levi2234/ChimeraMultiFX/.isolated-review-2026-08-19/board-top.png

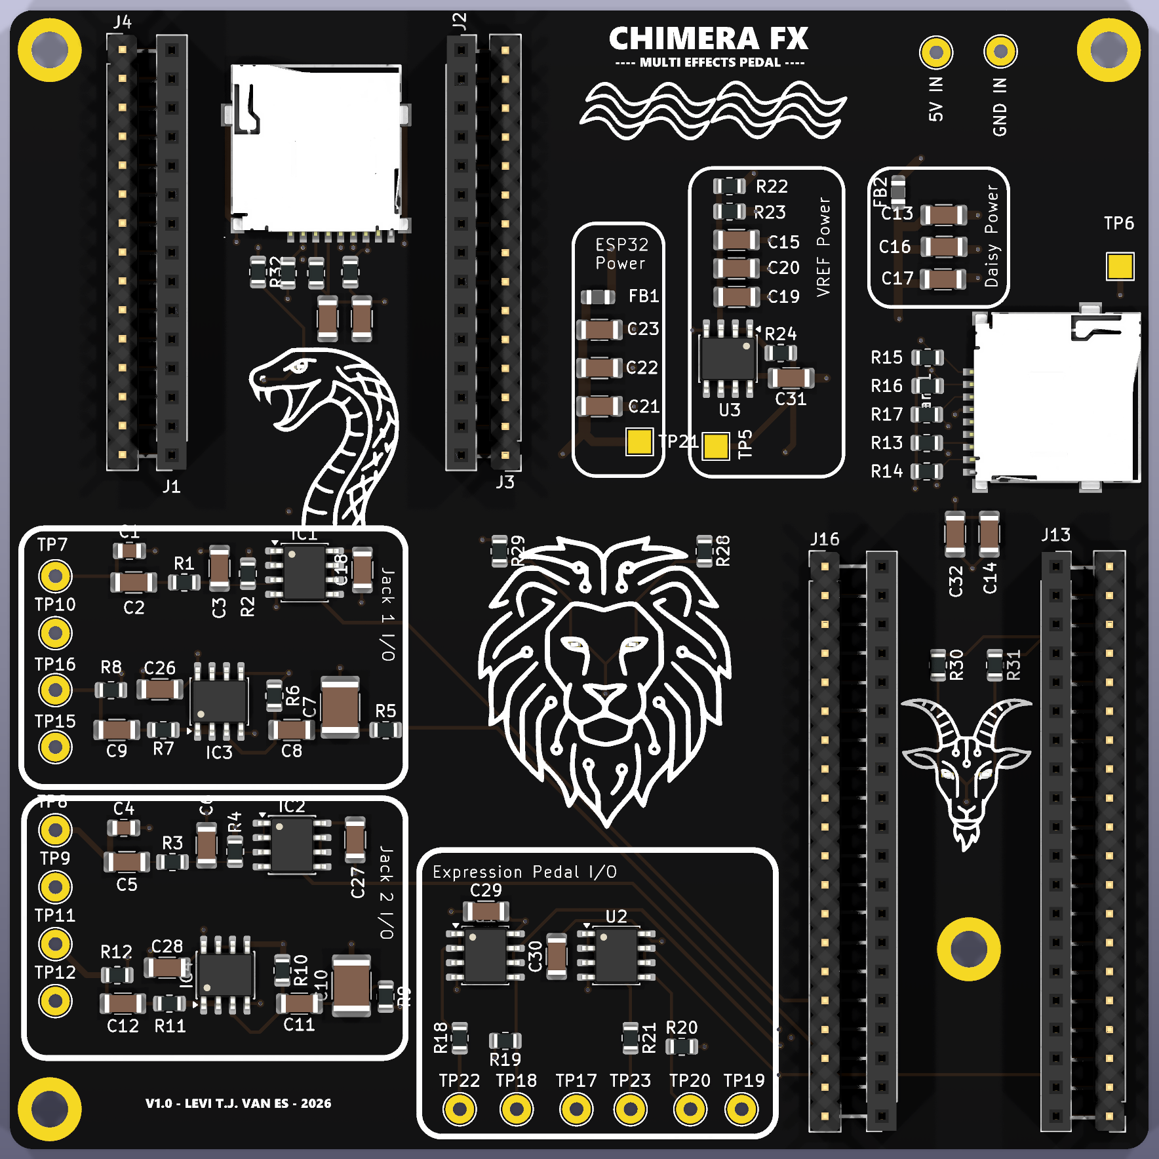
.isolated-review-2026-08-19/board-top.png
