levi2234/ChimeraMultiFX/firmware/daisy/include/effects/time/Delay.h

#pragma once
#include "daisy_seed.h"
#include "Effect.h"
#include <cstdint>
#include <cstring>

// Simple delay line with feedback.
class Delay : public Effect {
public:
    static constexpr uint32_t MAX_DELAY_SAMPLES = 96000 * 2; // 2s @ 96kHz

    void Init(float sample_rate) override {
        sample_rate_   = sample_rate;
        delay_time_    = 0.5f;
        feedback_      = 0.6f;
        mix_           = 0.4f;
        write_ptr_     = 0;
        delay_samples_ = (uint32_t)(delay_time_ * sample_rate_);
        if (delay_samples_ >= MAX_DELAY_SAMPLES)
            delay_samples_ = MAX_DELAY_SAMPLES - 1;

        for (uint32_t i = 0; i < MAX_DELAY_SAMPLES; i++)
            buffer_[i] = 0.0f;
    }

    float Process(float in) override {
        uint32_t read_ptr = (write_ptr_ - delay_samples_ + MAX_DELAY_SAMPLES) % MAX_DELAY_SAMPLES;
        float wet = buffer_[read_ptr];
        buffer_[write_ptr_] = in + (wet * feedback_);
        write_ptr_ = (write_ptr_ + 1) % MAX_DELAY_SAMPLES;
        return (in * (1.0f - mix_)) + (wet * mix_);
    }    const char* GetName() const override { return "delay"; }
    EffectCategory GetCategory() const override { return EffectCategory::Time; }

    void SetParam(const char* name, float value) override {
        if      (strcmp(name, "time") == 0)     SetDelayTime(value);
        else if (strcmp(name, "feedback") == 0) SetFeedback(value);
        else if (strcmp(name, "mix") == 0)      SetMix(value);
    }    float GetParam(const char* name) override {
        if      (strcmp(name, "time") == 0)     return delay_time_;
        else if (strcmp(name, "feedback") == 0) return feedback_;
        else if (strcmp(name, "mix") == 0)      return mix_;
        return 0.f;
    }

    const char* GetParamList() const override { return "time,feedback,mix"; }

    int GetParamCount() const override { return 3; }
    bool GetParamInfo(int index, EffectParamInfo& info) const override {
        switch (index) {
            case 0: info = {"time", "Time", "s", "float", "linear", 0.001f, (MAX_DELAY_SAMPLES - 1) / sample_rate_, 0.5f, 0.001f}; return true;
            case 1: info = {"feedback", "Feedback", "", "float", "linear", 0.0f, 0.95f, 0.6f, 0.01f}; return true;
            case 2: info = {"mix", "Mix", "", "float", "linear", 0.0f, 1.0f, 0.4f, 0.01f}; return true;
            default: return false;
        }
    }

    void SetDelayTime(float sec) {
        delay_time_ = Clamp(sec, 0.001f, (MAX_DELAY_SAMPLES - 1) / sample_rate_);
        delay_samples_ = (uint32_t)(delay_time_ * sample_rate_);
        if (delay_samples_ >= MAX_DELAY_SAMPLES)
            delay_samples_ = MAX_DELAY_SAMPLES - 1;
    }
    void SetFeedback(float fb) { feedback_ = Clamp(fb, 0.0f, 0.95f); }
    void SetMix(float m)       { mix_ = Clamp(m, 0.0f, 1.0f); }

private:
    float    sample_rate_   = 96000.f;
    float    delay_time_    = 0.5f;
    float    feedback_      = 0.6f;
    float    mix_           = 0.4f;
    uint32_t write_ptr_     = 0;
    uint32_t delay_samples_ = 0;

    static inline float DSY_SDRAM_BSS buffer_[MAX_DELAY_SAMPLES];
};
