levi2234/ChimeraMultiFX/firmware/daisy/Effect.h

#pragma once
#include <cstddef>
#include <cstring>

// Effect category tags — used for grouping and UI.
enum class EffectCategory {
    Distortion,
    Modulation,
    Time,
    Dynamics,
    Filter,
};

struct EffectParamInfo {
    const char* name;
    const char* label;
    const char* unit;
    const char* kind;
    const char* scale;
    float min;
    float max;
    float default_value;
    float step;
    const char* options;
};

// Base class for all ChimeraMultiFX effects.
// Each effect implements Init() and Process() and can be hot-swapped at runtime.
class Effect {
public:
    virtual ~Effect() {}

    // Called once when the effect is activated. sample_rate is in Hz.
    virtual void Init(float sample_rate) = 0;

    // Process a single mono sample and return the output.
    virtual float Process(float in) = 0;

    // Friendly name for display/debug purposes.
    virtual const char* GetName() const = 0;

    // Which family this effect belongs to.
    virtual EffectCategory GetCategory() const = 0;    // Parameter access by name — override in each effect for serial control
    virtual void  SetParam(const char* name, float value) { (void)name; (void)value; }
    virtual float GetParam(const char* name) { (void)name; return 0.f; }

    // Boolean parameter access — override for toggle-style params (e.g. "enabled")
    virtual void SetBoolParam(const char* name, bool value) { (void)name; (void)value; }
    virtual bool GetBoolParam(const char* name) { (void)name; return false; }

    // Returns a comma-separated list of parameter names (e.g. "drive,mix,level")
    virtual const char* GetParamList() const { return ""; }

    virtual int GetParamCount() const { return 0; }
    virtual bool GetParamInfo(int index, EffectParamInfo& info) const { (void)index; (void)info; return false; }

    // Per-effect bypass
    bool IsEnabled() const     { return enabled_; }
    void SetEnabled(bool e)    { enabled_ = e; }

    // Convenience: wraps Process() with bypass check
    float Tick(float in) {
        return enabled_ ? Process(in) : in;
    }

protected:
    static float Clamp(float value, float min, float max) {
        if (value < min) return min;
        if (value > max) return max;
        return value;
    }

    static int ClampInt(int value, int min, int max) {
        if (value < min) return min;
        if (value > max) return max;
        return value;
    }

    bool enabled_ = true;
};
