levi2234/ChimeraMultiFX/.agents/skills/kicad/scripts/analyze_pcb.py

#!/usr/bin/env python3
"""
KiCad PCB Layout Analyzer — comprehensive single-pass extraction.

Parses a .kicad_pcb file and outputs structured JSON with:
- Board dimensions and layer stack
- Footprint inventory (components, positions, pads, nets)
- Routing analysis (tracks, vias, zones)
- Net connectivity and unrouted nets
- Design rule summary
- Statistics

Usage:
    python analyze_pcb.py <file.kicad_pcb|file.kicad_pro|dir/> [--output file.json]
"""

import heapq
import json
import math
import os
import sys
from pathlib import Path

sys.path.insert(0, str(Path(__file__).parent))
import re

from sexp_parser import (
    find_all,
    find_first,
    get_at,
    get_property,
    get_value,
    parse_file,
)
from kicad_utils import (is_ground_name, is_power_net_name,
                         load_kicad_pro, extract_pro_net_classes,
                         extract_pro_design_rules, extract_pro_text_variables,
                         load_kicad_dru, load_lib_tables)
from pcb_connectivity import build_connectivity_graph
from finding_schema import compute_trust_summary, sort_findings, assign_finding_ids
from envelopes.pcb import PCBEnvelope
from schema_codec import emit_schema
from inputs_builder import build_inputs, build_compat
from capability_mode import get_capability_mode_ref

ANALYZER_SOURCE = "pcb"

# ---------------------------------------------------------------------------
# Geometry helpers
# ---------------------------------------------------------------------------

def _extract_polygon_coords(pts_node: list) -> list[tuple[float, float]]:
    """Extract (x, y) coordinate tuples from a (pts (xy x y) ...) node."""
    return [(float(xy[1]), float(xy[2])) for xy in find_all(pts_node, "xy")]


def _shoelace_area_from_coords(coords: list[tuple[float, float]]) -> float:
    """Compute polygon area from coordinate list using shoelace formula."""
    n = len(coords)
    if n < 3:
        return 0.0
    area = 0.0
    for i in range(n):
        j = (i + 1) % n
        area += coords[i][0] * coords[j][1] - coords[j][0] * coords[i][1]
    return abs(area) / 2.0


def _shoelace_area(pts_node: list) -> float:
    """Compute polygon area from a (pts (xy x y) ...) S-expression node.

    Returns positive area in mm².
    """
    return _shoelace_area_from_coords(_extract_polygon_coords(pts_node))


def _point_in_polygon(px: float, py: float,
                      polygon: list[tuple[float, float]]) -> bool:
    """Ray-casting point-in-polygon test.

    Returns True if point (px, py) is inside the polygon defined by
    a list of (x, y) vertices.
    """
    n = len(polygon)
    if n < 3:
        return False
    inside = False
    j = n - 1
    for i in range(n):
        xi, yi = polygon[i]
        xj, yj = polygon[j]
        if ((yi > py) != (yj > py)) and \
                (px < (xj - xi) * (py - yi) / (yj - yi) + xi):
            inside = not inside
        j = i
    return inside


def _polygon_bbox(
    coords: list[tuple[float, float]],
) -> tuple[float, float, float, float]:
    """Compute bounding box of a polygon.

    Returns (min_x, min_y, max_x, max_y).
    """
    xs = [p[0] for p in coords]
    ys = [p[1] for p in coords]
    return (min(xs), min(ys), max(xs), max(ys))


class ZoneFills:
    """Spatial index for zone filled polygon data.

    Stores filled polygon coordinates extracted during zone parsing.
    Used for point-in-polygon queries to determine actual copper presence
    at specific locations. Not included in JSON output (coordinates are
    too large — often thousands of vertices per fill region).

    Requires that zones have been filled in KiCad (Edit → Fill All Zones)
    before the PCB file was saved. Stale fills will produce incorrect results.
    """

    def __init__(self) -> None:
        self._fills: list[
            tuple[int, int, str, list[tuple[float, float]],
                  tuple[float, float, float, float]]
        ] = []
        self._next_fill_id = 0

    def add(self, zone_idx: int, layer: str,
            coords: list[tuple[float, float]]) -> None:
        """Register a filled polygon region for spatial queries."""
        bbox = _polygon_bbox(coords)
        fill_id = self._next_fill_id
        self._next_fill_id += 1
        self._fills.append((fill_id, zone_idx, layer, coords, bbox))

    @property
    def has_data(self) -> bool:
        """True if any filled polygon data was loaded."""
        return len(self._fills) > 0

    def zones_at_point(self, x: float, y: float, layer: str,
                       zones: list[dict]) -> list[dict]:
        """Return zone dicts that have filled copper at (x, y) on layer."""
        results = []
        seen: set[int] = set()
        for _fill_id, zone_idx, fill_layer, coords, bbox in self._fills:
            if fill_layer != layer or zone_idx in seen:
                continue
            # Fast bounding box rejection
            if x < bbox[0] or x > bbox[2] or y < bbox[1] or y > bbox[3]:
                continue
            if _point_in_polygon(x, y, coords):
                results.append(zones[zone_idx])
                seen.add(zone_idx)
        return results

    def fill_regions_at_point(self, x: float, y: float, layer: str,
                              zones: list[dict],
                              *,
                              net_name: str | None = None) -> list[tuple[int, int]]:
        """Return ``(fill_id, zone_idx)`` regions containing the point."""
        results: list[tuple[int, int]] = []
        for fill_id, zone_idx, fill_layer, coords, bbox in self._fills:
            if fill_layer != layer:
                continue
            if x < bbox[0] or x > bbox[2] or y < bbox[1] or y > bbox[3]:
                continue
            if not _point_in_polygon(x, y, coords):
                continue
            if net_name is not None and zones[zone_idx].get("net_name", "") != net_name:
                continue
            results.append((fill_id, zone_idx))
        return results

    def has_copper_at(self, x: float, y: float, layer: str) -> bool:
        """Check if any zone has filled copper at (x, y) on layer."""
        for _fill_id, _zone_idx, fill_layer, coords, bbox in self._fills:
            if fill_layer != layer:
                continue
            if x < bbox[0] or x > bbox[2] or y < bbox[1] or y > bbox[3]:
                continue
            if _point_in_polygon(x, y, coords):
                return True
        return False

    def zone_nets_at_point(self, x: float, y: float, layer: str,
                           zones: list[dict]) -> list[str]:
        """Return net names of zones with filled copper at (x, y) on layer."""
        return [z["net_name"] for z in self.zones_at_point(x, y, layer, zones)
                if z.get("net_name")]


def _dist_point_to_segment(px, py, x1, y1, x2, y2):
    """Distance from point (px, py) to line segment (x1,y1)-(x2,y2)."""
    # EQ-098: d = min(||P - (A + t(B-A))||) with t clamped to [0,1]
    # Source: Self-evident — 2D point-to-segment distance (project, clamp, Euclidean).
    dx, dy = x2 - x1, y2 - y1
    if dx == 0 and dy == 0:
        return math.sqrt((px - x1) ** 2 + (py - y1) ** 2)
    t = max(0.0, min(1.0, ((px - x1) * dx + (py - y1) * dy) / (dx * dx + dy * dy)))
    proj_x, proj_y = x1 + t * dx, y1 + t * dy
    return math.sqrt((px - proj_x) ** 2 + (py - proj_y) ** 2)


class CopperPresence:
    """Unified copper presence check across zones, tracks, and pads.

    Given a point (x, y) on a given layer, returns True if any copper
    object is within radius_mm.  Credits zone fills, track segments, and
    pads equally -- all provide valid return-current paths.

    Replaces bare ``ZoneFills.has_copper_at`` point-in-polygon checks
    that hit false negatives in KiCad zone fills (clearance channels
    carved around every track/pad make the filled polygon "swiss cheese";
    a sample point landing inside a clearance channel reports "no copper"
    even when GND fill is < 1 mm away).
    """

    def __init__(self, zone_fills, tracks_segments, footprints):
        self.zone_fills = zone_fills

        # Index track segments by layer for fast lookup
        self._tracks_by_layer = {}
        for seg in tracks_segments or []:
            layer = seg.get('layer')
            if layer:
                self._tracks_by_layer.setdefault(layer, []).append(seg)

        # Index pads by layer -- use absolute position (abs_x, abs_y)
        # and size (width, height) from extract_footprints() output
        self._pads_by_layer = {}
        for fp in footprints or []:
            for pad in fp.get('pads') or []:
                layers = pad.get('layers') or []
                px = pad.get('abs_x')
                py_val = pad.get('abs_y')
                if px is None or py_val is None:
                    continue
                pw = pad.get('width', 0)
                ph = pad.get('height', 0)
                for lyr in layers:
                    self._pads_by_layer.setdefault(lyr, []).append(
                        (px, py_val, pw, ph))

    # EQ-099: Perimeter sample at (x + r·cos(iπ/4), y + r·sin(iπ/4)) for i=0..7
    # Source: Self-evident — 8-point circle sampling at 45° intervals.
    def has_coverage_near(self, x, y, layer, *, radius_mm=0.5):
        """True if any copper on *layer* is within *radius_mm* of (x, y).

        Checks zone fills (center + 8-point perimeter), tracks, and pads.
        """
        zf = self.zone_fills
        if zf is not None and zf.has_data:
            # Center point -- fast path
            if zf.has_copper_at(x, y, layer):
                return True
            # 8-point perimeter at radius_mm
            for i in range(8):
                ang = i * math.pi / 4.0
                px = x + radius_mm * math.cos(ang)
                py = y + radius_mm * math.sin(ang)
                if zf.has_copper_at(px, py, layer):
                    return True

        # Track segments on this layer within radius
        for seg in self._tracks_by_layer.get(layer, []):
            half_w = seg.get('width', 0) / 2.0
            d = _dist_point_to_segment(
                x, y,
                seg.get('x1', 0), seg.get('y1', 0),
                seg.get('x2', 0), seg.get('y2', 0),
            )
            if d <= radius_mm + half_w:
                return True

        # Pads on this layer within radius
        for (pad_x, pad_y, pw, ph) in self._pads_by_layer.get(layer, []):
            half_diag = math.sqrt((pw / 2) ** 2 + (ph / 2) ** 2) if pw and ph else 0
            d = math.sqrt((x - pad_x) ** 2 + (y - pad_y) ** 2)
            if d <= radius_mm + half_diag:
                return True

        return False


def copper_connected(p1: tuple[float, float],
                     p2: tuple[float, float],
                     net: str,
                     layer: str,
                     zone_fills: "ZoneFills",
                     zones: list[dict],
                     *,
                     samples: int = 20) -> bool | None:
    """Check whether two points are joined by continuous same-net copper.

    Uses line-segment sampling through the ``ZoneFills`` spatial index to
    determine if a path between ``p1`` and ``p2`` stays entirely within a
    filled zone on ``net`` and ``layer``. This is a cheap approximation
    of a full copper connectivity graph — sufficient for verifying that
    a via near a thermal pad is actually copper-connected (fillet, flood,
    or cluster pattern) rather than sitting across a clearance slot.

    Args:
        p1: (x, y) of the first point in board coordinates (mm).
        p2: (x, y) of the second point in board coordinates (mm).
        net: Net name both points must share (e.g., "GND", "+3V3").
        layer: Copper layer name (e.g., "F.Cu", "B.Cu", "In1.Cu").
        zone_fills: ZoneFills spatial index from the PCB parser.
        zones: The full zone list the ZoneFills index was built from
            (needed for looking up net names attached to filled regions).
            Must be the same list returned alongside the ZoneFills
            instance during PCB parsing — mismatched pairs produce an
            IndexError deep inside ZoneFills.zones_at_point.
        samples: Number of sample points to test along the line segment,
            including both endpoints. Default 20 gives ~0.26 mm spacing
            on a 5 mm path (5 mm / 19 gaps). Increase for longer paths
            or tighter geometry; decrease for very short distances to
            save work.

    Returns:
        ``True`` if every sampled point along the segment lies in a filled
            zone whose net name matches ``net`` on ``layer``.
        ``False`` if any sample point is outside a same-net filled zone on
            ``layer`` (i.e., verified disconnected at least at that sample).
        ``None`` if the zone fill data is not available — the caller
            cannot distinguish connected from disconnected and should
            fall back to a proximity heuristic or skip the check.

    Limitations (document for consumers):
        - **Thermal relief clearances** can cause false negatives: a
          sample point might land inside the cross-shaped cutout of a
          thermal relief pattern rather than in the surrounding flood,
          even though the pad is electrically connected via the four
          spokes. Consumers that care about thermal-relief patterns
          should use more samples and/or accept a majority-pass rule
          rather than strict all-pass.
        - **Single-layer only.** Does not traverse vias to check
          cross-layer continuity. A pad connected to an inner plane
          through a via will look disconnected from a point on the
          outer layer even if the electrical path is valid. For
          cross-layer continuity verification, use this helper in
          combination with via-layer traversal logic.
        - **Linear sampling.** The function samples along a straight
          line between ``p1`` and ``p2``. Paths that curve around
          obstacles (e.g., a trace that routes around a keep-out) will
          be reported disconnected even though the copper is continuous
          along the routed path. For proximity-style checks (within a
          few mm), linear sampling is appropriate; for long-distance
          connectivity, use a different algorithm.
    """
    if not zone_fills.has_data:
        return None

    if samples < 2:
        samples = 2

    x1, y1 = p1
    x2, y2 = p2
    dx = x2 - x1
    dy = y2 - y1

    for i in range(samples):
        t = i / (samples - 1)
        sx = x1 + t * dx
        sy = y1 + t * dy
        nets_at_point = zone_fills.zone_nets_at_point(sx, sy, layer, zones)
        if net not in nets_at_point:
            return False

    return True


def _arc_length_3pt(sx: float, sy: float, mx: float, my: float,
                    ex: float, ey: float) -> float:
    """Compute arc length from three points (start, mid, end) on a circle."""
    # EQ-044: arc = R × θ from circumcircle (3-point arc length)
    D = 2.0 * (sx * (my - ey) + mx * (ey - sy) + ex * (sy - my))
    if abs(D) < 1e-10:
        # Collinear — treat as straight line
        return math.sqrt((ex - sx) ** 2 + (ey - sy) ** 2)

    ss = sx * sx + sy * sy
    ms = mx * mx + my * my
    es = ex * ex + ey * ey
    ux = (ss * (my - ey) + ms * (ey - sy) + es * (sy - my)) / D
    uy = (ss * (ex - mx) + ms * (sx - ex) + es * (mx - sx)) / D
    R = math.sqrt((sx - ux) ** 2 + (sy - uy) ** 2)

    a_s = math.atan2(sy - uy, sx - ux)
    a_m = math.atan2(my - uy, mx - ux)
    a_e = math.atan2(ey - uy, ex - ux)

    # Normalize angles relative to start
    def _norm(a: float) -> float:
        # EQ-047: Angle normalization to [0, 2π)
        a = (a - a_s) % (2.0 * math.pi)
        return a

    nm = _norm(a_m)
    ne = _norm(a_e)

    # Arc from start to end: two possible arcs (CCW ne, or CW 2π-ne).
    # Choose the one containing mid.
    if ne > 0 and 0 < nm < ne:
        arc_angle = ne
    elif ne > 0:
        arc_angle = 2.0 * math.pi - ne
    else:
        arc_angle = 2.0 * math.pi  # full circle edge case
    return R * arc_angle


def extract_layers(root: list) -> list[dict]:
    """Extract layer definitions."""
    layers_node = find_first(root, "layers")
    if not layers_node:
        return []

    layers = []
    for item in layers_node[1:]:
        if isinstance(item, list) and len(item) >= 3:
            layers.append({
                "number": int(item[0]) if str(item[0]).isdigit() else item[0],
                "name": item[1],
                "type": item[2],
                "alias": item[3] if len(item) > 3 and isinstance(item[3], str) else None,
            })
    return layers


def extract_setup(root: list) -> dict:
    """Extract board setup, stackup, and design rules."""
    setup_node = find_first(root, "setup")
    if not setup_node:
        return {}

    result = {}

    # Board thickness
    general = find_first(root, "general")
    if general:
        thickness = get_value(general, "thickness")
        if thickness:
            result["board_thickness_mm"] = float(thickness)

    # Stackup
    stackup = find_first(setup_node, "stackup")
    if stackup:
        stack_layers = []
        _NUMERIC_STACKUP_KEYS = {"thickness", "epsilon_r", "loss_tangent"}
        for layer in find_all(stackup, "layer"):
            layer_info = {"name": layer[1] if len(layer) > 1 else ""}
            for item in layer[2:]:
                if isinstance(item, list) and len(item) >= 2:
                    key, val = item[0], item[1]
                    if key in _NUMERIC_STACKUP_KEYS:
                        try:
                            val = float(val)
                        except (ValueError, TypeError):
                            pass
                    layer_info[key] = val
            stack_layers.append(layer_info)
        result["stackup"] = stack_layers

    # Design rules from setup
    _float_keys = [
        "pad_to_mask_clearance", "solder_mask_min_width",
        "pad_to_paste_clearance",
    ]
    for key in _float_keys:
        val = get_value(setup_node, key)
        if val:
            result[key] = float(val)

    # Paste clearance ratio
    pcr = get_value(setup_node, "pad_to_paste_clearance_ratio")
    if pcr:
        result["pad_to_paste_clearance_ratio"] = float(pcr)

    # Copper finish from stackup
    if stackup:
        cf = get_value(stackup, "copper_finish")
        if cf:
            result["copper_finish"] = cf
        dc = get_value(stackup, "dielectric_constraints")
        if dc:
            result["dielectric_constraints"] = dc

    # Legacy teardrops flag
    if general:
        lt = get_value(general, "legacy_teardrops")
        if lt:
            result["legacy_teardrops"] = lt

    # Soldermask bridges
    smb = get_value(setup_node, "allow_soldermask_bridges_in_footprints")
    if smb:
        result["allow_soldermask_bridges"] = smb

    # Design rules from pcbplotparams or design_settings (varies by version)
    # KiCad 9 stores rules in the .kicad_pro file, but some appear in the PCB
    # under (setup (design_settings ...)) or directly
    ds = find_first(setup_node, "design_settings") or setup_node
    for key in ["min_clearance", "min_track_width", "min_via_diameter",
                "min_via_drill", "min_uvia_diameter", "min_uvia_drill",
                "min_through_hole_pad", "min_hole_clearance"]:
        val = get_value(ds, key)
        if val:
            result.setdefault("design_rules", {})[key] = float(val)

    return result


def extract_nets(root: list) -> dict[int, str]:
    """Extract net declarations.

    KiCad ≤9: top-level (net number "name") declarations.
    KiCad 10: no declarations — call _build_net_mapping() after extraction.
    """
    nets = {}
    for item in root:
        if isinstance(item, list) and len(item) >= 3 and item[0] == "net":
            try:
                net_num = int(item[1])
            except (ValueError, TypeError):
                continue  # KiCad 10 has no numeric net declarations
            net_name = item[2]
            nets[net_num] = net_name
    return nets


# KiCad 10 net format helpers — nets are identified by name, not number.
_net_name_to_id: dict[str, int] = {}


def _net_id(val: str | None) -> int:
    """Convert a net value to an integer ID.

    KiCad ≤9: val is a numeric string like "3" → returns 3.
    KiCad 10: val is a net name like "+3.3V" → looks up synthetic ID.
    """
    if not val:
        return 0
    try:
        return int(val)
    except (ValueError, TypeError):
        return _net_name_to_id.get(val, 0)


def _build_net_mapping(footprints: list[dict], tracks: dict, vias: dict,
                       zones: list[dict]) -> dict[int, str]:
    """Build synthetic net ID mapping for KiCad 10 (no net declarations).

    Scans all pads, tracks, vias, and zones for unique net names and assigns
    sequential integer IDs. Returns the same dict[int, str] format as
    extract_nets() for backward compatibility.
    """
    global _net_name_to_id
    names: set[str] = set()
    for fp in footprints:
        for pad in fp.get("pads", []):
            n = pad.get("net_name", "")
            if n:
                names.add(n)
    for seg in tracks.get("segments", []):
        n = seg.get("_net_name", "")
        if n:
            names.add(n)
    for arc in tracks.get("arcs", []):
        n = arc.get("_net_name", "")
        if n:
            names.add(n)
    for v in vias.get("vias", []):
        n = v.get("_net_name", "")
        if n:
            names.add(n)
    for z in zones:
        n = z.get("net_name", "")
        if n:
            names.add(n)
    # Assign sequential IDs (0 = unconnected, 1+ = real nets)
    net_names: dict[int, str] = {0: ""}
    _net_name_to_id = {"": 0}
    for i, name in enumerate(sorted(names), start=1):
        net_names[i] = name
        _net_name_to_id[name] = i
    return net_names


def extract_footprints(root: list) -> list[dict]:
    """Extract all placed footprints with pad details.

    Handles both KiCad 6+ (footprint ...) and KiCad 5 (module ...) formats.
    """
    # EQ-060: x'=x·cosθ-y·sinθ, y'=x·sinθ+y·cosθ (2D rotation)
    footprints = []

    # KiCad 6+: (footprint ...), KiCad 5: (module ...)
    fp_nodes = find_all(root, "footprint") or find_all(root, "module")

    for fp in fp_nodes:
        fp_lib = fp[1] if len(fp) > 1 else ""
        at = get_at(fp)
        x, y, angle = at if at else (0, 0, 0)

        layer = get_value(fp, "layer") or "F.Cu"

        # KiCad 6+: (property "Reference" "R1"), KiCad 5: (fp_text reference "R1")
        ref = get_property(fp, "Reference") or ""
        value = get_property(fp, "Value") or ""
        if not ref:
            for ft in find_all(fp, "fp_text"):
                if len(ft) >= 3:
                    if ft[1] == "reference":
                        # Some footprints have no text after the field name —
                        # ft[2] is then an attribute s-expression, not a string.
                        # Coerce to empty string in that case (KH-326).
                        ref = ft[2] if isinstance(ft[2], str) else ""
                    elif ft[1] == "value":
                        value = ft[2] if isinstance(ft[2], str) else ""

        mpn = get_property(fp, "MPN") or get_property(fp, "Mfg Part") or ""

        # Determine SMD vs through-hole + extended attributes
        attr_node = find_first(fp, "attr")
        attr_flags: list[str] = []
        if attr_node and len(attr_node) > 1:
            attr_flags = [a for a in attr_node[1:] if isinstance(a, str)]
            attr = attr_flags[0] if attr_flags else "smd"
        else:
            # Infer from pad types if attr not present (KiCad 5)
            has_tht = any(p[2] == "thru_hole" for p in find_all(fp, "pad") if len(p) > 2)
            attr = "through_hole" if has_tht else "smd"
            # KiCad 5 uses "virtual" for board-only items
            if attr_node and len(attr_node) > 1 and attr_node[1] == "virtual":
                attr = "smd"
                attr_flags = ["virtual"]

        is_dnp = "dnp" in attr_flags
        is_board_only = "board_only" in attr_flags or "virtual" in attr_flags
        exclude_from_bom = "exclude_from_bom" in attr_flags or is_board_only
        exclude_from_pos = "exclude_from_pos_files" in attr_flags or is_board_only

        # Schematic cross-reference (KiCad 6+)
        sch_path = get_value(fp, "path") or ""
        sch_sheetname = get_value(fp, "sheetname") or ""
        sch_sheetfile = get_value(fp, "sheetfile") or ""

        # Net tie pad groups
        net_tie_node = find_first(fp, "net_tie_pad_groups")
        net_tie_groups = None
        if net_tie_node and len(net_tie_node) > 1:
            net_tie_groups = net_tie_node[1]

        # Extended properties (MPN, manufacturer, etc.)
        manufacturer = get_property(fp, "Manufacturer") or ""
        digikey_pn = get_property(fp, "DigiKey Part") or ""
        description = get_property(fp, "Description") or ""

        # 3D model references
        models = []
        for model in find_all(fp, "model"):
            if len(model) > 1:
                models.append(model[1])

        # Extract pads
        pads = []
        for pad in find_all(fp, "pad"):
            if len(pad) < 4:
                continue
            pad_num = pad[1]
            pad_type = pad[2]  # smd, thru_hole, np_thru_hole
            pad_shape = pad[3]  # circle, rect, oval, roundrect, custom

            pad_at = get_at(pad)
            pad_size = find_first(pad, "size")
            pad_drill = find_first(pad, "drill")
            pad_net = find_first(pad, "net")
            pad_layers = find_first(pad, "layers")

            pad_info = {
                "number": pad_num,
                "type": pad_type,
                "shape": pad_shape,
            }

            if pad_at:
                # Pad position is relative to footprint; compute absolute
                px, py = pad_at[0], pad_at[1]
                pad_angle = pad_at[2]
                # KiCad PCB footprint rotations are clockwise in board coords.
                # Use the negative angle to map local pad offsets into absolute
                # board space; using +angle mirrors rotated footprints.
                if angle != 0:
                    rad = math.radians(-angle)
                    rpx = px * math.cos(rad) - py * math.sin(rad)
                    rpy = px * math.sin(rad) + py * math.cos(rad)
                    px, py = rpx, rpy
                pad_info["abs_x"] = round(x + px, 4)
                pad_info["abs_y"] = round(y + py, 4)
                if pad_angle != 0:
                    pad_info["angle"] = pad_angle

            if pad_size and len(pad_size) >= 3:
                pad_info["width"] = float(pad_size[1])
                pad_info["height"] = float(pad_size[2])

            if pad_drill and len(pad_drill) >= 2:
                # Drill can be (drill D) or (drill oval W H) or (drill D (offset X Y))
                drill_val = pad_drill[1]
                if drill_val == "oval" and len(pad_drill) >= 3:
                    pad_info["drill_shape"] = "oval"
                    pad_info["drill"] = float(pad_drill[2])
                    if len(pad_drill) >= 4 and isinstance(pad_drill[3], str):
                        pad_info["drill_h"] = float(pad_drill[3])
                else:
                    try:
                        pad_info["drill"] = float(drill_val)
                    except (ValueError, TypeError):
                        pass  # skip malformed drill entries

            if pad_net and len(pad_net) >= 3:
                # KiCad ≤9: (net number "name")
                pad_info["net_number"] = _net_id(pad_net[1])
                pad_info["net_name"] = pad_net[2]
            elif pad_net and len(pad_net) == 2:
                # KiCad 10: (net "name") — no numeric ID
                pad_info["net_name"] = pad_net[1]
                pad_info["net_number"] = _net_id(pad_net[1])

            if pad_layers and len(pad_layers) > 1:
                pad_info["layers"] = [l for l in pad_layers[1:] if isinstance(l, str)]

            # Pin function and type (from schematic, carried into PCB)
            pinfunc = get_value(pad, "pinfunction")
            pintype = get_value(pad, "pintype")
            if pinfunc:
                pad_info["pinfunction"] = pinfunc
            if pintype:
                pad_info["pintype"] = pintype

            # Per-pad zone connection override
            zc = get_value(pad, "zone_connect")
            if zc is not None:
                pad_info["zone_connect"] = int(zc)

            # Custom pad shape — flag it and estimate copper area from primitives
            if pad_shape == "custom":
                pad_info["is_custom"] = True
                primitives = find_first(pad, "primitives")
                if primitives:
                    custom_area = 0.0
                    for prim in find_all(primitives, "gr_poly"):
                        pts = find_first(prim, "pts")
                        if pts:
                            custom_area += _shoelace_area(pts)
                    if custom_area > 0:
                        pad_info["custom_copper_area_mm2"] = round(custom_area, 3)

            # Pad-level solder mask/paste overrides
            sm_margin = get_value(pad, "solder_mask_margin")
            sp_margin = get_value(pad, "solder_paste_margin")
            sp_ratio = get_value(pad, "solder_paste_margin_ratio")
            if sm_margin:
                pad_info["solder_mask_margin"] = float(sm_margin)
            if sp_margin:
                pad_info["solder_paste_margin"] = float(sp_margin)
            if sp_ratio:
                pad_info["solder_paste_ratio"] = float(sp_ratio)

            pads.append(pad_info)

        # Extract courtyard geometry: bounding box + chained outline polygons
        crtyd_pts: list[tuple[float, float]] = []
        crtyd_segs: list[tuple[tuple[float, float], tuple[float, float]]] = []
        crtyd_polys: list[list[tuple[float, float]]] = []
        crtyd_unchainable = False  # arcs/circles → polygon set would be incomplete

        def _fp_to_abs(lx: float, ly: float) -> tuple[float, float]:
            if angle != 0:
                rad = math.radians(-angle)
                rx = lx * math.cos(rad) - ly * math.sin(rad)
                ry = lx * math.sin(rad) + ly * math.cos(rad)
                lx, ly = rx, ry
            return (x + lx, y + ly)

        for gtype in ("fp_line", "fp_rect", "fp_circle", "fp_poly", "fp_arc"):
            for item in find_all(fp, gtype):
                item_layer = get_value(item, "layer")
                if not item_layer or "CrtYd" not in item_layer:
                    continue
                # fp_poly: extract all vertex coordinates
                if gtype == "fp_poly":
                    pts = find_first(item, "pts")
                    if pts:
                        poly = []
                        for xy in find_all(pts, "xy"):
                            if len(xy) >= 3:
                                poly.append(_fp_to_abs(float(xy[1]), float(xy[2])))
                        if len(poly) >= 3:
                            crtyd_polys.append(poly)
                        crtyd_pts.extend(poly)
                    continue
                if gtype == "fp_line":
                    p1 = find_first(item, "start")
                    p2 = find_first(item, "end")
                    if p1 and p2 and len(p1) >= 3 and len(p2) >= 3:
                        seg_a = _fp_to_abs(float(p1[1]), float(p1[2]))
                        seg_b = _fp_to_abs(float(p2[1]), float(p2[2]))
                        crtyd_segs.append((seg_a, seg_b))
                        crtyd_pts.extend((seg_a, seg_b))
                    continue
                if gtype == "fp_rect":
                    p1 = find_first(item, "start")
                    p2 = find_first(item, "end")
                    if p1 and p2 and len(p1) >= 3 and len(p2) >= 3:
                        sx, sy = float(p1[1]), float(p1[2])
                        ex, ey = float(p2[1]), float(p2[2])
                        corners = [_fp_to_abs(cx_, cy_) for cx_, cy_ in
                                   ((sx, sy), (ex, sy), (ex, ey), (sx, ey))]
                        crtyd_polys.append(corners)
                        crtyd_pts.extend(corners)
                    continue
                # fp_circle / fp_arc: bbox contribution only — polygon set
                # stays disabled so overlap falls back to the AABB (KH-350)
                crtyd_unchainable = True
                for key in ("start", "end", "center", "mid"):
                    node = find_first(item, key)
                    if node and len(node) >= 3:
                        crtyd_pts.append(_fp_to_abs(float(node[1]), float(node[2])))

        if crtyd_segs and not crtyd_unchainable:
            _chained = _chain_segments(crtyd_segs)
            if _chained:
                crtyd_polys.extend(_chained)
            else:
                crtyd_unchainable = True

        fp_entry: dict = {
            "library": fp_lib,
            "reference": ref,
            "value": value,
            "mpn": mpn,
            "x": x,
            "y": y,
            "angle": angle,
            "layer": layer,
            "type": attr,
            "pad_count": len(pads),
            "pads": pads,
        }

        # Extended attributes
        if is_dnp:
            fp_entry["dnp"] = True
        if is_board_only:
            fp_entry["board_only"] = True
        if exclude_from_bom:
            fp_entry["exclude_from_bom"] = True
        if exclude_from_pos:
            fp_entry["exclude_from_pos"] = True

        # Schematic cross-reference
        if sch_path:
            fp_entry["sch_path"] = sch_path
        if sch_sheetname:
            fp_entry["sheetname"] = sch_sheetname
        if sch_sheetfile:
            fp_entry["sheetfile"] = sch_sheetfile

        # Net tie
        if net_tie_groups:
            fp_entry["net_tie_pad_groups"] = net_tie_groups

        # Extended properties
        if manufacturer:
            fp_entry["manufacturer"] = manufacturer
        if digikey_pn:
            fp_entry["digikey_pn"] = digikey_pn
        if description:
            fp_entry["description"] = description

        # 3D models
        if models:
            fp_entry["models_3d"] = models

        if crtyd_pts:
            cxs = [p[0] for p in crtyd_pts]
            cys = [p[1] for p in crtyd_pts]
            fp_entry["courtyard"] = {
                "min_x": round(min(cxs), 3), "min_y": round(min(cys), 3),
                "max_x": round(max(cxs), 3), "max_y": round(max(cys), 3),
            }
            if crtyd_polys and not crtyd_unchainable:
                fp_entry["courtyard_poly"] = [
                    [[round(vx_, 3), round(vy_, 3)] for vx_, vy_ in poly]
                    for poly in crtyd_polys
                ]

        footprints.append(fp_entry)

    return footprints


def _chain_segments(segs: list, tol: float = 0.01) -> list | None:
    """Chain undirected 2D segments into closed loops (KH-350).

    Returns a list of polygons (each a list of (x, y) vertices, implicit
    closure) or None when any chain fails to close within tolerance —
    callers then keep the AABB-only behavior.
    """
    def _close(p, q):
        return abs(p[0] - q[0]) <= tol and abs(p[1] - q[1]) <= tol

    remaining = [s for s in segs if not _close(s[0], s[1])]
    polys = []
    while remaining:
        a, b = remaining.pop()
        path = [a, b]
        while not _close(path[0], path[-1]):
            tail = path[-1]
            for i, (p, q) in enumerate(remaining):
                if _close(p, tail):
                    path.append(q)
                    break
                if _close(q, tail):
                    path.append(p)
                    break
            else:
                return None  # open chain
            remaining.pop(i)
        poly = path[:-1]
        if len(poly) < 3:
            return None
        polys.append(poly)
    return polys


def _point_in_polys(px: float, py: float, polys: list) -> bool:
    """Even-odd ray-casting membership over a list of polygons."""
    inside = False
    for poly in polys:
        n = len(poly)
        j = n - 1
        for i in range(n):
            xi, yi = poly[i][0], poly[i][1]
            xj, yj = poly[j][0], poly[j][1]
            if (yi > py) != (yj > py):
                if px < (xj - xi) * (py - yi) / (yj - yi) + xi:
                    inside = not inside
            j = i
    return inside


def _refined_overlap_mm2(polys_a: list, polys_b: list,
                         ix1: float, iy1: float, ix2: float, iy2: float,
                         samples: int = 24) -> float:
    """True courtyard overlap area inside the AABB-intersection box,
    estimated by grid-sampling membership in both polygon sets (KH-350)."""
    w = ix2 - ix1
    h = iy2 - iy1
    if w <= 0 or h <= 0:
        return 0.0
    hits = 0
    for i in range(samples):
        px = ix1 + (i + 0.5) * w / samples
        for j in range(samples):
            py = iy1 + (j + 0.5) * h / samples
            if (_point_in_polys(px, py, polys_a)
                    and _point_in_polys(px, py, polys_b)):
                hits += 1
    return w * h * hits / (samples * samples)


def extract_tracks(root: list) -> dict:
    """Extract track segments with statistics."""
    segments = []
    for seg in find_all(root, "segment"):
        start = find_first(seg, "start")
        end = find_first(seg, "end")
        width = get_value(seg, "width")
        layer = get_value(seg, "layer")
        net = get_value(seg, "net")

        if start and end:
            seg_info = {
                "x1": float(start[1]), "y1": float(start[2]),
                "x2": float(end[1]), "y2": float(end[2]),
                "width": float(width) if width else 0,
                "layer": layer or "",
                "net": _net_id(net),
            }
            if net and not net.lstrip("-").isdigit():
                seg_info["_net_name"] = net  # KiCad 10: stash for mapping build
            segments.append(seg_info)

    # Also extract arcs
    arcs = []
    for arc in find_all(root, "arc"):
        start = find_first(arc, "start")
        mid = find_first(arc, "mid")
        end = find_first(arc, "end")
        width = get_value(arc, "width")
        layer = get_value(arc, "layer")
        net = get_value(arc, "net")

        if start and end:
            arc_info = {
                "start": [float(start[1]), float(start[2])],
                "mid": [float(mid[1]), float(mid[2])] if mid else None,
                "end": [float(end[1]), float(end[2])],
                "width": float(width) if width else 0,
                "layer": layer or "",
                "net": _net_id(net),
            }
            if net and not net.lstrip("-").isdigit():
                arc_info["_net_name"] = net
            arcs.append(arc_info)

    # Width statistics
    widths = {}
    for seg in segments:
        w = seg["width"]
        widths[w] = widths.get(w, 0) + 1
    for arc in arcs:
        w = arc["width"]
        widths[w] = widths.get(w, 0) + 1

    # Layer distribution
    layer_dist = {}
    for seg in segments:
        l = seg["layer"]
        layer_dist[l] = layer_dist.get(l, 0) + 1
    for arc in arcs:
        l = arc["layer"]
        layer_dist[l] = layer_dist.get(l, 0) + 1

    return {
        "segment_count": len(segments),
        "arc_count": len(arcs),
        "total_count": len(segments) + len(arcs),
        "width_distribution": widths,
        "layer_distribution": layer_dist,
        "segments": segments,
        "arcs": arcs,
    }


def extract_vias(root: list) -> dict:
    """Extract vias with statistics."""
    vias = []
    for via in find_all(root, "via"):
        at = get_at(via)
        size = get_value(via, "size")
        drill = get_value(via, "drill")
        net = get_value(via, "net")
        layers_node = find_first(via, "layers")

        # Via type is a bare token between 'via' and the first sub-list,
        # not a (type X) sublist. KiCad writers emit:
        #   Through: (via (at ...) ...)                — no token
        #   Blind:   (via blind (at ...) ...)
        #   Buried:  (via buried (at ...) ...)         — new in 10.0
        #   Micro:   (via micro (at ...) ...)
        via_type = "through"
        for child in via[1:]:
            if isinstance(child, str) and child in ("blind", "buried", "micro"):
                via_type = child
                break
            if isinstance(child, list):
                # First sub-list ends the bare-token region
                break

        via_info = {
            "x": at[0] if at else 0,
            "y": at[1] if at else 0,
            "size": float(size) if size else 0,
            "drill": float(drill) if drill else 0,
            "net": _net_id(net),
            "type": via_type,  # always emit; downstream defaults no longer needed
        }
        if net and not net.lstrip("-").isdigit():
            via_info["_net_name"] = net
        if layers_node and len(layers_node) > 1:
            via_info["layers"] = [l for l in layers_node[1:] if isinstance(l, str)]
        # Free (unanchored) vias — typically stitching or thermal
        if get_value(via, "free") == "yes":
            via_info["free"] = True
        # Via tenting
        tenting = find_first(via, "tenting")
        if tenting and len(tenting) > 1:
            via_info["tenting"] = [t for t in tenting[1:] if isinstance(t, str)]

        vias.append(via_info)

    # Size distribution
    sizes = {}
    for v in vias:
        key = f"{v['size']}/{v['drill']}"
        sizes[key] = sizes.get(key, 0) + 1

    return {
        "count": len(vias),
        "size_distribution": sizes,
        "vias": vias,
    }


def extract_zones(root: list) -> tuple[list[dict], ZoneFills]:
    """Extract copper zones with outline and filled polygon area/spatial data.

    Computes:
    - outline_area_mm2: area of the user-drawn zone boundary
    - outline_bbox: bounding box of the zone outline [min_x, min_y, max_x, max_y]
    - filled_area_mm2: total copper fill area (sum of all filled_polygon regions)
    - filled_bbox: bounding box of all filled polygons combined
    - fill_ratio: filled_area / outline_area (1.0 = fully filled, <1.0 = has gaps)
    - filled_layers: per-layer filled area breakdown
    - is_filled: whether the zone has been filled (has filled_polygon data)

    Returns:
        (zones, zone_fills) — zone_fills is a spatial index for point-in-polygon
        queries against the filled copper. The filled polygon coordinates are
        kept in memory (not in the JSON output) because they can be very large.
        Zone fills reflect the last time Fill All Zones was run in KiCad.
    """
    zones = []
    zone_fills = ZoneFills()
    for zone_idx, zone in enumerate(find_all(root, "zone")):
        net = get_value(zone, "net")
        net_name = get_value(zone, "net_name")
        layer = get_value(zone, "layer")
        layers_node = find_first(zone, "layers")

        # Zone properties
        connect_pads = find_first(zone, "connect_pads")
        clearance = None
        pad_connection = None
        if connect_pads:
            cl = get_value(connect_pads, "clearance")
            clearance = float(cl) if cl else None
            # Connection type: first bare string after "connect_pads" keyword
            for cp_item in connect_pads[1:]:
                if isinstance(cp_item, str) and cp_item in (
                        "yes", "no", "thru_hole_only", "full", "thermal_reliefs"):
                    pad_connection = cp_item
                    break

        # Keepout zone detection
        keepout = find_first(zone, "keepout")
        keepout_restrictions = None
        if keepout:
            keepout_restrictions = {}
            for restriction in ("tracks", "vias", "pads", "copperpour", "footprints"):
                val = get_value(keepout, restriction)
                if val:
                    keepout_restrictions[restriction] = val

        # Zone priority
        priority = get_value(zone, "priority")

        # Zone name (user-assigned)
        zone_name = get_value(zone, "name")

        min_thickness = get_value(zone, "min_thickness")
        fill = find_first(zone, "fill")
        thermal_gap = None
        thermal_bridge = None
        is_filled = False
        if fill:
            tg = get_value(fill, "thermal_gap")
            tb = get_value(fill, "thermal_bridge_width")
            thermal_gap = float(tg) if tg else None
            thermal_bridge = float(tb) if tb else None
            # "yes" in fill node means the zone has been filled
            is_filled = "yes" in fill
            if not is_filled:
                fill_mode = get_value(fill, "mode")
                if fill_mode in ("solid", "hatch"):
                    is_filled = True

        # Zone outline area and bounding box
        outline_area = 0.0
        outline_point_count = 0
        outline_bbox = None
        polygon = find_first(zone, "polygon")
        if polygon:
            pts = find_first(polygon, "pts")
            if pts:
                outline_coords = _extract_polygon_coords(pts)
                outline_point_count = len(outline_coords)
                outline_area = _shoelace_area_from_coords(outline_coords)
                if outline_coords:
                    outline_bbox = _polygon_bbox(outline_coords)

        # Filled polygon areas + spatial data for point-in-polygon queries
        filled_layers: dict[str, float] = {}
        total_filled_area = 0.0
        fill_count = 0
        filled_min_x = float('inf')
        filled_min_y = float('inf')
        filled_max_x = float('-inf')
        filled_max_y = float('-inf')
        for fp_node in find_all(zone, "filled_polygon"):
            fp_layer = get_value(fp_node, "layer") or layer or ""
            fp_pts = find_first(fp_node, "pts")
            if fp_pts:
                coords = _extract_polygon_coords(fp_pts)
                area = _shoelace_area_from_coords(coords)
                filled_layers[fp_layer] = filled_layers.get(fp_layer, 0.0) + area
                total_filled_area += area
                fill_count += 1
                # Store coordinates for spatial queries
                zone_fills.add(zone_idx, fp_layer, coords)
                # Track overall filled bounding box
                for cx, cy in coords:
                    if cx < filled_min_x:
                        filled_min_x = cx
                    if cy < filled_min_y:
                        filled_min_y = cy
                    if cx > filled_max_x:
                        filled_max_x = cx
                    if cy > filled_max_y:
                        filled_max_y = cy

        zone_layers = []
        if layers_node and len(layers_node) > 1:
            zone_layers = [l for l in layers_node[1:] if isinstance(l, str)]
        elif layer:
            zone_layers = [layer]

        # Compute filled bounding box (None if no fill data)
        filled_bbox = None
        if fill_count > 0 and filled_min_x != float('inf'):
            filled_bbox = (
                round(filled_min_x, 3), round(filled_min_y, 3),
                round(filled_max_x, 3), round(filled_max_y, 3),
            )

        # KiCad ≤9: (net number) + (net_name "name")
        # KiCad 10: (net "name"), no net_name node
        if net and not net.lstrip("-").isdigit():
            # KiCad 10: net value is the name itself
            net_name = net
        zone_info: dict = {
            "net": _net_id(net),
            "net_name": net_name or "",
            "layers": zone_layers,
            "clearance": clearance,
            "min_thickness": float(min_thickness) if min_thickness else None,
            "thermal_gap": thermal_gap,
            "thermal_bridge_width": thermal_bridge,
            "outline_points": outline_point_count,
            "outline_area_mm2": round(outline_area, 2),
            "is_filled": is_filled or fill_count > 0,
        }

        if outline_bbox:
            zone_info["outline_bbox"] = [round(v, 3) for v in outline_bbox]

        if keepout_restrictions:
            zone_info["is_keepout"] = True
            zone_info["keepout"] = keepout_restrictions
        if priority is not None:
            zone_info["priority"] = int(priority)
        if zone_name:
            zone_info["name"] = zone_name
        if pad_connection:
            zone_info["pad_connection"] = pad_connection

        if fill_count > 0:
            zone_info["filled_area_mm2"] = round(total_filled_area, 2)
            zone_info["fill_region_count"] = fill_count
            if filled_bbox:
                zone_info["filled_bbox"] = list(filled_bbox)
            if outline_area > 0:
                zone_info["fill_ratio"] = round(
                    total_filled_area / outline_area, 3)
            if len(filled_layers) > 1:
                zone_info["filled_layers"] = {
                    k: round(v, 2) for k, v in sorted(filled_layers.items())
                }

        zones.append(zone_info)

    return zones, zone_fills


def _extract_keepout_zones(zones: list[dict],
                           footprints: list[dict]) -> list[dict]:
    """Surface keepout/rule areas as a dedicated section.

    Filters keepout zones from the main zones array and enriches each
    with nearby component references (footprints within 5mm of the zone
    bounding box).
    """
    keepouts = []
    for z in zones:
        if not z.get('is_keepout'):
            continue
        bbox = z.get('outline_bbox')
        entry = {
            'name': z.get('name', ''),
            'layers': z.get('layers', []),
            'restrictions': z.get('keepout', {}),
            'bounding_box': bbox,
            'area_mm2': z.get('outline_area_mm2', 0),
            # Net the keepout is associated with — items on this net are
            # ALLOWED inside the keepout (KiCad rule-area semantic). 0 / ""
            # means "no specific net" → keepout applies to all items.
            'net': z.get('net', 0),
            'net_name': z.get('net_name', ''),
        }
        # Find footprints near this keepout zone
        if bbox and len(bbox) == 4:
            margin = 5.0  # mm
            bx_min, by_min, bx_max, by_max = bbox
            nearby = []
            for fp in footprints:
                fx = fp.get('x', 0)
                fy = fp.get('y', 0)
                if (bx_min - margin <= fx <= bx_max + margin
                        and by_min - margin <= fy <= by_max + margin):
                    nearby.append(fp.get('reference', ''))
            entry['nearby_components'] = sorted(
                r for r in nearby if r)
        keepouts.append(entry)
    return keepouts


def extract_board_outline(root: list) -> dict:
    """Extract board outline from Edge.Cuts layer."""
    edges = []

    for item_type in ["gr_line", "gr_arc", "gr_circle", "gr_rect", "gr_poly", "gr_curve"]:
        for item in find_all(root, item_type):
            layer = get_value(item, "layer")
            if layer != "Edge.Cuts":
                continue

            if item_type == "gr_line":
                start = find_first(item, "start")
                end = find_first(item, "end")
                if start and end:
                    edges.append({
                        "type": "line",
                        "start": [float(start[1]), float(start[2])],
                        "end": [float(end[1]), float(end[2])],
                    })
            elif item_type == "gr_arc":
                start = find_first(item, "start")
                mid = find_first(item, "mid")
                end = find_first(item, "end")
                if start and end:
                    edges.append({
                        "type": "arc",
                        "start": [float(start[1]), float(start[2])],
                        "mid": [float(mid[1]), float(mid[2])] if mid else None,
                        "end": [float(end[1]), float(end[2])],
                    })
            elif item_type == "gr_rect":
                start = find_first(item, "start")
                end = find_first(item, "end")
                if start and end:
                    edges.append({
                        "type": "rect",
                        "start": [float(start[1]), float(start[2])],
                        "end": [float(end[1]), float(end[2])],
                    })
            elif item_type == "gr_circle":
                center = find_first(item, "center")
                end = find_first(item, "end")
                if center and end:
                    edges.append({
                        "type": "circle",
                        "center": [float(center[1]), float(center[2])],
                        "end": [float(end[1]), float(end[2])],
                    })
            elif item_type == "gr_poly":
                pts = find_first(item, "pts")
                if pts:
                    points = []
                    for xy in pts:
                        if isinstance(xy, list) and len(xy) >= 3 and xy[0] == "xy":
                            points.append([float(xy[1]), float(xy[2])])
                    if points:
                        edges.append({"type": "polygon", "points": points})
            elif item_type == "gr_curve":
                pts = find_first(item, "pts")
                if pts:
                    points = []
                    for xy in pts:
                        if isinstance(xy, list) and len(xy) >= 3 and xy[0] == "xy":
                            points.append([float(xy[1]), float(xy[2])])
                    if points:
                        edges.append({"type": "curve", "points": points})

    # Compute bounding box from all edge points
    all_x = []
    all_y = []
    for e in edges:
        if e["type"] == "circle":
            # Circle: bounding box is center ± radius
            cx, cy = e["center"]
            ex, ey = e["end"]
            r = math.sqrt((ex - cx) ** 2 + (ey - cy) ** 2)
            all_x.extend([cx - r, cx + r])
            all_y.extend([cy - r, cy + r])
            continue
        if e["type"] == "arc" and e.get("mid"):
            # EQ-100: Arc bounding box — 3-point circumscribed circle via
            #   determinant, then check whether arc sweep (via atan2 of
            #   endpoints + midpoint) crosses any cardinal axis at 0, π/2, π,
            #   3π/2. Crossings extend the bbox to ±r.
            # Source: Standard computational geometry. Circumscribed circle
            #   from 3 points:
            #   https://en.wikipedia.org/wiki/Circumscribed_circle#Circumscribed_circles_of_triangles
            #   Arc bbox via cardinal-crossing test is a well-known CAD/CAM
            #   technique.
            # Arc: include start/end plus any cardinal extrema the arc passes through
            sx, sy = e["start"]
            mx, my = e["mid"]
            ex, ey = e["end"]
            all_x.extend([sx, ex])
            all_y.extend([sy, ey])
            # Compute center and radius from 3 points
            D = 2.0 * (sx * (my - ey) + mx * (ey - sy) + ex * (sy - my))
            if abs(D) > 1e-10:
                ss = sx * sx + sy * sy
                ms = mx * mx + my * my
                es = ex * ex + ey * ey
                ucx = (ss * (my - ey) + ms * (ey - sy) + es * (sy - my)) / D
                ucy = (ss * (ex - mx) + ms * (sx - ex) + es * (mx - sx)) / D
                r = math.sqrt((sx - ucx) ** 2 + (sy - ucy) ** 2)
                # Find which cardinal angles the arc sweeps through
                a_s = math.atan2(sy - ucy, sx - ucx)
                a_m = math.atan2(my - ucy, mx - ucx)
                a_e = math.atan2(ey - ucy, ex - ucx)
                # Determine sweep direction (CW or CCW) using mid-point
                nm = (a_m - a_s) % (2.0 * math.pi)
                ne = (a_e - a_s) % (2.0 * math.pi)
                if nm > ne:
                    # Arc goes CW (negative sweep) — swap direction
                    sweep = -((2.0 * math.pi) - ne)
                else:
                    sweep = ne
                # Check each cardinal angle (0, π/2, π, 3π/2)
                for cardinal, dx, dy in [(0, 1, 0), (math.pi / 2, 0, 1),
                                         (math.pi, -1, 0), (3 * math.pi / 2, 0, -1)]:
                    offset = (cardinal - a_s) % (2.0 * math.pi)
                    if sweep > 0 and offset <= sweep:
                        all_x.append(ucx + r * dx)
                        all_y.append(ucy + r * dy)
                    elif sweep < 0 and offset >= (2.0 * math.pi + sweep):
                        all_x.append(ucx + r * dx)
                        all_y.append(ucy + r * dy)
            continue
        # Polygons and curves: use all points
        if e["type"] in ("polygon", "curve") and "points" in e:
            for pt in e["points"]:
                all_x.append(pt[0])
                all_y.append(pt[1])
            continue
        # Lines, rects, arcs without mid: use raw endpoint coordinates
        for key in ["start", "end", "center", "mid"]:
            if key in e and e[key] is not None:
                all_x.append(e[key][0])
                all_y.append(e[key][1])

    bbox = None
    if all_x and all_y:
        bbox = {
            "min_x": min(all_x),
            "min_y": min(all_y),
            "max_x": max(all_x),
            "max_y": max(all_y),
            "width": round(max(all_x) - min(all_x), 3),
            "height": round(max(all_y) - min(all_y), 3),
        }

    return {
        "edge_count": len(edges),
        "edges": edges,
        "bounding_box": bbox,
        # Convenience aliases so consumers don't have to reach into bounding_box.
        # bbox already accounts for arc extrema (see EQ-100 above), so these are
        # correct on arc-edge outlines too; None only when no Edge.Cuts geometry.
        "width_mm": bbox["width"] if bbox else None,
        "height_mm": bbox["height"] if bbox else None,
    }


def analyze_connectivity(footprints: list[dict], tracks: dict, vias: dict,
                         net_names: dict[int, str],
                         zones: list[dict] | None = None) -> dict:
    """Analyze routing completeness — find unrouted nets.

    A net is considered routed if it has tracks, vias, or a copper zone
    covering it. Nets with only a single pad are skipped.
    """
    # Build set of nets that have pads
    pad_nets: dict[int, list[str]] = {}  # net_number -> list of "REF.pad"
    for fp in footprints:
        for pad in fp["pads"]:
            net_num = pad.get("net_number", 0)
            if net_num > 0:
                pad_nets.setdefault(net_num, []).append(f"{fp['reference']}.{pad['number']}")

    # Build set of nets that have routing (tracks, vias, or zones)
    routed_nets = set()
    for seg in tracks.get("segments", []):
        if seg["net"] > 0:
            routed_nets.add(seg["net"])
    for arc in tracks.get("arcs", []):
        if arc["net"] > 0:
            routed_nets.add(arc["net"])
    for via in vias.get("vias", []):
        if via["net"] > 0:
            routed_nets.add(via["net"])
    # Zones also route nets — a GND zone connects all GND pads
    if zones:
        for z in zones:
            zn = z.get("net", 0)
            if zn > 0:
                routed_nets.add(zn)

    # Find unrouted nets (have pads but no tracks/zones)
    unrouted = []
    for net_num, pads in pad_nets.items():
        if len(pads) >= 2 and net_num not in routed_nets:
            net_name = net_names.get(net_num, f"net_{net_num}")
            # Extract component refs from pad strings ("REF.pad" -> "REF")
            comp_refs = sorted(set(p.split(".")[0] for p in pads if "." in p))
            unrouted.append({
                "net_number": net_num,
                "net_name": net_name,
                "pad_count": len(pads),
                "pads": pads,
                "detector": "analyze_connectivity",
                "rule_id": "RT-001",
                "category": "connectivity",
                "severity": "error",
                "confidence": "deterministic",
                "evidence_source": "topology",
                "summary": f"Unrouted net {net_name} ({len(pads)} pads)",
                "description": f"Net {net_name} has {len(pads)} pads but no routing (tracks, vias, or zones).",
                "components": comp_refs,
                "nets": [net_name],
                "pins": [],
                "recommendation": f"Route net {net_name} to connect {len(pads)} pads",
                "report_context": {"section": "Connectivity", "impact": "functionality", "standard_ref": ""},
            })

    return {
        "total_nets_with_pads": len(pad_nets),
        "routed_nets": len(routed_nets & set(pad_nets.keys())),
        "unrouted_count": len(unrouted),
        "routing_complete": len(unrouted) == 0,
        "unrouted": sorted(unrouted, key=lambda u: u["net_name"]),
    }


def group_components(footprints: list[dict]) -> dict:
    """Group components by reference prefix for cross-referencing with schematic."""
    groups: dict[str, list[str]] = {}
    for fp in footprints:
        ref = fp.get("reference", "")
        if not ref:
            continue
        m = re.match(r'^([A-Za-z]+)', ref)
        prefix = m.group(1) if m else ref
        groups.setdefault(prefix, []).append(ref)

    return {prefix: {"count": len(refs), "references": sorted(refs)}
            for prefix, refs in sorted(groups.items())}


def analyze_power_nets(footprints: list[dict], tracks: dict,
                       net_names: dict[int, str]) -> list[dict]:
    """Analyze routing of power/ground nets — track widths, via counts."""
    # EQ-052: d = √(Δx²+Δy²) (Euclidean distance)
    # Identify power/ground nets
    power_nets = {}
    for net_num, name in net_names.items():
        if is_power_net_name(name) or is_ground_name(name):
            power_nets[net_num] = {"name": name, "widths": set(), "track_count": 0,
                                   "total_length_mm": 0.0}

    if not power_nets:
        return []

    for seg in tracks.get("segments", []):
        net = seg["net"]
        if net in power_nets:
            power_nets[net]["widths"].add(seg["width"])
            power_nets[net]["track_count"] += 1
            dx = seg["x2"] - seg["x1"]
            dy = seg["y2"] - seg["y1"]
            power_nets[net]["total_length_mm"] += math.sqrt(dx * dx + dy * dy)

    result = []
    for net_num, info in sorted(power_nets.items(), key=lambda x: x[1]["name"]):
        if info["track_count"] == 0:
            continue  # Only zone-routed or single-pad
        widths = sorted(info["widths"])
        result.append({
            "net": info["name"],
            "track_count": info["track_count"],
            "total_length_mm": round(info["total_length_mm"], 2),
            "min_width_mm": widths[0] if widths else None,
            "max_width_mm": widths[-1] if widths else None,
            "widths_used": widths,
        })
    return result


_ESD_TVS_PREFIXES = ("esd", "prtr", "usblc", "tpd", "pesd", "sp05",
                     "rclamp", "nup", "lesd", "ip4", "dt104")


def _build_routing_graph(segments, arcs, vias_list):
    """Build a per-net adjacency graph from trace segments and vias.

    Nodes are coordinate tuples (x, y) rounded to 0.001mm.
    Edges are trace segments with length and width.

    Returns:
        Dict mapping net_id → {nodes: set, edges: dict[node → [(neighbor, length_mm, width_mm)]]}
    """
    # EQ-045: d = √(Δx²+Δy²) (routing graph edge weight)
    SNAP = 0.001  # Coordinate snapping precision (mm)

    def _snap(x, y):
        return (round(x / SNAP) * SNAP, round(y / SNAP) * SNAP)

    graphs = {}  # net_id → {"edges": defaultdict(list)}

    for seg in segments:
        net = seg.get("net", 0)
        if net <= 0:
            continue
        p1 = _snap(seg["x1"], seg["y1"])
        p2 = _snap(seg["x2"], seg["y2"])
        dx = seg["x2"] - seg["x1"]
        dy = seg["y2"] - seg["y1"]
        length = math.sqrt(dx * dx + dy * dy)
        width = seg.get("width", 0)

        g = graphs.setdefault(net, {})
        edges = g.setdefault("edges", {})
        edges.setdefault(p1, []).append((p2, length, width))
        edges.setdefault(p2, []).append((p1, length, width))

    for arc in arcs:
        net = arc.get("net", 0)
        if net <= 0:
            continue
        s, e = arc["start"], arc["end"]
        p1 = _snap(s[0], s[1])
        p2 = _snap(e[0], e[1])
        m = arc.get("mid")
        if m:
            length = _arc_length_3pt(s[0], s[1], m[0], m[1], e[0], e[1])
        else:
            dx, dy = e[0] - s[0], e[1] - s[1]
            length = math.sqrt(dx * dx + dy * dy)
        width = arc.get("width", 0)

        g = graphs.setdefault(net, {})
        edges = g.setdefault("edges", {})
        edges.setdefault(p1, []).append((p2, length, width))
        edges.setdefault(p2, []).append((p1, length, width))

    # Add vias as zero-length edges connecting the same point across layers
    for via in vias_list:
        net = via.get("net", 0)
        if net <= 0:
            continue
        vp = _snap(via["x"], via["y"])
        g = graphs.setdefault(net, {})
        edges = g.setdefault("edges", {})
        edges.setdefault(vp, [])  # Ensure via point exists as a node

    return graphs


def _route_distance(graph, start_xy, end_xy, snap=0.001):
    """Find the shortest routed distance between two points in a net graph.

    Uses Dijkstra's algorithm on the routing graph.

    Args:
        graph: {"edges": {node → [(neighbor, length, width)]}}
        start_xy: (x, y) tuple of start pad position
        end_xy: (x, y) tuple of end pad position
        snap: Coordinate snapping precision

    Returns:
        (total_length_mm, path_widths) or (None, None) if no path exists
    """
    def _snap(x, y):
        return (round(x / snap) * snap, round(y / snap) * snap)

    start = _snap(*start_xy)
    end = _snap(*end_xy)
    edges = graph.get("edges", {})

    if start not in edges or end not in edges:
        return None, None
    if start == end:
        return 0.0, []

    # Dijkstra
    dist = {start: 0.0}
    prev = {}
    widths = {}
    heap = [(0.0, start)]
    visited = set()

    while heap:
        d, node = heapq.heappop(heap)
        if node in visited:
            continue
        visited.add(node)
        if node == end:
            # Reconstruct path widths
            path_widths = []
            n = end
            while n in prev:
                path_widths.append(widths[n])
                n = prev[n]
            return round(d, 3), list(reversed(path_widths))
        for neighbor, length, width in edges.get(node, []):
            if neighbor in visited:
                continue
            new_dist = d + length
            if neighbor not in dist or new_dist < dist[neighbor]:
                dist[neighbor] = new_dist
                prev[neighbor] = node
                widths[neighbor] = width
                heapq.heappush(heap, (new_dist, neighbor))

    return None, None  # No path found


def analyze_pad_to_pad_distances(footprints, tracks, vias, net_names):
    """Compute actual routed trace distances between component pads on shared nets.

    Builds a routing graph per net and uses Dijkstra to find the shortest
    routed path between each pair of pads. Much more accurate than Euclidean
    distance for decoupling placement and parasitic extraction.

    Returns:
        Dict mapping "REF1.pad-REF2.pad" → {
            "net": net_name,
            "routed_distance_mm": float,
            "euclidean_distance_mm": float,
            "ratio": float (routed/euclidean — 1.0 = direct, >1.5 = detour),
            "min_width_mm": float
        }
    """
    # EQ-051: d = √(Δx²+Δy²) (pad-to-pad distance)
    # Build routing graphs
    graphs = _build_routing_graph(
        tracks.get("segments", []),
        tracks.get("arcs", []),
        vias.get("vias", [])
    )

    # Collect pad positions per net
    pad_positions = {}  # net_id → [(ref, pad_num, x, y)]
    for fp in footprints:
        ref = fp.get("reference", "")
        for pad in fp.get("pads", []):
            net = pad.get("net_number", 0)
            if net <= 0:
                continue
            x = pad.get("abs_x", fp.get("x", 0))
            y = pad.get("abs_y", fp.get("y", 0))
            pad_positions.setdefault(net, []).append((ref, pad["number"], x, y))

    results = {}
    for net_id, pads in pad_positions.items():
        if len(pads) < 2:
            continue
        graph = graphs.get(net_id)
        if not graph:
            continue
        net_name = net_names.get(net_id, f"net_{net_id}")

        # Compute distances between all pairs (limited to 20 pads per net
        # to avoid combinatorial explosion on power nets)
        if len(pads) > 20:
            continue  # Skip high-fanout nets

        for i in range(len(pads)):
            for j in range(i + 1, len(pads)):
                ref_a, pad_a, xa, ya = pads[i]
                ref_b, pad_b, xb, yb = pads[j]

                # Euclidean distance
                euclid = math.sqrt((xb - xa) ** 2 + (yb - ya) ** 2)
                if euclid < 0.1:
                    continue  # Same pad or overlapping

                # Routed distance
                routed, widths = _route_distance(graph, (xa, ya), (xb, yb))
                if routed is None:
                    continue

                key = f"{ref_a}.{pad_a}-{ref_b}.{pad_b}"
                entry = {
                    "net": net_name,
                    "routed_distance_mm": routed,
                    "euclidean_distance_mm": round(euclid, 3),
                    "ratio": round(routed / euclid, 2) if euclid > 0 else 0,
                }
                if widths:
                    entry["min_width_mm"] = min(widths)
                results[key] = entry

    return results


def analyze_return_path_continuity(tracks, net_names, zones, zone_fills,
                                    signal_nets=None, ref_layer_map=None,
                                    footprints=None, radius_mm=0.5,
                                    debug_samples=None):
    """Check ground/power plane continuity under signal traces.

    For each signal net's trace segments, samples points along the trace
    and checks if the opposite layer has a ground or power zone fill.
    Flags gaps in the reference plane that could cause return path
    discontinuities and EMI issues.

    Uses :class:`CopperPresence` for radius-based copper detection that
    credits zone fills, tracks, and pads — avoids false negatives from
    KiCad zone-fill clearance channels ("swiss cheese" polygons).

    Args:
        tracks: Track data dict with segments
        net_names: Net number → name mapping
        zones: Zone list (for zone metadata)
        zone_fills: ZoneFills spatial index
        signal_nets: Optional set of net names to check (default: all non-power)
        ref_layer_map: Layer → opposite reference layer mapping
        footprints: Footprint list (for pad copper credit)
        radius_mm: Radius (mm) for copper-presence search (default 0.5)
        debug_samples: If a list is passed, per-sample dicts are appended
            with keys {net, x, y, layer, hit} for GP-001 diagnostics.

    Returns:
        List of gap findings: [{net, layer, gap_start_mm, gap_length_mm, ...}]
    """
    # EQ-053: d = √(Δx²+Δy²) (trace-to-plane gap detection)
    if not zone_fills.has_data:
        return []

    cp = CopperPresence(zone_fills, tracks.get('segments', []), footprints)

    from kicad_utils import is_power_net_name, is_ground_name

    findings = []
    # Only check signal nets (not power/ground — they ARE the reference)
    segments = tracks.get("segments", [])

    # Group segments by net
    net_segments: dict[int, list] = {}
    for seg in segments:
        net = seg.get("net", 0)
        if net <= 0:
            continue
        net_name = net_names.get(net, "")
        if is_power_net_name(net_name) or is_ground_name(net_name):
            continue
        if signal_nets and net_name not in signal_nets:
            continue
        net_segments.setdefault(net, []).append(seg)

    SAMPLE_INTERVAL = 2.0  # mm between sample points

    for net_id, segs in net_segments.items():
        net_name = net_names.get(net_id, f"net_{net_id}")
        total_samples = 0
        gap_samples = 0

        for seg in segs:
            layer = seg.get("layer", "F.Cu")
            if ref_layer_map:
                opp_layer = ref_layer_map.get(layer, "B.Cu" if layer == "F.Cu" else "F.Cu")
            else:
                opp_layer = "B.Cu" if layer == "F.Cu" else "F.Cu"

            x1, y1 = seg["x1"], seg["y1"]
            x2, y2 = seg["x2"], seg["y2"]
            dx, dy = x2 - x1, y2 - y1
            length = math.sqrt(dx * dx + dy * dy)
            if length < 0.1:
                continue

            # Sample along the trace
            n_samples = max(2, int(length / SAMPLE_INTERVAL) + 1)
            for k in range(n_samples):
                t = k / max(n_samples - 1, 1)
                px = x1 + t * dx
                py = y1 + t * dy
                total_samples += 1

                # Check for ANY copper (zone, track, pad) on opposite layer
                hit = cp.has_coverage_near(px, py, opp_layer,
                                           radius_mm=radius_mm)
                if not hit:
                    gap_samples += 1
                if debug_samples is not None:
                    debug_samples.append({
                        'net': net_name, 'x': round(px, 2),
                        'y': round(py, 2), 'layer': opp_layer,
                        'hit': hit,
                    })

        if total_samples > 0 and gap_samples > 0:
            coverage_pct = round((1 - gap_samples / total_samples) * 100, 1)
            if coverage_pct < 95:  # Only report if significant gap
                total_length = sum(
                    math.sqrt((s["x2"]-s["x1"])**2 + (s["y2"]-s["y1"])**2)
                    for s in segs)
                findings.append({
                    "net": net_name,
                    "total_trace_mm": round(total_length, 1),
                    "samples_checked": total_samples,
                    "samples_with_reference_plane": total_samples - gap_samples,
                    "reference_plane_coverage_pct": coverage_pct,
                    "gap_note": f"{gap_samples} of {total_samples} sample points lack reference plane on opposite layer",
                })

    # Sort by coverage (worst first)
    findings.sort(key=lambda f: f["reference_plane_coverage_pct"])
    return findings


def _min_power_pad_distance(ic_fp: dict, cap_fp: dict) -> float:
    """Minimum distance between IC power/ground pads and capacitor pads.

    Uses absolute pad coordinates for accurate distance on large packages
    where footprint center can be 3+ mm from the actual power pin.
    Falls back to footprint center distance if pad data is missing.
    """
    # EQ-101: d = √((x1-x2)² + (y1-y2)²) over all pad pairs; return minimum.
    # Source: Self-evident — 2D Euclidean distance.
    ic_pads = ic_fp.get("pads", [])
    cap_pads = cap_fp.get("pads", [])

    # Find IC pads on power or ground nets
    power_pads = []
    for pad in ic_pads:
        net = pad.get("net_name", "")
        if not net:
            continue
        nu = net.upper()
        is_pwr_gnd = (
            nu in ("GND", "VSS", "AGND", "DGND", "PGND", "VCC", "VDD",
                   "AVCC", "AVDD", "DVCC", "DVDD") or
            nu.startswith(("GND", "VSS", "VCC", "VDD", "+")) or
            nu.endswith(("GND", "VSS")) or
            "V" in nu and any(c.isdigit() for c in nu)
        )
        if is_pwr_gnd:
            power_pads.append(pad)

    if not power_pads or not cap_pads:
        # Fallback: footprint center distance
        dx = ic_fp["x"] - cap_fp["x"]
        dy = ic_fp["y"] - cap_fp["y"]
        return math.sqrt(dx * dx + dy * dy)

    # Minimum distance between any IC power pad and any cap pad
    min_dist = float("inf")
    for ip in power_pads:
        ix, iy = ip.get("abs_x"), ip.get("abs_y")
        if ix is None or iy is None:
            continue
        for cp in cap_pads:
            cx, cy = cp.get("abs_x"), cp.get("abs_y")
            if cx is None or cy is None:
                continue
            d = math.sqrt((ix - cx) ** 2 + (iy - cy) ** 2)
            if d < min_dist:
                min_dist = d
    return min_dist


def analyze_decoupling_placement(footprints: list[dict]) -> list[dict]:
    """For each IC, find nearby capacitors and report distances.

    Helps verify decoupling caps are placed close to IC power pins.
    """
    # EQ-048: d = √(Δx²+Δy²) (cap-to-IC distance)
    ics = [fp for fp in footprints
           if re.match(r'^(U|IC)\d', fp.get("reference", ""))
           and not any(fp.get("value", "").lower().startswith(p)
                       for p in _ESD_TVS_PREFIXES)]
    caps = [fp for fp in footprints if re.match(r'^C\d', fp.get("reference", ""))]

    if not ics or not caps:
        return []

    results = []
    for ic in ics:
        nearby = []
        for cap in caps:
            dist = _min_power_pad_distance(ic, cap)
            if dist <= 10.0:  # Within 10mm
                # Check if cap shares a net with IC (likely decoupling)
                ic_nets = {p.get("net_name") for p in ic.get("pads", []) if p.get("net_name")}
                cap_nets = {p.get("net_name") for p in cap.get("pads", []) if p.get("net_name")}
                shared = (ic_nets & cap_nets) - {""}
                nearby.append({
                    "cap": cap["reference"],
                    "value": cap.get("value", ""),
                    "distance_mm": round(dist, 2),
                    "shared_nets": sorted(shared) if shared else [],
                    "same_side": cap["layer"] == ic["layer"],
                })
        if nearby:
            nearby.sort(key=lambda n: n["distance_mm"])
            results.append({
                "ic": ic["reference"],
                "value": ic.get("value", ""),
                "layer": ic["layer"],
                "nearby_caps": nearby,
                "closest_cap_mm": nearby[0]["distance_mm"],
            })

    # ESD protection ICs need bypass caps within 3mm for clamping
    esd_ics = [fp for fp in footprints
               if re.match(r'^(U|IC)\d', fp.get("reference", ""))
               and any(fp.get("value", "").lower().startswith(p)
                       for p in _ESD_TVS_PREFIXES)]
    for ic in esd_ics:
        nearby = []
        for cap in caps:
            dist = _min_power_pad_distance(ic, cap)
            if dist <= 10.0:
                ic_nets = {p.get("net_name") for p in ic.get("pads", [])
                           if p.get("net_name")}
                cap_nets = {p.get("net_name") for p in cap.get("pads", [])
                            if p.get("net_name")}
                shared = (ic_nets & cap_nets) - {""}
                nearby.append({
                    "cap": cap["reference"],
                    "value": cap.get("value", ""),
                    "distance_mm": round(dist, 2),
                    "shared_nets": sorted(shared) if shared else [],
                    "same_side": cap["layer"] == ic["layer"],
                })
        if nearby:
            nearby.sort(key=lambda n: n["distance_mm"])
            results.append({
                "ic": ic["reference"],
                "value": ic.get("value", ""),
                "layer": ic["layer"],
                "category": "esd_bypass",
                "nearby_caps": nearby,
                "closest_cap_mm": nearby[0]["distance_mm"],
            })

    return results


def _safe_num(val, default=0):
    """Safely convert a value to float (handles None, str, etc.)."""
    if val is None:
        return default
    try:
        return float(val)
    except (ValueError, TypeError):
        return default


def _build_reference_layer_map(stackup: list[dict]) -> dict[str, str]:
    """Map each copper layer to its adjacent reference plane copper layer.

    Walks the stackup in order and for each copper layer, finds the nearest
    other copper layer (above or below, preferring the one separated by
    thinner dielectric). Returns a mapping like {"F.Cu": "In1.Cu", "In1.Cu": "F.Cu", ...}.

    Falls back to simple F.Cu<->B.Cu when no stackup is available.
    """
    if not stackup:
        return {"F.Cu": "B.Cu", "B.Cu": "F.Cu"}

    # Extract ordered copper layer names and their stackup indices
    copper_layers: list[tuple[int, str]] = []
    for i, layer in enumerate(stackup):
        if layer.get("type") == "copper":
            copper_layers.append((i, layer.get("name", "")))

    if len(copper_layers) < 2:
        return {"F.Cu": "B.Cu", "B.Cu": "F.Cu"}

    ref_map: dict[str, str] = {}
    for ci, (idx, name) in enumerate(copper_layers):
        # Find dielectric thickness to adjacent copper layers above and below
        best_neighbor = None
        best_thickness = float("inf")

        for direction, neighbor_ci in [(-1, ci - 1), (1, ci + 1)]:
            if neighbor_ci < 0 or neighbor_ci >= len(copper_layers):
                continue
            n_idx, n_name = copper_layers[neighbor_ci]
            # Sum dielectric thickness between this layer and the neighbor
            lo = min(idx, n_idx)
            hi = max(idx, n_idx)
            thickness = 0.0
            for k in range(lo + 1, hi):
                if stackup[k].get("type") in ("core", "prepreg"):
                    t = stackup[k].get("thickness")
                    if t is not None:
                        try:
                            thickness += float(t)
                        except (ValueError, TypeError):
                            thickness += 0.2
            if thickness < best_thickness:
                best_thickness = thickness
                best_neighbor = n_name

        if best_neighbor:
            ref_map[name] = best_neighbor

    return ref_map


def _microstrip_impedance(width_mm, height_mm, thickness_mm, epsilon_r):
    """Calculate single-ended microstrip characteristic impedance.

    Uses Wheeler's equations (IPC-2141) with effective width correction
    for finite copper thickness.

    Args:
        width_mm: Trace width in mm
        height_mm: Dielectric height to reference plane in mm
        thickness_mm: Copper thickness in mm
        epsilon_r: Relative permittivity of dielectric

    Returns:
        Characteristic impedance in ohms, or None if inputs invalid
    """
    width_mm = _safe_num(width_mm)
    height_mm = _safe_num(height_mm)
    thickness_mm = _safe_num(thickness_mm)
    epsilon_r = _safe_num(epsilon_r)
    if width_mm <= 0 or height_mm <= 0 or thickness_mm <= 0 or epsilon_r <= 0:
        return None
    w = width_mm
    h = height_mm
    t = thickness_mm
    er = epsilon_r
    # Effective width accounting for copper thickness (IPC-2141)
    if w > 2 * math.pi * t:
        w_eff = w + (t / math.pi) * (1 + math.log(2 * h / t))
    else:
        w_eff = w + (t / math.pi) * (1 + math.log(4 * math.pi * w / t))
    # Wheeler's equations
    # Source: IPC-2141 Design Guide
    # Verified: https://f4inx.github.io/posts/microstrip-formulas-comparison.html
    if w_eff / h < 1:
        # EQ-023: Z₀ = (60/√εr)ln(8h/w+w/4h) (Wheeler narrow microstrip)
        z0 = (60 / math.sqrt(er)) * math.log(8 * h / w_eff + w_eff / (4 * h))
    else:
        # EQ-024: Z₀ = 120π/(√εr(w/h+1.393+0.667ln(w/h+1.444))) (Wheeler wide)
        z0 = (120 * math.pi) / (math.sqrt(er) * (w_eff / h + 1.393 + 0.667 * math.log(w_eff / h + 1.444)))
    return z0


def _build_layer_heights(stackup):
    """Map copper layer names to their dielectric height above the nearest reference plane.

    Walks the stackup from top to bottom. Each copper layer's height is the
    thickness of the adjacent dielectric layer below it (for top layers) or
    above it (for bottom layers).

    Returns:
        Dict mapping layer name → (dielectric_height_mm, epsilon_r, copper_thickness_mm)
    """
    if not stackup:
        return {}

    heights = {}
    layers = list(stackup)

    for i, layer in enumerate(layers):
        if layer.get("type") != "copper":
            continue
        name = layer.get("name", "")
        cu_t = layer.get("thickness", 0.035)

        # Look for the nearest dielectric layer (below for top copper, above for bottom)
        # Try below first
        for j in range(i + 1, len(layers)):
            if layers[j].get("type") in ("core", "prepreg"):
                h = layers[j].get("thickness", 0.2)
                er = layers[j].get("epsilon_r", 4.5)
                heights[name] = (h, er, cu_t)
                break
        else:
            # No dielectric below — try above
            for j in range(i - 1, -1, -1):
                if layers[j].get("type") in ("core", "prepreg"):
                    h = layers[j].get("thickness", 0.2)
                    er = layers[j].get("epsilon_r", 4.5)
                    heights[name] = (h, er, cu_t)
                    break

    return heights


def analyze_net_lengths(tracks: dict, vias: dict,
                        net_names: dict[int, str],
                        include_segments: bool = False,
                        stackup: list = None) -> list[dict]:
    """Per-net trace length measurement for matched-length and routing analysis.

    Provides total length, per-layer breakdown, segment count, and via count
    for each routed net. Enables differential pair matching, bus length matching,
    and routing completeness assessment by higher-level logic.

    When include_segments=True, also emits per-segment width+length detail and
    per-via drill size, for parasitic extraction by the SPICE simulation skill.

    When stackup is provided, each trace segment also gets a characteristic
    impedance estimate (microstrip formula from IPC-2141).
    """
    # EQ-050: L = √(Δx²+Δy²) (track segment length)
    # Pre-compute layer-to-dielectric-height mapping for impedance calculation
    layer_heights = _build_layer_heights(stackup) if stackup else {}

    net_data: dict[int, dict] = {}

    for seg in tracks.get("segments", []):
        net = seg["net"]
        if net <= 0:
            continue
        dx = seg["x2"] - seg["x1"]
        dy = seg["y2"] - seg["y1"]
        length = math.sqrt(dx * dx + dy * dy)

        d = net_data.setdefault(net, {"layers": {}, "total_length": 0.0,
                                      "segment_count": 0, "via_count": 0})
        d["total_length"] += length
        d["segment_count"] += 1
        layer = seg["layer"]
        ld = d["layers"].setdefault(layer, {"length": 0.0, "segments": 0})
        ld["length"] += length
        ld["segments"] += 1

        if include_segments:
            seg_entry = {
                "layer": layer,
                "length_mm": round(length, 3),
                "width_mm": seg.get("width", 0),
            }
            # Add impedance if stackup is available
            if stackup and layer_heights and layer in layer_heights:
                h, er, cu_t = layer_heights[layer]
                z0 = _microstrip_impedance(seg.get("width", 0), h, cu_t, er)
                if z0:
                    seg_entry["impedance_ohm"] = round(z0, 1)
            d.setdefault("trace_segments", []).append(seg_entry)

    for arc in tracks.get("arcs", []):
        net = arc["net"]
        if net <= 0:
            continue
        s, e = arc["start"], arc["end"]
        m = arc.get("mid")
        if m:
            length = _arc_length_3pt(s[0], s[1], m[0], m[1], e[0], e[1])
        else:
            dx, dy = e[0] - s[0], e[1] - s[1]
            length = math.sqrt(dx * dx + dy * dy)

        d = net_data.setdefault(net, {"layers": {}, "total_length": 0.0,
                                      "segment_count": 0, "via_count": 0})
        d["total_length"] += length
        d["segment_count"] += 1
        layer = arc["layer"]
        ld = d["layers"].setdefault(layer, {"length": 0.0, "segments": 0})
        ld["length"] += length
        ld["segments"] += 1

        if include_segments:
            seg_entry = {
                "layer": layer,
                "length_mm": round(length, 3),
                "width_mm": arc.get("width", 0),
            }
            if stackup and layer_heights and layer in layer_heights:
                h, er, cu_t = layer_heights[layer]
                z0 = _microstrip_impedance(arc.get("width", 0), h, cu_t, er)
                if z0:
                    seg_entry["impedance_ohm"] = round(z0, 1)
            d.setdefault("trace_segments", []).append(seg_entry)

    for via in vias.get("vias", []):
        net = via["net"]
        if net <= 0:
            continue
        d = net_data.setdefault(net, {"layers": {}, "total_length": 0.0,
                                      "segment_count": 0, "via_count": 0})
        d["via_count"] += 1

        if include_segments:
            via_entry = {
                "drill_mm": via.get("drill", 0),
                "layers": via.get("layers", []),
            }
            # Compute stub length for through-hole vias on boards with >2 layers
            if stackup and layer_heights:
                via_layers = via.get("layers", [])
                if len(via_layers) >= 2 and len(layer_heights) > 2:
                    # Via connects between first and last of its layers;
                    # stub = total board thickness - span between connected layers
                    all_cu = [l["name"] for l in stackup if l.get("type") == "copper"]
                    if len(all_cu) > 2:
                        try:
                            top_idx = all_cu.index(via_layers[0])
                            bot_idx = all_cu.index(via_layers[-1])
                            # Stub = layers below the bottom connected layer
                            stub_layers = all_cu[bot_idx + 1:]
                            if stub_layers:
                                stub_mm = sum(layer_heights.get(l, (0.2, 4.5, 0.035))[0]
                                              for l in stub_layers)
                                via_entry["stub_length_mm"] = round(stub_mm, 3)
                        except ValueError:
                            pass
            d.setdefault("via_details", []).append(via_entry)

    result = []
    for net_num, data in sorted(net_data.items(),
                                key=lambda x: x[1]["total_length"], reverse=True):
        entry = {
            "net": net_names.get(net_num, f"net_{net_num}"),
            "net_number": net_num,
            "total_length_mm": round(data["total_length"], 3),
            "segment_count": data["segment_count"],
            "via_count": data["via_count"],
            "layers": {
                layer: {"length_mm": round(info["length"], 3),
                        "segments": info["segments"]}
                for layer, info in sorted(data["layers"].items())
            },
        }
        if include_segments:
            if "trace_segments" in data:
                entry["trace_segments"] = data["trace_segments"]
            if "via_details" in data:
                entry["via_details"] = data["via_details"]
        result.append(entry)
    return result


def analyze_ground_domains(footprints: list[dict], net_names: dict[int, str],
                           zones: list[dict]) -> dict:
    """Identify ground domain splits and component membership.

    Detects separate ground nets (GND, AGND, DGND, PGND, etc.) and reports
    which components connect to each. Components on multiple ground domains
    are flagged — these may be intentional (star ground) or errors.
    """
    ground_nets: dict[int, str] = {}
    for net_num, name in net_names.items():
        nu = name.upper()
        if any(g in nu for g in ("GND", "VSS", "GROUND")):
            ground_nets[net_num] = name

    if not ground_nets:
        return {"domain_count": 0, "domains": [], "multi_domain_components": []}

    domain_components: dict[int, set[str]] = {n: set() for n in ground_nets}
    component_domains: dict[str, set[int]] = {}

    for fp in footprints:
        ref = fp.get("reference", "")
        for pad in fp.get("pads", []):
            net_num = pad.get("net_number", 0)
            if net_num in ground_nets:
                domain_components[net_num].add(ref)
                component_domains.setdefault(ref, set()).add(net_num)

    ground_zones: dict[int, list[str]] = {}
    for z in zones:
        zn = z.get("net", 0)
        if zn in ground_nets:
            ground_zones.setdefault(zn, []).extend(z.get("layers", []))

    domains = []
    for net_num, name in sorted(ground_nets.items(), key=lambda x: x[1]):
        comps = sorted(domain_components.get(net_num, set()))
        domains.append({
            "net": name,
            "net_number": net_num,
            "component_count": len(comps),
            "components": comps,
            "has_zone": net_num in ground_zones,
            "zone_layers": sorted(set(ground_zones.get(net_num, []))),
        })

    multi = []
    for ref, nets in sorted(component_domains.items()):
        if len(nets) > 1:
            multi.append({
                "component": ref,
                "ground_nets": sorted(ground_nets[n] for n in nets),
            })

    return {
        "domain_count": len(domains),
        "domains": domains,
        "multi_domain_components": multi,
    }


def analyze_trace_proximity(tracks: dict, net_names: dict[int, str],
                            grid_size: float = 0.5) -> dict:
    """Identify signal nets with traces running close together on the same layer.

    Uses a spatial grid to find net pairs sharing grid cells, indicating
    physical proximity on the PCB. Power/ground nets are excluded since
    they are expected to be everywhere. Only pairs with significant coupling
    (≥2 shared cells) are reported.

    Returns proximity pairs sorted by approximate coupling length, plus the
    grid resolution used. Higher-level logic can use this to assess crosstalk
    risk, guard trace needs, or impedance concerns.
    """
    # EQ-057: d = √(Δx²+Δy²) (grid-based proximity scan)
    grid: dict[tuple[str, int, int], set[int]] = {}

    def _mark(x1: float, y1: float, x2: float, y2: float,
              layer: str, net: int) -> None:
        # EQ-046: d = √(Δx²+Δy²) (grid cell marking)
        if net <= 0:
            return
        dx, dy = x2 - x1, y2 - y1
        length = math.sqrt(dx * dx + dy * dy)
        if length < 0.001:
            return
        steps = max(1, int(length / (grid_size * 0.5)))
        inv = 1.0 / steps
        for i in range(steps + 1):
            t = i * inv
            gx = int((x1 + t * dx) / grid_size)
            gy = int((y1 + t * dy) / grid_size)
            grid.setdefault((layer, gx, gy), set()).add(net)

    for seg in tracks.get("segments", []):
        _mark(seg["x1"], seg["y1"], seg["x2"], seg["y2"],
              seg["layer"], seg["net"])
    for arc in tracks.get("arcs", []):
        s, e = arc["start"], arc["end"]
        _mark(s[0], s[1], e[0], e[1], arc["layer"], arc["net"])

    # Count shared cells per net pair (signal nets only)
    pair_counts: dict[tuple[str, int, int], int] = {}
    for (_layer, _gx, _gy), nets in grid.items():
        signal = sorted(n for n in nets
                        if not (is_power_net_name(net_names.get(n, "")) or is_ground_name(net_names.get(n, ""))))
        if len(signal) < 2:
            continue
        for i in range(len(signal)):
            for j in range(i + 1, len(signal)):
                pk = (_layer, signal[i], signal[j])
                pair_counts[pk] = pair_counts.get(pk, 0) + 1

    pairs = []
    for (layer, na, nb), count in pair_counts.items():
        if count < 2:
            continue
        pairs.append({
            "net_a": net_names.get(na, f"net_{na}"),
            "net_b": net_names.get(nb, f"net_{nb}"),
            "layer": layer,
            "shared_cells": count,
            "approx_coupling_mm": round(count * grid_size, 1),
        })

    pairs.sort(key=lambda p: p["approx_coupling_mm"], reverse=True)

    return {
        "grid_size_mm": grid_size,
        "proximity_pairs": pairs[:100],
        "total_pairs_found": len(pairs),
    }


def analyze_current_capacity(tracks: dict, vias: dict, zones: list[dict],
                             net_names: dict[int, str],
                             setup: dict) -> dict:
    """Provide facts for current capacity assessment (IPC-2221).

    For each net, reports the minimum track width and total copper cross-section
    data that higher-level logic needs to calculate current capacity using
    IPC-2221 formulas. Also reports via drill sizes per net (vias have lower
    current capacity than tracks of the same width).

    Focuses on power/ground nets where current capacity matters most, but
    also flags any signal net with unusually thin traces for its track count
    (potential bottleneck).
    """
    # Per-net track width data
    net_widths: dict[int, dict] = {}

    for seg in tracks.get("segments", []):
        net = seg["net"]
        if net <= 0:
            continue
        w = seg["width"]
        layer = seg["layer"]
        d = net_widths.setdefault(net, {
            "min_width": float("inf"), "max_width": 0.0,
            "widths": set(), "layers": set(), "segment_count": 0,
            "via_count": 0, "via_drills": set(),
        })
        d["min_width"] = min(d["min_width"], w)
        d["max_width"] = max(d["max_width"], w)
        d["widths"].add(w)
        d["layers"].add(layer)
        d["segment_count"] += 1

    for arc in tracks.get("arcs", []):
        net = arc["net"]
        if net <= 0:
            continue
        w = arc["width"]
        d = net_widths.setdefault(net, {
            "min_width": float("inf"), "max_width": 0.0,
            "widths": set(), "layers": set(), "segment_count": 0,
            "via_count": 0, "via_drills": set(),
        })
        d["min_width"] = min(d["min_width"], w)
        d["max_width"] = max(d["max_width"], w)
        d["widths"].add(w)
        d["layers"].add(arc["layer"])
        d["segment_count"] += 1

    for via in vias.get("vias", []):
        net = via["net"]
        if net <= 0:
            continue
        d = net_widths.setdefault(net, {
            "min_width": float("inf"), "max_width": 0.0,
            "widths": set(), "layers": set(), "segment_count": 0,
            "via_count": 0, "via_drills": set(),
        })
        d["via_count"] += 1
        if via.get("drill"):
            d["via_drills"].add(via["drill"])

    # Zone coverage per net
    net_zones: dict[int, list[dict]] = {}
    for z in zones:
        zn = z.get("net", 0)
        if zn > 0:
            net_zones.setdefault(zn, []).append({
                "layers": z.get("layers", []),
                "filled_area_mm2": z.get("filled_area_mm2"),
                "min_thickness": z.get("min_thickness"),
            })

    # Board thickness for internal layer calculation
    board_thickness = setup.get("board_thickness_mm", 1.6)

    # Build output — power/ground nets first, then any signal nets with
    # narrow traces (potential current bottlenecks)
    power_entries = []
    signal_narrow = []

    for net_num, data in net_widths.items():
        if data["min_width"] == float("inf"):
            continue
        name = net_names.get(net_num, f"net_{net_num}")
        is_power = is_power_net_name(name) or is_ground_name(name)

        entry = {
            "net": name,
            "net_number": net_num,
            "min_track_width_mm": data["min_width"],
            "max_track_width_mm": data["max_width"],
            "track_widths_used": sorted(data["widths"]),
            "copper_layers": sorted(data["layers"]),
            "segment_count": data["segment_count"],
            "via_count": data["via_count"],
        }
        if data["via_drills"]:
            entry["via_drill_sizes_mm"] = sorted(data["via_drills"])

        if net_num in net_zones:
            entry["zones"] = net_zones[net_num]

        if is_power:
            entry["detector"] = "analyze_current_capacity"
            entry["rule_id"] = "CC-DET"
            entry["category"] = "current_capacity"
            entry["severity"] = "info"
            entry["confidence"] = "deterministic"
            entry["evidence_source"] = "topology"
            entry["summary"] = f"Power net {name}: {data['min_width']}mm min trace"
            entry["description"] = (
                f"Power/ground net {name}: min trace {data['min_width']}mm, "
                f"max {data['max_width']}mm, {data['segment_count']} segments."
            )
            entry["components"] = []
            entry["nets"] = [name]
            entry["pins"] = []
            entry["recommendation"] = ""
            entry["report_context"] = {
                "section": "Current Capacity",
                "impact": "Power delivery",
                "standard_ref": "IPC-2221",
            }
            power_entries.append(entry)
        elif data["min_width"] <= 0.15 and data["segment_count"] >= 5:
            # Signal nets with ≤0.15mm traces and significant routing
            entry["detector"] = "analyze_current_capacity"
            entry["rule_id"] = "CC-002"
            entry["category"] = "current_capacity"
            entry["severity"] = "warning"
            entry["confidence"] = "deterministic"
            entry["evidence_source"] = "topology"
            entry["summary"] = f"Narrow signal: {name} min {data['min_width']}mm"
            entry["description"] = (
                f"Signal net {name} has narrow traces: min {data['min_width']}mm "
                f"across {data['segment_count']} segments."
            )
            entry["components"] = []
            entry["nets"] = [name]
            entry["pins"] = []
            entry["recommendation"] = "Widen trace or verify signal integrity requirements."
            entry["report_context"] = {
                "section": "Current Capacity",
                "impact": "Signal integrity",
                "standard_ref": "",
            }
            signal_narrow.append(entry)

    power_entries.sort(key=lambda e: e["net"])
    signal_narrow.sort(key=lambda e: e["min_track_width_mm"])

    return {
        "board_thickness_mm": board_thickness,
        "power_ground_nets": power_entries,
        "narrow_signal_nets": signal_narrow[:20],
    }


def _find_thermal_pads(fp: dict) -> list[dict]:
    """Identify thermal/exposed pads on a footprint.

    Returns list of pad dicts that are likely thermal pads —
    large center pads on power/ground nets, typical of QFN/BGA packages.
    """
    pads = fp.get("pads", [])
    if len(pads) < 3:
        return []

    # Calculate SMD pad area statistics (skip paste-only pads)
    pad_areas: list[tuple[dict, float]] = []
    for p in pads:
        if p.get("type") != "smd":
            continue
        pad_layers = p.get("layers", [])
        if not any(l.endswith(".Cu") or l == "*.Cu" for l in pad_layers):
            continue
        w = p.get("width", p.get("size_x", 0))
        h = p.get("height", p.get("size_y", 0))
        area = w * h
        if area > 0:
            pad_areas.append((p, area))

    if not pad_areas:
        return []

    avg_area = sum(a for _, a in pad_areas) / len(pad_areas)
    all_areas_sorted = sorted(a for _, a in pad_areas)
    median_area = all_areas_sorted[len(all_areas_sorted) // 2]

    thermal = []
    for p, area in pad_areas:
        pad_num = str(p.get("number", ""))
        is_ep = pad_num in ("0", "EP", "")

        # DFN/QFN variants use highest-numbered pad as EP — detect by
        # area ratio (pad >= 3x the median signal pad area)
        if not is_ep and median_area > 0:
            other_areas = sorted(a for pad, a in pad_areas
                                 if str(pad.get("number", "")) != pad_num)
            if other_areas:
                median_signal = other_areas[len(other_areas) // 2]
                if median_signal > 0 and area >= median_signal * 3.0:
                    is_ep = True

        # Thermal pad: explicitly named EP/0 with area >= 2mm²,
        # or any pad with area > 6mm² (large enough to need thermal vias)
        if not ((is_ep and area >= 2.0) or area > 6.0):
            continue

        # Must be at least 2x the average pad area
        if avg_area > 0 and area < avg_area * 2.0:
            continue

        # Must have a net — structural/shield pads with no net are not thermal
        net_name = p.get("net_name", "")
        pad_net_num = p.get("net_number", -1)
        if not net_name or pad_net_num <= 0:
            continue

        # Must be on a ground or power net (thermal pads dissipate heat)
        net_upper = net_name.upper()
        is_power_or_gnd = (
            net_upper in ("GND", "VSS", "AGND", "DGND", "PGND", "VCC", "VDD",
                          "AVCC", "AVDD", "DVCC", "DVDD", "VBUS")
            or net_upper.startswith("+")
            or net_upper.startswith("V+")
            or "GND" in net_upper
            or "VCC" in net_upper
            or "VDD" in net_upper
        )
        if not is_power_or_gnd and not is_ep:
            continue

        thermal.append(p)

    return thermal


def analyze_thermal_vias(footprints: list[dict], vias: dict,
                         zones: list[dict]) -> dict:
    """Provide facts for thermal analysis — via stitching, thermal pads, via-in-pad.

    Reports:
    - Via density per zone (stitching vias for thermal/ground plane connectivity)
    - Exposed/thermal pad detection on QFN/BGA packages (pad connected to ground)
    - Via clusters near thermal pads (thermal via arrays)
    - Overall via distribution across layers
    """
    # EQ-055: density = count / area_cm² (thermal via density)
    zone_vias: dict[int, dict] = {}  # net_num -> via stats within zone
    # For each zone, count vias on the same net within the zone outline
    # (approximate: use bounding box of zone outline)
    zone_bounds: list[dict] = []
    for z in zones:
        zn = z.get("net", 0)
        if zn <= 0:
            continue
        # Use the outline_area as a proxy — if we had the actual outline
        # points we could do point-in-polygon, but for a first pass,
        # just count all vias on the same net
        zone_bounds.append({
            "net": zn,
            "net_name": z.get("net_name", ""),
            "layers": z.get("layers", []),
            "area_mm2": z.get("outline_area_mm2", 0),
            "filled_area_mm2": z.get("filled_area_mm2"),
        })

    # Count vias per net
    via_by_net: dict[int, list[dict]] = {}
    for via in vias.get("vias", []):
        net = via.get("net", 0)
        if net > 0:
            via_by_net.setdefault(net, []).append(via)

    # Aggregate zone polygons by net before computing stitching density
    net_zones: dict[int, dict] = {}
    for zb in zone_bounds:
        net = zb["net"]
        if net not in net_zones:
            net_zones[net] = {
                "net_name": zb["net_name"],
                "layers": set(),
                "total_area_mm2": 0,
            }
        net_zones[net]["layers"].update(zb["layers"])
        net_zones[net]["total_area_mm2"] += zb.get("area_mm2", 0)

    # Zone stitching analysis — one entry per net
    stitching = []
    for net, info in net_zones.items():
        net_vias = via_by_net.get(net, [])
        if not net_vias:
            continue
        area = info["total_area_mm2"]

        entry = {
            "net": info["net_name"],
            "zone_layers": sorted(info["layers"]),
            "zone_area_mm2": round(area, 1) if area else None,
            "via_count": len(net_vias),
        }
        if area > 0:
            entry["via_density_per_cm2"] = round(len(net_vias) / (area / 100.0), 1)

        # Check drill sizes
        drills = set()
        for v in net_vias:
            if v.get("drill"):
                drills.add(v["drill"])
        if drills:
            entry["drill_sizes_mm"] = sorted(drills)

        entry["detector"] = "analyze_thermal_vias"
        entry["rule_id"] = "TS-DET"
        entry["category"] = "thermal"
        entry["severity"] = "info"
        entry["confidence"] = "deterministic"
        entry["evidence_source"] = "topology"
        entry["summary"] = f"Zone stitching: {info['net_name']} {len(net_vias)} vias"
        entry["description"] = (
            f"Zone stitching on net {info['net_name']}: {len(net_vias)} vias "
            f"across layers {sorted(info['layers'])}."
        )
        entry["components"] = []
        entry["nets"] = [info["net_name"]]
        entry["pins"] = []
        entry["recommendation"] = ""
        entry["report_context"] = {
            "section": "Thermal",
            "impact": "Thermal/ground plane connectivity",
            "standard_ref": "",
        }
        stitching.append(entry)

    # Thermal pad detection — use shared helper for QFN/BGA/DFN packages
    thermal_pads = []
    for fp in footprints:
        ref = fp.get("reference", "")

        # Skip component types that don't have thermal pads
        ref_prefix = ""
        for c in ref:
            if c.isalpha():
                ref_prefix += c
            else:
                break
        if ref_prefix in ("BT", "TP", "J"):
            continue

        for pad in _find_thermal_pads(fp):
            pad_num = str(pad.get("number", ""))
            w = pad.get("width", 0)
            h = pad.get("height", 0)
            pad_area = w * h
            net_name = pad.get("net_name", "")

            ax = pad.get("abs_x", fp["x"])
            ay = pad.get("abs_y", fp["y"])

            # Count standalone vias near this thermal pad
            standalone_vias = 0
            for via in vias.get("vias", []):
                if via.get("net") == pad.get("net_number", -1):
                    dx = via["x"] - ax
                    dy = via["y"] - ay
                    if math.sqrt(dx * dx + dy * dy) < max(w, h) * 1.5:
                        standalone_vias += 1

            # Count thru_hole pads in the same footprint on the same
            # net — these are footprint-embedded thermal vias
            footprint_via_pads = 0
            pad_net = pad.get("net_number", -1)
            for other_pad in fp.get("pads", []):
                if other_pad is pad:
                    continue
                if (other_pad.get("type") == "thru_hole" and
                        other_pad.get("net_number", -2) == pad_net and
                        pad_net >= 0):
                    footprint_via_pads += 1

            nearby_vias = standalone_vias + footprint_via_pads
            thermal_pads.append({
                "component": ref,
                "pad": pad_num,
                "pad_size_mm": [round(w, 2), round(h, 2)],
                "pad_area_mm2": round(pad_area, 2),
                "net": net_name,
                "nearby_thermal_vias": nearby_vias,
                "standalone_vias": standalone_vias,
                "footprint_via_pads": footprint_via_pads,
                "layer": fp.get("layer", "F.Cu"),
                "detector": "analyze_thermal_vias",
                "rule_id": "TP-DET",
                "category": "thermal",
                "severity": "info",
                "confidence": "deterministic",
                "evidence_source": "topology",
                "summary": f"Thermal pad: {ref} pad {pad_num} {nearby_vias} nearby vias",
                "description": (
                    f"Thermal pad on {ref} pad {pad_num}: "
                    f"{nearby_vias} nearby vias ({standalone_vias} standalone, "
                    f"{footprint_via_pads} footprint)."
                ),
                "components": [ref],
                "nets": [net_name],
                "pins": [pad_num],
                "recommendation": "",
                "report_context": {
                    "section": "Thermal",
                    "impact": "Thermal dissipation",
                    "standard_ref": "",
                },
            })

    return {
        "zone_stitching": stitching,
        "thermal_pads": thermal_pads,
    }
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
