levi2234/ChimeraMultiFX/.agents/skills/kicad/scripts/analyze_schematic.py

#!/usr/bin/env python3
"""
KiCad Schematic Analyzer — comprehensive single-pass extraction.

Parses a .kicad_sch file and outputs structured JSON with:
- Component inventory (BOM data, properties, positions)
- Net connectivity (wires, labels, junctions, no-connects, power symbols)
- Pin-level connectivity map (which pin connects to which net)
- Subcircuit identification hints
- Design statistics

Usage:
    python analyze_schematic.py <file.kicad_sch|file.kicad_pro|dir/> [--output file.json]

Output is JSON to stdout (or file if --output specified).
"""

import json
import math
import os
import re
import sys
from pathlib import Path

# Add scripts dir to path for sexp_parser and kicad_utils
sys.path.insert(0, str(Path(__file__).parent))
from sexp_parser import (
    find_all,
    find_deep,
    find_first,
    get_at,
    get_properties,
    get_property,
    get_value,
    has_flag,
    parse_file,
)
from kicad_utils import (
    COORD_EPSILON,
    _MIL_MM,
    _OUTPUT_DRIVE_KEYWORDS,
    classify_component,
    classify_connector,
    classify_ic_function,
    extract_pro_text_variables,
    format_frequency as _format_frequency,
    load_lib_tables,
    is_ground_name as _is_ground_name,
    is_usb_data_net_name,
    is_power_net_name as _is_power_net_name,
    load_kicad_pro,
    parse_value,
    parse_voltage_from_net_name as _parse_voltage_from_net_name,
    snap_to_mil_grid as _snap_mil,
)
from kicad_types import AnalysisContext
from signal_detectors import (
    audit_power_pin_dc_paths,
    audit_rail_sources,
    detect_bridge_circuits,
    detect_crystal_circuits,
    detect_current_sense,
    detect_decoupling,
    detect_design_observations,
    detect_integrated_ldos,
    detect_label_aliases,
    detect_lc_filters,
    detect_led_drivers,
    detect_opamp_circuits,
    detect_power_regulators,
    detect_protection_devices,
    detect_rc_filters,
    detect_solder_jumpers,
    detect_transistor_circuits,
    detect_voltage_dividers,
    postfilter_vd_and_dedup,
    _merge_series_dividers,
)
from domain_detectors import (
    audit_connector_ground_distribution,
    audit_esd_protection,
    audit_led_circuits,
    detect_adc_circuits,
    detect_addressable_leds,
    detect_audio_circuits,
    detect_battery_chargers,
    detect_bms_systems,
    detect_buzzer_speakers,
    detect_clock_distribution,
    detect_debug_interfaces,
    detect_display_interfaces,
    detect_ethernet_interfaces,
    detect_hdmi_dvi_interfaces,
    detect_isolation_barriers,
    detect_key_matrices,
    detect_lvds_interfaces,
    detect_led_driver_ics,
    detect_level_shifters,
    detect_memory_interfaces,
    detect_motor_drivers,
    detect_power_path,
    detect_reset_supervisors,
    detect_rf_chains,
    detect_rf_matching,
    detect_rtc_circuits,
    detect_sensor_interfaces,
    detect_thermocouple_rtd,
    suggest_certifications,
    validate_power_sequencing,
    detect_wireless_modules,
    detect_transformer_feedback,
    detect_i2c_address_conflicts,
    detect_energy_harvesting,
    detect_pwm_led_dimming,
    detect_headphone_jack,
)
from validation_detectors import (
    validate_pullups,
    validate_voltage_levels,
    validate_i2c_bus,
    validate_spi_bus,
    validate_can_bus,
    validate_usb_bus,
    validate_power_sequencing as validate_power_seq_deps,
    validate_led_resistors,
    validate_feedback_stability,
    validate_crystal_load_caps,
)
from lookup_detectors import (
    detect_absolute_max_violations,
    detect_vcc_outside_recommended,
    detect_5v_on_non_tolerant_pin,
    detect_wrong_signal_type,
    detect_missing_required_components,
)
from finding_schema import compute_trust_summary, sort_findings, make_finding, assign_finding_ids
from envelopes.schematic import SchematicEnvelope
from schema_codec import emit_schema
from inputs_builder import build_inputs, build_compat
from capability_mode import get_capability_mode_ref
from lookup_helpers import read_design_context


def _resolve_lookup_paths(sch_path: str | Path,
                           analysis_dir: str | Path | None) -> tuple[Path | None, dict | None]:
    """Resolve (cache_dir, design_context) for AnalysisContext (Phase 4d-active).

    cache_dir is the datasheets/extracted/ directory adjacent to the schematic
    (matching the existing convention used by analyze_thermal.py and the
    audit_datasheet_coverage check). Returns None when the directory doesn't
    exist — `lookup()` already handles None gracefully.

    design_context is the parsed design_context.json from the analysis dir,
    or None when absent or analysis_dir is None.
    """
    sch_dir = Path(sch_path).resolve().parent
    candidates = [
        sch_dir / "datasheets" / "extracted",
        sch_dir.parent / "datasheets" / "extracted",
    ]
    cache_dir = next((c for c in candidates if c.is_dir()), None)
    dc = read_design_context(analysis_dir) if analysis_dir else None
    return cache_dir, dc

ANALYZER_SOURCE = "sch"

# ---------------------------------------------------------------------------
# Case-insensitive distributor / MPN property helpers
# ---------------------------------------------------------------------------
_UUID_RE = re.compile(
    r'[0-9a-f]{8}-[0-9a-f]{4}-[0-9a-f]{4}-[0-9a-f]{4}-[0-9a-f]{12}',
    re.IGNORECASE,
)


def _clean_hierarchical_name(name: str) -> str:
    """Strip UUID path prefixes from hierarchical net/rail names.

    ``/201ab4ae-...-c6b37cf9a2b1/VIN`` → ``VIN``
    """
    if '/' in name and _UUID_RE.search(name):
        return name.rsplit('/', 1)[-1]
    return name


# KiCad lets users name fields however they like — "Digikey", "DigiKey",
# "DIGIKEY", "Digi-Key Part Number" are all common.  Rather than maintaining
# an ever-growing list of explicit variants, build a lowercase property dict
# once and match against normalised known aliases.

_MPN_KEYS = frozenset({
    "mpn", "mfg part", "partnumber", "part number", "part#",
    "manufacturer_part_number", "mfr no.", "mfr_no",
    "manufacturerpartnumber", "partno", "partno.", "mfr_part_number",
})
_MANUFACTURER_KEYS = frozenset({
    "manufacturer", "mfr", "mfg",
})
_DIGIKEY_KEYS = frozenset({
    "digikey", "digi-key", "digi-key part number", "digi-key_pn",
    "digikey part", "digikey part number", "digikey_part_number",
    "digi-key pn", "digikey part number", "dk",
})
_MOUSER_KEYS = frozenset({
    "mouser", "mouser part number", "mouser part", "mouser_pn", "mouser pn",
})
_LCSC_KEYS = frozenset({
    "lcsc", "lcsc part #", "lcsc part number", "lcsc part",
    "lcscstockcode", "jlcpcb", "jlcpcb part", "jlc",
})
_ELEMENT14_KEYS = frozenset({
    "newark", "newark part number", "newark_pn", "newark pn",
    "farnell", "farnell part number", "farnell_pn", "farnell pn",
    "element14", "element14 part number", "element14_pn",
})


def _pick(props: dict, keys: frozenset) -> str:
    """Return the first non-empty value whose lowercased key is in *keys*."""
    for k in keys:
        v = props.get(k)
        if v:
            return v
    return ""




def extract_lib_symbols(root: list) -> dict:
    """Extract library symbol definitions (pin positions, types).

    For multi-unit symbols (e.g., STM32 with separate GPIO and power units),
    pins are stored per unit so compute_pin_positions can use the correct
    offsets for each placed unit instance.
    """
    lib_symbols_node = find_first(root, "lib_symbols")
    if not lib_symbols_node:
        return {}

    def _parse_single_pin(pin):
        """Parse a single pin S-expression node into a dict."""
        pin_type = pin[1] if len(pin) > 1 else "unknown"
        pin_shape = pin[2] if len(pin) > 2 else "unknown"
        at = get_at(pin)
        pin_name_node = find_first(pin, "name")
        pin_num_node = find_first(pin, "number")
        pin_name = str(pin_name_node[1]) if pin_name_node and len(pin_name_node) > 1 and pin_name_node[1] is not None else ""
        pin_num = str(pin_num_node[1]) if pin_num_node and len(pin_num_node) > 1 and pin_num_node[1] is not None else ""
        # Detect hidden pins — KiCad uses (hide yes) inside pin node
        hidden = has_flag(pin, "hide")
        return {
            "number": pin_num, "name": pin_name,
            "type": pin_type, "shape": pin_shape,
            "offset": list(at) if at else None,
            "hidden": hidden,
        }

    def _extract_pins_from_node(node):
        """Extract pin definitions directly from a symbol node (not recursing into sub-symbols)."""
        return [_parse_single_pin(child) for child in node
                if isinstance(child, list) and len(child) >= 3 and child[0] == "pin"]

    symbols = {}
    for sym in find_all(lib_symbols_node, "symbol"):
        name = sym[1] if len(sym) > 1 else "unknown"
        # Skip sub-unit symbols (e.g., "Device:C_0_1", "Device:C_1_1")
        # Real sub-units have _U_V suffix where BOTH U and V are digits.
        parts = name.split(":")[-1].rsplit("_", 2)
        if len(parts) >= 3 and parts[-1].isdigit() and parts[-2].isdigit():
            continue

        # Collect pins from sub-unit symbols, keyed by unit number.
        # Sub-symbols named like "SymName_U_V" where U is the unit number.
        # Unit 0 sub-symbols (_0_1) contain pins/graphics shared by all units.
        unit_pins: dict[int, list] = {}
        all_pins = []

        for child in sym:
            if not isinstance(child, list) or len(child) < 2 or child[0] != "symbol":
                continue
            sub_name = child[1] if isinstance(child[1], str) else ""
            # Parse unit number from sub-symbol name: "Name_U_V"
            parts = sub_name.rsplit("_", 2)
            if len(parts) >= 3 and parts[-1].isdigit() and parts[-2].isdigit():
                unit_num = int(parts[-2])
                sub_pins = _extract_pins_from_node(child)
                if sub_pins:
                    unit_pins.setdefault(unit_num, []).extend(sub_pins)
                    all_pins.extend(sub_pins)

        # If no sub-unit pins found, fall back to find_deep on the whole symbol
        if not all_pins:
            all_pins = [_parse_single_pin(pin) for pin in find_deep(sym, "pin") if len(pin) >= 3]

        # Get symbol properties
        desc = get_property(sym, "Description") or ""
        ki_keywords = get_property(sym, "ki_keywords") or ""
        ki_fp_filters = get_property(sym, "ki_fp_filters") or ""
        lib_value = get_property(sym, "Value") or ""

        # Check for (power) flag — marks this as a power symbol regardless of lib name
        # KiCad 8+ writes (power global) or (power local); pre-8.0 writes bare (power)
        is_power = any(
            isinstance(child, list) and len(child) >= 1 and child[0] == "power"
            for child in sym
        )
        # Track global vs local power scope (default: global for bare (power))
        power_scope = "global"
        if is_power:
            for child in sym:
                if isinstance(child, list) and len(child) >= 2 and child[0] == "power":
                    power_scope = child[1] if child[1] in ("global", "local") else "global"
                    break

        # Extract alternate pin definitions (dual-function pins, e.g., GPIO/SPI/UART)
        alternates = {}
        for pin in find_deep(sym, "pin"):
            pin_num_node = find_first(pin, "number")
            pin_num = pin_num_node[1] if pin_num_node and len(pin_num_node) > 1 else ""
            alts = []
            for child in pin:
                if isinstance(child, list) and len(child) >= 2 and child[0] == "alternate":
                    alt_name = child[1] if len(child) > 1 else ""
                    alt_type = child[2] if len(child) > 2 else ""
                    alt_shape = child[3] if len(child) > 3 else ""
                    alts.append({"name": alt_name, "type": alt_type, "shape": alt_shape})
            if alts:
                alternates[pin_num] = alts

        symbols[name] = {
            "pins": all_pins,
            "unit_pins": unit_pins if unit_pins else None,
            "value": lib_value,
            "description": desc,
            "keywords": ki_keywords,
            "is_power": is_power,
            "power_scope": power_scope if is_power else None,
            "ki_fp_filters": ki_fp_filters,
            "alternates": alternates if alternates else None,
        }

    return symbols


# KiCad Y-down base TRANSFORM matrix (x1,y1,x2,y2) per (at .. angle),
# from sch_io_kicad_sexpr_parser.cpp:3490-3497 (parseSchematicSymbol T_at).
_ANGLE_TRANSFORM = {
    0:   (1, 0, 0, 1),
    90:  (0, 1, -1, 0),
    180: (-1, 0, 0, -1),
    270: (0, -1, 1, 0),
}


def apply_rotation(px: float, py: float, angle_deg: float) -> tuple[float, float]:
    """Apply rotation to a pin offset. KiCad uses degrees, CCW positive."""
    # EQ-065: x'=x·cosθ-y·sinθ, y'=x·sinθ+y·cosθ (2D rotation)
    if angle_deg == 0:
        return px, py
    rad = math.radians(angle_deg)
    cos_a = round(math.cos(rad), 10)
    sin_a = round(math.sin(rad), 10)
    return (px * cos_a - py * sin_a, px * sin_a + py * cos_a)


def compute_pin_positions(component: dict, lib_symbols: dict) -> list[dict]:
    """Compute absolute pin positions for a placed component."""
    lib_id = component.get("lib_id", "")
    lib_name = component.get("lib_name", "")
    # KH-083: Try lib_name first (KiCad 7+ local name), then lib_id
    sym_def = (lib_symbols.get(lib_name) if lib_name else None) or lib_symbols.get(lib_id)
    if not sym_def:
        return []

    cx = component["x"]
    cy = component["y"]
    angle = component["angle"]
    mirror_x = component.get("mirror_x", False)
    mirror_y = component.get("mirror_y", False)

    # For multi-unit symbols, use pins from this unit PLUS unit 0 (shared pins).
    # In KiCad, sub-symbol _0_1 contains pins shared by all units (e.g., power pins).
    unit_num = component.get("unit")
    unit_pins_map = sym_def.get("unit_pins")
    if unit_num and unit_pins_map and unit_num in unit_pins_map:
        pins = list(unit_pins_map[unit_num])
        # Also include unit 0 (shared/common) pins if they exist
        if 0 in unit_pins_map:
            pins.extend(unit_pins_map[0])
    else:
        pins = sym_def["pins"]

    pin_positions = []
    for pin in pins:
        if not pin["offset"]:
            continue
        px, py = pin["offset"][0], pin["offset"][1]

        # Apply transform: prefer raw matrix (legacy KiCad 5) over decomposed angle/mirror
        transform_matrix = component.get("transform_matrix")
        if transform_matrix:
            a, b, c, d = transform_matrix
            rpx = a * px + b * py
            rpy = c * px + d * py
        else:
            # KiCad 6+: decomposed angle + mirror. Compose exactly as KiCad does
            # so rotation+mirror combos match (mirror inverts rotation handedness).
            # KiCad builds a Y-down 2x2 TRANSFORM: the (at .. angle) sets the base
            # rotation matrix, then (mirror x|y) is composed ON THE RIGHT via
            # new = old * mirror (sch_symbol.cpp:SetOrientation, lines 2937-2941).
            # TransformCoordinate(P)=(x1*Px+y1*Py, x2*Px+y2*Py) (kimath transform.cpp:40-43).
            # We work in math-up offsets (Py positive = up), so convert the Y-down
            # result back: rpx = x1*px - y1*py, rpy = -x2*px + y2*py.
            x1, y1, x2, y2 = _ANGLE_TRANSFORM.get(int(angle) % 360, (1, 0, 0, 1))
            if mirror_x:  # compose with SYM_MIRROR_X temp = (1,0,0,-1) on the right
                x1, y1, x2, y2 = x1, y1, -x2, -y2
            if mirror_y:  # compose with SYM_MIRROR_Y temp = (-1,0,0,1) on the right
                x1, y1, x2, y2 = -x1, -y1, x2, y2
            rpx = x1 * px - y1 * py
            rpy = -x2 * px + y2 * py

        # Absolute position: Y-axis inversion (symbol coords are math-up, schematic is screen-down)
        abs_x = round(cx + rpx, 4)
        abs_y = round(cy - rpy, 4)

        # Ensure pin number and name are never None — coerce to string with fallback
        pin_num = pin.get("number")
        pin_name = pin.get("name")
        if pin_num is None:
            pin_num = ""
        else:
            pin_num = str(pin_num)
        if pin_name is None:
            pin_name = ""
        else:
            pin_name = str(pin_name)

        entry = {
            "number": pin_num,
            "name": pin_name,
            "type": pin["type"],
            "x": abs_x,
            "y": abs_y,
        }
        if pin.get("hidden"):
            entry["hidden"] = True
        pin_positions.append(entry)

    return pin_positions


def extract_symbol_instances(root: list) -> dict:
    """Extract (symbol_instances ...) from root schematic.

    Returns a dict mapping path string -> {reference, unit, value, footprint}.
    Path format: "/sheet_uuid/symbol_uuid" or "/sheet_uuid/child_uuid/symbol_uuid".
    """
    result = {}
    si_node = find_first(root, "symbol_instances")
    if not si_node:
        return result
    for path_node in si_node[1:]:
        if not isinstance(path_node, list) or path_node[0] != "path":
            continue
        if len(path_node) < 2:
            continue
        path_str = path_node[1]
        ref = get_value(path_node, "reference") or ""
        unit_val = get_value(path_node, "unit")
        try:
            unit = int(unit_val) if unit_val else 1
        except (ValueError, TypeError):
            unit = 1
        result[path_str] = {
            "reference": ref,
            "unit": unit,
        }
    return result


def extract_components(root: list, lib_symbols: dict, instance_uuid: str = "",
                       symbol_instances: dict | None = None) -> list[dict]:
    """Extract all placed component instances.

    If instance_uuid is provided, remap references from the (instances) block
    for the specified sheet instance (supports multi-instance hierarchical sheets).

    If symbol_instances is provided (from root schematic), use it as a fallback
    when a symbol has no inline (instances) block (common in older KiCad projects).
    """
    components = []

    # Placed symbols are direct children of root with (symbol (lib_id ...))
    for sym in root:
        if not isinstance(sym, list) or len(sym) == 0 or sym[0] != "symbol":
            continue
        # Skip if this is in lib_symbols (those have string name as [1], not a sub-list)
        if len(sym) > 1 and isinstance(sym[1], str):
            continue

        lib_id = get_value(sym, "lib_id")
        if not lib_id:
            continue
        # KH-083: KiCad 7+ uses (lib_name X) when the local symbol name
        # differs from the library's lib_id (e.g., after Eagle import)
        lib_name = get_value(sym, "lib_name") or ""

        at = get_at(sym)
        x, y, angle = at if at else (0, 0, 0)

        # Check for mirror
        mirror_node = find_first(sym, "mirror")
        mirror_x = "x" in mirror_node if mirror_node else False
        mirror_y = "y" in mirror_node if mirror_node else False

        # Extract unit number for multi-unit symbols
        unit_node = find_first(sym, "unit")
        unit_num = int(unit_node[1]) if unit_node and len(unit_node) > 1 else None

        ref = get_property(sym, "Reference") or ""
        value = get_property(sym, "Value")
        # KH-088: Eagle-imported schematics often have NO instance Value property.
        # Fall back to the lib_symbol's Value property only when the property is
        # missing entirely (None), not when it exists but is empty string (KH-230).
        if value is None:
            sym_def_val = lib_symbols.get(lib_id, {})
            value = sym_def_val.get("value", "") or ""
        else:
            value = value or ""
        footprint = get_property(sym, "Footprint") or ""
        datasheet = get_property(sym, "Datasheet") or ""
        description = get_property(sym, "Description") or ""
        uuid_val = get_value(sym, "uuid") or ""

        # Remap reference from (instances) block for multi-instance sheets.
        # Two sources: inline (instances) in each symbol (KiCad 7+), or
        # centralized (symbol_instances) in the root schematic (KiCad 6/older projects).
        if instance_uuid:
            remapped = False
            instances_node = find_first(sym, "instances")
            if instances_node:
                for proj in instances_node[1:]:
                    if not isinstance(proj, list) or proj[0] != "project":
                        continue
                    for path_node in proj[2:]:
                        if not isinstance(path_node, list) or path_node[0] != "path":
                            continue
                        path_str = path_node[1] if len(path_node) > 1 else ""
                        if instance_uuid in path_str:
                            inst_ref = get_value(path_node, "reference")
                            if inst_ref:
                                ref = inst_ref
                                remapped = True
                            inst_unit = get_value(path_node, "unit")
                            if inst_unit:
                                try:
                                    unit_num = int(inst_unit)
                                except (ValueError, TypeError):
                                    pass
                            break

            # Fallback: use centralized symbol_instances from root schematic
            if not remapped and symbol_instances and uuid_val:
                # Build the lookup path: instance_uuid is a full hierarchical
                # path like "/sheet1_uuid" or "/sheet1_uuid/sheet2_uuid".
                # Append the symbol's own UUID to form the full path.
                lookup_path = instance_uuid + "/" + uuid_val
                si_entry = symbol_instances.get(lookup_path)
                if si_entry:
                    if si_entry["reference"]:
                        ref = si_entry["reference"]
                    if si_entry.get("unit"):
                        unit_num = si_entry["unit"]
        _props = get_properties(sym)
        mpn = _pick(_props, _MPN_KEYS)
        manufacturer = _pick(_props, _MANUFACTURER_KEYS)
        digikey = _pick(_props, _DIGIKEY_KEYS)
        mouser = _pick(_props, _MOUSER_KEYS)
        lcsc = _pick(_props, _LCSC_KEYS)
        element14 = _pick(_props, _ELEMENT14_KEYS)

        in_bom = get_value(sym, "in_bom") != "no"
        dnp = get_value(sym, "dnp") == "yes"
        if not dnp and value.upper() in ("DNP", "DO NOT POPULATE", "DO NOT PLACE", "NP"):
            dnp = True
        on_board = get_value(sym, "on_board") != "no"

        # Get pin UUIDs for connectivity
        pin_uuids = {}
        for pin_node in find_all(sym, "pin"):
            if len(pin_node) >= 2:
                pin_num = pin_node[1]
                pin_uuid_node = find_first(pin_node, "uuid")
                if pin_uuid_node and len(pin_uuid_node) > 1:
                    pin_uuids[pin_num] = pin_uuid_node[1]

        comp = {
            "reference": ref,
            "value": value,
            "lib_id": lib_id,
            "lib_name": lib_name,
            "footprint": footprint,
            "datasheet": datasheet,
            "description": description,
            "mpn": mpn,
            "manufacturer": manufacturer,
            "digikey": digikey,
            "mouser": mouser,
            "lcsc": lcsc,
            "element14": element14,
            "x": x,
            "y": y,
            "angle": angle,
            "mirror_x": mirror_x,
            "mirror_y": mirror_y,
            "unit": unit_num,
            "uuid": uuid_val,
            "in_bom": in_bom,
            "dnp": dnp,
            "on_board": on_board,
            "pin_uuids": pin_uuids,
        }

        # Determine component type from reference prefix, lib_id, and lib_symbol flags
        # KH-083: Try lib_name first for correct lib_symbol lookup
        sym_def = (lib_symbols.get(lib_name) if lib_name else None) or lib_symbols.get(lib_id, {})
        is_power_sym = sym_def.get("is_power", False)
        comp["type"] = classify_component(ref, lib_id, value, is_power_sym, footprint, in_bom=in_bom,
                                          description=description)
        # Store ki_keywords for downstream analysis (e.g., P-channel detection)
        comp["keywords"] = sym_def.get("keywords", "")
        # Track power scope (global vs local) for connectivity
        if is_power_sym:
            comp["_power_scope"] = sym_def.get("power_scope", "global")

        # Enrich ICs with functional classification
        if comp["type"] == "ic":
            comp["functional_class"] = classify_ic_function(lib_id, value, description)

        # Enrich connectors with external status and layout
        if comp["type"] == "connector":
            pin_count = len(sym_def.get("pins", [])) if sym_def else 0
            is_ext, conn_layout = classify_connector(lib_id, value, pin_count)
            comp["is_external_connector"] = is_ext
            comp["connector_layout"] = conn_layout

        # Compute absolute pin positions
        comp["pins"] = compute_pin_positions(comp, lib_symbols)
        # KH-216: Store unit-valid pin numbers for pin_nets filtering
        comp["_unit_pins"] = {p["number"] for p in comp["pins"]}

        components.append(comp)

    return components


def _build_net_classifications(results: dict) -> dict[str, dict]:
    """Build net classification dict from existing detector results.

    Tags nets with signal type and characteristics for downstream PCB
    intelligence checks. Uses the 'nets' field from rich-format detections
    plus domain-specific fields where available.
    """
    classifications: dict[str, dict] = {}

    # Crystal circuits → clock nets (from load_cap nets and rich 'nets' field)
    for xc in results.get('crystal_circuits', []):
        freq = xc.get('frequency')
        # Rich format 'nets' field contains the crystal's connected nets
        for net in xc.get('nets', []):
            if net and net not in classifications:
                classifications[net] = {'type': 'clock', 'frequency_hz': freq, 'source': 'crystal_circuits'}
        # Load cap nets are clock-passive
        for lc in xc.get('load_caps', []):
            net = lc.get('net')
            if net and net not in classifications:
                classifications[net] = {'type': 'clock_passive', 'source': 'crystal_circuits'}

    # Power regulators → switching nodes and power rails
    for reg in results.get('power_regulators', []):
        sw_net = reg.get('sw_net')
        if sw_net:
            classifications[sw_net] = {'type': 'switching_node', 'frequency_hz': reg.get('switching_frequency_hz'), 'source': 'power_regulators'}
        output_rail = reg.get('output_rail')
        if output_rail and output_rail not in classifications:
            classifications[output_rail] = {'type': 'power_rail', 'source': 'power_regulators'}

    # Ethernet → differential nets (from rich 'nets' or domain-specific fields)
    for eth in results.get('ethernet_interfaces', []):
        # Try domain-specific differential net fields first
        for key in ('tx_p', 'tx_n', 'rx_p', 'rx_n', 'txp', 'txn', 'rxp', 'rxn'):
            net = eth.get(key)
            if net:
                classifications[net] = {'type': 'ethernet', 'differential': True, 'source': 'ethernet_interfaces'}
        # Fall back to rich 'nets' field
        for net in eth.get('nets', []):
            if net and net not in classifications:
                classifications[net] = {'type': 'ethernet', 'source': 'ethernet_interfaces'}

    # HDMI/DVI
    for hdmi in results.get('hdmi_dvi_interfaces', []):
        for net in hdmi.get('nets', []):
            if net and net not in classifications:
                classifications[net] = {'type': 'hdmi', 'differential': True, 'source': 'hdmi_dvi_interfaces'}

    # Memory interfaces
    for mem in results.get('memory_interfaces', []):
        for net in mem.get('nets', []):
            if net and net not in classifications:
                classifications[net] = {'type': 'memory', 'source': 'memory_interfaces'}

    # LVDS
    for lvds in results.get('lvds_interfaces', []):
        for net in lvds.get('nets', []):
            if net and net not in classifications:
                classifications[net] = {'type': 'lvds', 'differential': True, 'source': 'lvds_interfaces'}

    # RF chains
    for rf in results.get('rf_chains', []):
        for net in rf.get('nets', []):
            if net and net not in classifications:
                classifications[net] = {'type': 'rf', 'source': 'rf_chains'}

    # Clock distribution
    for clk in results.get('clock_distribution', []):
        freq = clk.get('frequency_hz')
        for net in clk.get('nets', []):
            if net and net not in classifications:
                classifications[net] = {'type': 'clock', 'frequency_hz': freq, 'source': 'clock_distribution'}

    # Validation findings → protocol nets (I2C, CAN, USB)
    for vf in results.get('validation_findings', []):
        rule = vf.get('rule_id', '')
        nets = vf.get('nets', [])
        if rule == 'PR-001':
            for net in nets:
                if net not in classifications:
                    classifications[net] = {'type': 'i2c', 'source': 'protocol_detection'}
        elif rule == 'PR-003':
            for net in nets:
                if net not in classifications:
                    classifications[net] = {'type': 'can', 'differential': True, 'source': 'protocol_detection'}
        elif rule == 'PR-004':
            for net in nets:
                if net not in classifications:
                    classifications[net] = {'type': 'usb', 'differential': True, 'source': 'protocol_detection'}

    return classifications


def analyze_signal_paths(ctx: AnalysisContext) -> dict:
    """Analyze signal processing circuits: filters, dividers, feedback networks.

    Orchestrator that calls individual detector functions from signal_detectors.py.
    Each detector takes an AnalysisContext and returns its detection results.
    """
    nets = ctx.nets

    # Run detectors in dependency order
    vd_result = detect_voltage_dividers(ctx)
    voltage_dividers = vd_result["voltage_dividers"]
    # KH-105/KH-115: Merge series resistors in divider chains
    voltage_dividers = _merge_series_dividers(voltage_dividers, ctx)
    feedback_networks = vd_result["feedback_networks"]

    lc_filters = detect_lc_filters(ctx)
    crystal_circuits = detect_crystal_circuits(ctx)
    # KH-145: Detect opamps BEFORE RC filters so feedback components can be excluded
    opamp_circuits = detect_opamp_circuits(ctx)
    # KH-107: Pass crystal_circuits to exclude crystal R/C from RC filter detection
    # KH-145: Pass opamp_circuits to exclude feedback R+C from RC filter detection
    rc_filters = detect_rc_filters(ctx, voltage_dividers, crystal_circuits, opamp_circuits)
    decoupling_analysis = detect_decoupling(ctx)
    current_sense = detect_current_sense(ctx)
    power_regulators = detect_power_regulators(ctx, voltage_dividers)
    integrated_ldos = detect_integrated_ldos(ctx, power_regulators)
    power_regulators.extend(integrated_ldos)

    # Build rail_voltages: net name → voltage from regulator outputs + power symbol names
    rail_voltages: dict[str, float] = {}
    for reg in power_regulators:
        out_rail = reg.get("output_rail")
        v_out = reg.get("estimated_vout")
        if out_rail and v_out is not None:
            rail_voltages[_clean_hierarchical_name(out_rail)] = v_out
    # Augment with voltages inferred from power symbol / net names
    for net_name in ctx.nets:
        clean = _clean_hierarchical_name(net_name)
        if clean not in rail_voltages:
            v = _estimate_rail_voltage(clean)
            if v is not None:
                rail_voltages[clean] = v

    protection_devices = detect_protection_devices(ctx)
    bridge_circuits, matched_fets, fet_pins = detect_bridge_circuits(ctx)
    transistor_circuits = detect_transistor_circuits(ctx, matched_fets, fet_pins)

    # Post-processing that needs cross-detector data
    voltage_dividers, feedback_networks = postfilter_vd_and_dedup(
        voltage_dividers, feedback_networks, transistor_circuits, nets=ctx.nets)
    detect_led_drivers(ctx, transistor_circuits)
    buzzer_speaker_circuits = detect_buzzer_speakers(ctx, transistor_circuits)
    key_matrices = detect_key_matrices(ctx)
    isolation_barriers = detect_isolation_barriers(ctx)
    ethernet_interfaces = detect_ethernet_interfaces(ctx)
    hdmi_dvi_interfaces = detect_hdmi_dvi_interfaces(ctx)
    lvds_interfaces = detect_lvds_interfaces(ctx)
    memory_interfaces = detect_memory_interfaces(ctx)
    rf_chains = detect_rf_chains(ctx)
    rf_matching = detect_rf_matching(ctx)
    bms_systems = detect_bms_systems(ctx)
    battery_chargers = detect_battery_chargers(ctx)
    motor_drivers = detect_motor_drivers(ctx)
    addressable_led_chains = detect_addressable_leds(ctx)
    debug_interfaces = detect_debug_interfaces(ctx)
    power_path = detect_power_path(ctx)
    esd_coverage_audit = audit_esd_protection(ctx, protection_devices)
    adc_circuits = detect_adc_circuits(ctx, rc_filters, protection_devices)
    reset_supervisors = detect_reset_supervisors(ctx)
    clock_distribution = detect_clock_distribution(ctx, crystal_circuits)
    display_interfaces = detect_display_interfaces(ctx)
    sensor_interfaces = detect_sensor_interfaces(ctx)
    level_shifters = detect_level_shifters(ctx)
    audio_circuits = detect_audio_circuits(ctx)
    led_driver_ics = detect_led_driver_ics(ctx)
    rtc_circuits = detect_rtc_circuits(ctx, crystal_circuits)
    led_audit = audit_led_circuits(ctx, transistor_circuits)
    thermocouple_rtd = detect_thermocouple_rtd(ctx)
    power_sequencing_validation = validate_power_sequencing(
        ctx, power_regulators, power_path, reset_supervisors)
    connector_ground_audit = audit_connector_ground_distribution(ctx)

    # Validation detectors (rich findings)
    pullup_findings = validate_pullups(ctx)
    voltage_level_findings = validate_voltage_levels(ctx, level_shifters)
    i2c_findings = validate_i2c_bus(ctx)
    spi_findings = validate_spi_bus(ctx)
    can_findings = validate_can_bus(ctx)
    usb_findings = validate_usb_bus(ctx)
    power_seq_dep_findings = validate_power_seq_deps(ctx, power_regulators)
    led_resistor_findings = validate_led_resistors(ctx)
    feedback_stability_findings = validate_feedback_stability(ctx, power_regulators)
    crystal_load_findings = validate_crystal_load_caps(ctx, crystal_circuits)

    # Lookup detectors (Phase 4c) — consume v1.4 datasheet facts via lookup().
    # Soft-skip when get_facts() returns None (no MPN cache). Synonym-resolved
    # rail keys per addendum §A2; per-pin Pin.absolute_max overrides rail-level.
    am_001_findings = detect_absolute_max_violations(ctx, rail_voltages)
    ov_001_findings = detect_vcc_outside_recommended(ctx, rail_voltages)
    ft_001_findings = detect_5v_on_non_tolerant_pin(ctx, rail_voltages)
    pm_001_findings = detect_wrong_signal_type(ctx)
    ex_001_findings = detect_missing_required_components(ctx, power_regulators)

    # New domain detectors (rich format)
    wireless_modules = detect_wireless_modules(ctx)
    transformer_feedback = detect_transformer_feedback(ctx)
    i2c_address_conflicts = detect_i2c_address_conflicts(ctx)
    energy_harvesting = detect_energy_harvesting(ctx)
    pwm_led_dimming = detect_pwm_led_dimming(ctx, transistor_circuits)
    headphone_jacks = detect_headphone_jack(ctx)
    solder_jumpers = detect_solder_jumpers(ctx)
    rail_source_audit = audit_rail_sources(
        ctx, power_regulators=power_regulators, solder_jumpers=solder_jumpers)
    label_aliases = detect_label_aliases(ctx)
    power_pin_dc_paths = audit_power_pin_dc_paths(
        ctx, solder_jumpers=solder_jumpers)

    # Remove R/C components that appear in crystal circuits from RC filter
    # results — prevents misclassifying crystal feedback resistors + load caps
    # as RC filters (e.g., "10M + 22pF = 723Hz RC filter").
    if crystal_circuits and rc_filters:
        xtal_refs = set()
        for xc in crystal_circuits:
            for lc in xc.get("load_caps", []):
                xtal_refs.add(lc["ref"])
            if "feedback_resistor" in xc:
                xtal_refs.add(xc["feedback_resistor"])
        if xtal_refs:
            rc_filters = [
                f for f in rc_filters
                if f.get("resistor", {}).get("reference") not in xtal_refs
                and f.get("capacitor", {}).get("reference") not in xtal_refs
            ]

    def _enrich_capacitor_data(results_dict, context):
        """Add package size, ESR, dielectric, and rated voltage to all cap entries.

        Walks through all detection dicts recursively, finds entries with a 'farads'
        key and a 'ref' key, and adds derived fields from the component's footprint
        and value string.
        """
        from kicad_utils import (extract_cap_package, estimate_cap_esr,
                                 classify_dielectric, parse_rated_voltage)

        def _enrich(obj):
            if isinstance(obj, dict):
                if "farads" in obj and "ref" in obj:
                    ref = obj["ref"]
                    comp = context.comp_lookup.get(ref)
                    if comp:
                        # Package and ESR (existing)
                        if "package" not in obj:
                            fp = comp.get("footprint", "")
                            pkg = extract_cap_package(fp)
                            if pkg:
                                obj["package"] = pkg
                                esr = estimate_cap_esr(obj["farads"], pkg)
                                if esr is not None:
                                    obj["esr_ohm"] = esr
                        # Dielectric classification (new)
                        if "dielectric" not in obj:
                            value_str = comp.get("value", "")
                            desc_str = comp.get("description", "")
                            obj["dielectric"] = classify_dielectric(value_str, desc_str)
                        # Rated voltage (new)
                        if "rated_voltage_V" not in obj:
                            value_str = comp.get("value", "")
                            rv = parse_rated_voltage(value_str)
                            if rv is not None:
                                obj["rated_voltage_V"] = rv
                for v in obj.values():
                    _enrich(v)
            elif isinstance(obj, list):
                for item in obj:
                    _enrich(item)

        _enrich(results_dict)

    def _apply_capacitor_derating(results_dict):
        """Apply DC bias derating to capacitor entries where applied voltage is known.

        Cross-references regulator output voltages with output_capacitors and
        decoupling_analysis to compute effective_farads after DC bias derating.
        Only adds derating fields when both package and applied voltage are known.
        """
        from kicad_utils import estimate_dc_bias_derating

        # Build rail → voltage map from power regulators
        rail_voltage = {}
        for reg in results_dict.get("power_regulators", []):
            vout = reg.get("vout_estimated") or reg.get("estimated_vout")
            rail = reg.get("output_rail", "")
            if vout and vout > 0 and rail:
                # Use the highest voltage seen for a rail (conservative)
                if rail not in rail_voltage or vout > rail_voltage[rail]:
                    rail_voltage[rail] = vout

        def _derate_cap(cap, applied_v):
            """Add derating fields to a single cap entry."""
            farads = cap.get("farads", 0)
            package = cap.get("package")
            dielectric = cap.get("dielectric")
            if not farads or farads <= 0 or not package or not dielectric:
                return

            # Determine rated voltage: from cap entry, or estimate from rail
            rated_v = cap.get("rated_voltage_V")
            if rated_v is None:
                # Conservative estimate based on typical voltage ratings
                if applied_v <= 1.8:
                    rated_v = 6.3
                elif applied_v <= 3.3:
                    rated_v = 6.3
                elif applied_v <= 5.0:
                    rated_v = 10.0
                elif applied_v <= 12.0:
                    rated_v = 25.0
                else:
                    rated_v = applied_v * 2  # assume 2:1 margin

            voltage_ratio = applied_v / rated_v
            remaining = estimate_dc_bias_derating(dielectric, package, voltage_ratio)

            cap["applied_voltage_V"] = applied_v
            cap["derating_factor"] = round(remaining, 3)
            cap["effective_farads"] = farads * remaining

        # Derate output and input capacitors on power regulators
        for reg in results_dict.get("power_regulators", []):
            vout = reg.get("vout_estimated") or reg.get("estimated_vout")
            if not vout or vout <= 0:
                continue
            for cap in reg.get("output_capacitors", []):
                _derate_cap(cap, vout)

        # Derate decoupling analysis capacitors
        for rail_entry in results_dict.get("decoupling_analysis", []):
            rail_name = rail_entry.get("rail", "")
            v = rail_voltage.get(rail_name)
            if not v:
                continue
            any_derated = False
            for cap in rail_entry.get("capacitors", []):
                _derate_cap(cap, v)
                if "effective_farads" in cap:
                    any_derated = True
            # Add total effective capacitance alongside nominal
            if any_derated:
                total_eff = sum(
                    c.get("effective_farads", c["farads"])
                    for c in rail_entry["capacitors"]
                )
                rail_entry["total_effective_capacitance_uF"] = round(total_eff * 1e6, 3)

        # Derate LC filter capacitors where rail voltage is known
        for filt in results_dict.get("lc_filters", []):
            rail = filt.get("rail", "")
            v = rail_voltage.get(rail)
            if v and "capacitor" in filt:
                cap = filt["capacitor"]
                if isinstance(cap, dict) and "farads" in cap:
                    _derate_cap(cap, v)

    results = {
        "rail_voltages": rail_voltages,
        "voltage_dividers": voltage_dividers,
        "rc_filters": rc_filters,
        "lc_filters": lc_filters,
        "feedback_networks": feedback_networks,
        "crystal_circuits": crystal_circuits,
        "snubbers": [],
        "decoupling_analysis": decoupling_analysis,
        "current_sense": current_sense,
        "power_regulators": power_regulators,
        "protection_devices": protection_devices,
        "opamp_circuits": opamp_circuits,
        "bridge_circuits": bridge_circuits,
        "transistor_circuits": transistor_circuits,
        "buzzer_speaker_circuits": buzzer_speaker_circuits,
        "key_matrices": key_matrices,
        "isolation_barriers": isolation_barriers,
        "ethernet_interfaces": ethernet_interfaces,
        "hdmi_dvi_interfaces": hdmi_dvi_interfaces,
        "lvds_interfaces": lvds_interfaces,
        "memory_interfaces": memory_interfaces,
        "rf_chains": rf_chains,
        "rf_matching": rf_matching,
        "bms_systems": bms_systems,
        "battery_chargers": battery_chargers,
        "motor_drivers": motor_drivers,
        "addressable_led_chains": addressable_led_chains,
        "debug_interfaces": debug_interfaces,
        "power_path": power_path,
        "esd_coverage_audit": esd_coverage_audit,
        "adc_circuits": adc_circuits,
        "reset_supervisors": reset_supervisors,
        "clock_distribution": clock_distribution,
        "display_interfaces": display_interfaces,
        "sensor_interfaces": sensor_interfaces,
        "level_shifters": level_shifters,
        "audio_circuits": audio_circuits,
        "led_driver_ics": led_driver_ics,
        "rtc_circuits": rtc_circuits,
        "led_audit": led_audit,
        "thermocouple_rtd": thermocouple_rtd,
        "power_sequencing_validation": power_sequencing_validation,
        "connector_ground_audit": connector_ground_audit,
        "wireless_modules": wireless_modules,
        "transformer_feedback": transformer_feedback,
        "i2c_address_conflicts": i2c_address_conflicts,
        "energy_harvesting": energy_harvesting,
        "pwm_led_dimming": pwm_led_dimming,
        "headphone_jacks": headphone_jacks,
        "solder_jumpers": solder_jumpers,
        "rail_source_audit": rail_source_audit,
        "label_aliases": label_aliases,
        "power_pin_dc_paths": power_pin_dc_paths,
        "validation_findings": (
            pullup_findings +
            voltage_level_findings +
            i2c_findings +
            spi_findings +
            can_findings +
            usb_findings +
            power_seq_dep_findings +
            led_resistor_findings +
            feedback_stability_findings +
            crystal_load_findings
        ),
        "lookup_findings": (
            am_001_findings +
            ov_001_findings +
            ft_001_findings +
            pm_001_findings +
            ex_001_findings
        ),
    }

    net_classifications = _build_net_classifications(results)
    if net_classifications:
        results["net_classifications"] = net_classifications

    # Certification suggestions cross-reference all domain detections
    cert_suggestions = suggest_certifications(ctx, results)
    if cert_suggestions:
        results["suggested_certifications"] = cert_suggestions

    results["design_observations"] = detect_design_observations(ctx, results)

    # Post-process: enrich capacitor entries with package size and estimated ESR
    _enrich_capacitor_data(results, ctx)
    _apply_capacitor_derating(results)

    return results


def extract_wires(root: list) -> list[dict]:
    """Extract all wire segments."""
    wires = []
    for wire in find_all(root, "wire"):
        pts = find_first(wire, "pts")
        if not pts:
            continue
        xys = find_all(pts, "xy")
        if len(xys) >= 2:
            wires.append({
                "x1": float(xys[0][1]), "y1": float(xys[0][2]),
                "x2": float(xys[1][1]), "y2": float(xys[1][2]),
            })
    return wires


def extract_labels(root: list) -> list[dict]:
    """Extract all labels (local, global, hierarchical)."""
    labels = []

    for label_type in ["label", "global_label", "hierarchical_label", "directive_label"]:
        for lbl in find_all(root, label_type):
            name = lbl[1] if len(lbl) > 1 else ""
            # KH-078: Malformed s-expressions can yield a list instead of string
            if isinstance(name, list):
                name = str(name[0]) if name else ""
            at = get_at(lbl)
            x, y, angle = at if at else (0, 0, 0)
            # Shape field exists on global_label and hierarchical_label
            # Values: input, output, bidirectional, tri_state, passive
            shape = get_value(lbl, "shape") or ""
            entry = {
                "name": name,
                "type": label_type,
                "x": round(x, 4),
                "y": round(y, 4),
                "angle": angle,
            }
            if shape:
                entry["shape"] = shape
            labels.append(entry)

    return labels


def extract_power_symbols(components: list[dict]) -> list[dict]:
    """Extract power symbols from the component list (they define net names).

    Uses the computed pin positions (not the symbol placement point) so that
    power symbols connect to the correct wire endpoints in the net map.
    """
    power = []
    for comp in components:
        if comp["type"] == "power_symbol":
            # Use pin position if available (more accurate), fall back to symbol position
            pins = comp.get("pins", [])
            if pins:
                # Power symbols typically have one pin — use its position
                px, py = pins[0]["x"], pins[0]["y"]
            else:
                px, py = comp["x"], comp["y"]
            power.append({
                "net_name": comp["value"],
                "x": px,
                "y": py,
                "lib_id": comp["lib_id"],
                "_sheet": comp.get("_sheet", 0),
                "_power_scope": comp.get("_power_scope", "global"),
            })
    return power


def extract_junctions(root: list) -> list[dict]:
    """Extract junction points."""
    junctions = []
    for junc in find_all(root, "junction"):
        at = get_at(junc)
        if at:
            junctions.append({"x": round(at[0], 4), "y": round(at[1], 4)})
    return junctions


def extract_no_connects(root: list) -> list[dict]:
    """Extract no-connect markers."""
    ncs = []
    for nc in find_all(root, "no_connect"):
        at = get_at(nc)
        if at:
            ncs.append({"x": round(at[0], 4), "y": round(at[1], 4)})
    return ncs


def extract_text_annotations(root: list) -> list[dict]:
    """Extract text annotations (non-electrical notes placed on the schematic).

    These are designer notes, TODO comments, revision annotations, etc. placed
    on the schematic sheet as free text objects.  Includes both ``(text ...)``
    and ``(text_box ...)`` elements.
    """
    texts = []
    for txt in find_all(root, "text"):
        content = txt[1] if len(txt) > 1 and isinstance(txt[1], str) else ""
        if not content:
            continue
        at = get_at(txt)
        x, y, angle = at if at else (0, 0, 0)
        texts.append({
            "type": "text",
            "text": content,
            "x": round(x, 4),
            "y": round(y, 4),
            "angle": angle,
        })

    for tb in find_all(root, "text_box"):
        content = tb[1] if len(tb) > 1 and isinstance(tb[1], str) else ""
        if not content:
            continue
        at = get_at(tb)
        x, y, angle = at if at else (0, 0, 0)
        size_node = find_first(tb, "size")
        w = float(size_node[1]) if size_node and len(size_node) > 1 else 0
        h = float(size_node[2]) if size_node and len(size_node) > 2 else 0
        entry: dict = {
            "type": "text_box",
            "text": content,
            "x": round(x, 4),
            "y": round(y, 4),
            "angle": angle,
        }
        if w or h:
            entry["width"] = round(w, 4)
            entry["height"] = round(h, 4)
        texts.append(entry)

    return texts


def extract_bus_elements(root: list) -> dict:
    """Extract bus wires, bus entries, and bus aliases.

    Buses in KiCad group related signals (e.g., D[0..7]) into a single
    graphical wire. Bus entries connect individual signals to/from the bus.
    Bus aliases define named groups of signals.
    """
    buses = []
    for bus in find_all(root, "bus"):
        pts = find_first(bus, "pts")
        if pts:
            xys = find_all(pts, "xy")
            if len(xys) >= 2:
                buses.append({
                    "x1": float(xys[0][1]), "y1": float(xys[0][2]),
                    "x2": float(xys[1][1]), "y2": float(xys[1][2]),
                })

    bus_entries = []
    for entry in find_all(root, "bus_entry"):
        at = get_at(entry)
        if at:
            size = find_first(entry, "size")
            dx = float(size[1]) if size and len(size) > 1 else 0
            dy = float(size[2]) if size and len(size) > 2 else 0
            bus_entries.append({
                "x": round(at[0], 4), "y": round(at[1], 4),
                "dx": dx, "dy": dy,
            })

    bus_aliases = []
    for alias in find_all(root, "bus_alias"):
        name = alias[1] if len(alias) > 1 and isinstance(alias[1], str) else ""
        members_node = find_first(alias, "members")
        members = []
        if members_node:
            members = [m for m in members_node[1:] if isinstance(m, str)]
        if name:
            bus_aliases.append({"name": name, "members": members})

    return {
        "bus_wires": buses,
        "bus_entries": bus_entries,
        "bus_aliases": bus_aliases,
    }


def extract_title_block(root: list) -> dict:
    """Extract title block metadata (title, date, revision, company, comments).

    The title block is stored in a (title_block ...) node at the top level
    of each schematic sheet.
    """
    tb = find_first(root, "title_block")
    if not tb:
        return {}

    result = {}
    for field in ("title", "date", "rev", "company"):
        val = get_value(tb, field)
        if val:
            result[field] = val

    # Comments are numbered: (comment 1 "text"), (comment 2 "text"), ...
    for child in tb:
        if isinstance(child, list) and len(child) >= 3 and child[0] == "comment":
            try:
                num = int(child[1])
                text = child[2] if isinstance(child[2], str) else ""
                if text:
                    result[f"comment_{num}"] = text
            except (ValueError, TypeError):
                pass

    return result


def build_net_map(components: list[dict], wires: list[dict], labels: list[dict],
                  power_symbols: list[dict], junctions: list[dict],
                  no_connects: list[dict] | None = None) -> dict:
    """Build a connectivity map using union-find on coordinates.

    Groups all electrically connected points into nets, then names them
    from labels and power symbols.
    """
    EPSILON = COORD_EPSILON

    # Collect all electrical points
    # Each point: (sheet, x, y, source_info)
    # The sheet index keeps each sheet's coordinate space separate so that
    # wires on different sheets at the same (x,y) don't falsely merge.
    parent = {}
    point_info = {}  # key -> list of info dicts

    def key(x, y, sheet=0):
        return (sheet, round(x / EPSILON) * EPSILON, round(y / EPSILON) * EPSILON)

    def find(p):
        while parent.get(p, p) != p:
            parent[p] = parent.get(parent[p], parent[p])
            p = parent[p]
        return p

    def union(a, b):
        ra, rb = find(a), find(b)
        if ra != rb:
            parent[ra] = rb

    def add_point(x, y, info, sheet=0):
        k = key(x, y, sheet)
        if k not in parent:
            parent[k] = k
        point_info.setdefault(k, []).append(info)
        return k

    # Add component pins. PWR_FLAG is an ERC marker, not a real connection —
    # still register its position so the net gets a has_pwr_flag annotation.
    for comp in components:
        is_pwr_flag = comp.get("value") == "PWR_FLAG" or comp.get("type") == "power_flag"
        sheet = comp.get("_sheet", 0)
        for pin in comp.get("pins", []):
            if is_pwr_flag:
                add_point(pin["x"], pin["y"], {
                    "source": "pwr_flag",
                    "component": comp["reference"],
                }, sheet)
            else:
                add_point(pin["x"], pin["y"], {
                    "source": "pin",
                    "component": comp["reference"],
                    "pin_number": pin["number"],
                    "pin_name": pin["name"],
                    "pin_type": pin["type"],
                }, sheet)

    # Add wire endpoints and union them.
    # Also build a list of wire segments so we can detect points that land
    # mid-wire (labels, pins, junctions, power symbols placed on a wire
    # between its endpoints).
    wire_segments = []  # list of (k1, k2, x1, y1, x2, y2, sheet)
    # Spatial grid index for fast wire segment lookup — avoids O(W*P) scans.
    # Grid cell size of 5mm captures typical KiCad schematic wire lengths.
    _WIRE_GRID_SIZE = 5.0
    wire_grid: dict[tuple, list[int]] = {}  # (sheet, gx, gy) -> [index into wire_segments]

    for wire in wires:
        sheet = wire.get("_sheet", 0)
        k1 = add_point(wire["x1"], wire["y1"], {"source": "wire"}, sheet)
        k2 = add_point(wire["x2"], wire["y2"], {"source": "wire"}, sheet)
        union(k1, k2)
        idx = len(wire_segments)
        wire_segments.append((k1, k2, wire["x1"], wire["y1"], wire["x2"], wire["y2"], sheet))
        # Index this segment in all grid cells its bounding box overlaps
        min_x, max_x = min(wire["x1"], wire["x2"]), max(wire["x1"], wire["x2"])
        min_y, max_y = min(wire["y1"], wire["y2"]), max(wire["y1"], wire["y2"])
        gx0 = int(min_x // _WIRE_GRID_SIZE)
        gx1 = int(max_x // _WIRE_GRID_SIZE)
        gy0 = int(min_y // _WIRE_GRID_SIZE)
        gy1 = int(max_y // _WIRE_GRID_SIZE)
        for gx in range(gx0, gx1 + 1):
            for gy in range(gy0, gy1 + 1):
                wire_grid.setdefault((sheet, gx, gy), []).append(idx)

    def point_on_segment(px, py, x1, y1, x2, y2):
        """Check if point (px,py) lies on the wire segment (x1,y1)-(x2,y2)."""
        # Quick bounding box check with tolerance
        tol = 0.05
        if px < min(x1, x2) - tol or px > max(x1, x2) + tol:
            return False
        if py < min(y1, y2) - tol or py > max(y1, y2) + tol:
            return False
        # Cross product to check collinearity
        cross = (x2 - x1) * (py - y1) - (y2 - y1) * (px - x1)
        seg_len_sq = (x2 - x1) ** 2 + (y2 - y1) ** 2
        if seg_len_sq < tol * tol:
            return False
        # Distance from point to line, squared
        if abs(cross) / (seg_len_sq ** 0.5) > tol:
            return False
        return True

    def union_with_overlapping_wires(k, px, py, sheet=0):
        """Union point k with any wire segment it lies on (same sheet only)."""
        gx = int(px // _WIRE_GRID_SIZE)
        gy = int(py // _WIRE_GRID_SIZE)
        candidates = wire_grid.get((sheet, gx, gy), ())
        for idx in candidates:
            wk1, wk2, wx1, wy1, wx2, wy2, ws = wire_segments[idx]
            if point_on_segment(px, py, wx1, wy1, wx2, wy2):
                union(k, wk1)
                return  # one match is enough since wire endpoints are already unioned

    # Add labels — in KiCad, labels can be placed anywhere on a wire,
    # not just at endpoints, so we must check for mid-wire placement.
    label_keys: dict[str, list] = {}  # label_name -> list of coordinate keys
    for lbl in labels:
        sheet = lbl.get("_sheet", 0)
        # KH-078: Defensive coercion — malformed labels can have list names
        lbl_name = lbl["name"]
        if isinstance(lbl_name, list):
            lbl_name = str(lbl_name[0]) if lbl_name else ""
        k = add_point(lbl["x"], lbl["y"], {
            "source": "label",
            "name": lbl_name,
            "label_type": lbl["type"],
        }, sheet)
        # Only global labels and power symbols connect across sheets.
        # Local labels only connect within the same sheet (handled by wire union).
        if lbl["type"] in ("global_label", "hierarchical_label"):
            label_keys.setdefault(lbl_name, []).append(k)
        else:
            # Local labels: union same-name labels within this sheet only
            local_key = (lbl_name, sheet)
            label_keys.setdefault(local_key, []).append(k)
        union_with_overlapping_wires(k, lbl["x"], lbl["y"], sheet)

    # Add power symbols — compute actual pin position from lib symbol.
    # PWR_FLAG is a DRC-only marker (tells ERC a net has a power source).
    # It doesn't create real connectivity, so exclude it entirely.
    for ps in power_symbols:
        if ps["net_name"] == "PWR_FLAG":
            continue
        sheet = ps.get("_sheet", 0)
        k = add_point(ps["x"], ps["y"], {
            "source": "power_symbol",
            "net_name": ps["net_name"],
        }, sheet)
        # Global power symbols connect across all sheets; local power symbols
        # only connect within the same sheet (isolated power domains).
        if ps.get("_power_scope") == "local":
            local_key = (ps["net_name"], sheet)
            label_keys.setdefault(local_key, []).append(k)
        else:
            label_keys.setdefault(ps["net_name"], []).append(k)
        union_with_overlapping_wires(k, ps["x"], ps["y"], sheet)

    # Legacy hidden power-in pins: in KiCad 4/5, ICs could have invisible
    # power-in pins (VCC, GND) that create implicit global net connections
    # by pin name.  These pins have no wires attached — they connect solely
    # by their name matching other hidden power pins or power symbols.
    for comp in components:
        if comp.get("type") == "power_symbol":
            continue
        sheet = comp.get("_sheet", 0)
        for pin in comp.get("pins", []):
            if pin.get("hidden") and pin["type"] == "power_in" and pin["name"]:
                k = key(pin["x"], pin["y"], sheet)
                label_keys.setdefault(pin["name"], []).append(k)

    # Union global/hierarchical labels and power symbols with the same name.
    # This is what connects nets across different parts of the schematic.
    for lbl_name, keys in label_keys.items():
        for j in range(1, len(keys)):
            union(keys[0], keys[j])

    # Add junctions — also check mid-wire placement
    for junc in junctions:
        sheet = junc.get("_sheet", 0)
        k = add_point(junc["x"], junc["y"], {"source": "junction"}, sheet)
        union_with_overlapping_wires(k, junc["x"], junc["y"], sheet)

    # Add no-connect markers to the union-find so NC'd pins are absorbed into
    # the same group and the resulting net gets tagged as intentional NC.
    # Without this, NC'd pins that have no wire create isolated __unnamed_N nets
    # that look like unfinished connections to downstream analysis.
    if no_connects:
        for nc in no_connects:
            sheet = nc.get("_sheet", 0)
            k = add_point(nc["x"], nc["y"], {"source": "no_connect"}, sheet)
            union_with_overlapping_wires(k, nc["x"], nc["y"], sheet)

    # Build net groups
    net_groups: dict[tuple, list[tuple]] = {}
    for k in parent:
        root_k = find(k)
        net_groups.setdefault(root_k, []).append(k)

    # Name the nets
    nets = {}
    net_id = 0
    for root_k, members in net_groups.items():
        # Collect all info for this net
        all_info = []
        for m in members:
            all_info.extend(point_info.get(m, []))

        # Find net name using KiCad's priority:
        # global_label > power_symbol > hierarchical_label > local label > pin
        _NET_NAME_PRIORITY = {
            "global_label": 0,
            "power_symbol": 1,
            "hierarchical_label": 2,
            "label": 3,
            "directive_label": 4,
        }
        best_name = None
        best_priority = 999

        # Accumulate every global / hierarchical / local label attached to
        # this net (LB-001 reads this; also useful for report annotations).
        # Dedup by (name, label_type).
        net_labels_seen: set[tuple[str, str]] = set()
        net_labels: list[dict] = []

        for info in all_info:
            if info["source"] == "power_symbol":
                p = _NET_NAME_PRIORITY["power_symbol"]
                if p < best_priority:
                    best_name = info["net_name"]
                    best_priority = p
            elif info["source"] == "label":
                lbl_name = info.get("name") or ""
                lbl_type = info.get("label_type") or "label"
                p = _NET_NAME_PRIORITY.get(lbl_type, 3)
                if p < best_priority:
                    best_name = lbl_name
                    best_priority = p
                key_tuple = (lbl_name, lbl_type)
                if lbl_name and key_tuple not in net_labels_seen:
                    net_labels_seen.add(key_tuple)
                    net_labels.append({"name": lbl_name, "type": lbl_type})
        net_name = best_name

        # Check if any member of this group is a no-connect marker OR a
        # library-defined NC pin (pin type "no_connect" in the symbol def).
        has_nc_marker = (
            any(i["source"] == "no_connect" for i in all_info)
            or any(i.get("pin_type") in ("no_connect", "unconnected")
                   for i in all_info if i["source"] == "pin")
        )

        has_pwr_flag = any(i["source"] == "pwr_flag" for i in all_info)

        if net_name is None:
            # Only create unnamed nets if they have component pins
            has_pins = any(i["source"] == "pin" for i in all_info)
            if not has_pins:
                continue
            net_name = f"__unnamed_{net_id}"
            net_id += 1

        # Collect pin connections
        pin_connections = []
        for info in all_info:
            if info["source"] == "pin":
                pin_connections.append({
                    "component": info["component"],
                    "pin_number": info["pin_number"],
                    "pin_name": info["pin_name"],
                    "pin_type": info["pin_type"],
                })

        # Keep nets that have pin connections, OR named nets (from labels/power symbols)
        # even without pins — this supports legacy files where pin positions aren't available
        if pin_connections or not net_name.startswith("__unnamed_"):
            if net_name in nets:
                # Merge into existing net (can happen when a local label shares a
                # name with a power symbol or global label on a disconnected wire
                # network — e.g., a "GND" label on a connector that isn't wired
                # to the main GND power symbol network).
                nets[net_name]["pins"].extend(pin_connections)
                nets[net_name]["point_count"] += len(members)
                if has_nc_marker:
                    nets[net_name]["no_connect"] = True
                if has_pwr_flag:
                    nets[net_name]["has_pwr_flag"] = True
                existing_labels = nets[net_name].setdefault("labels", [])
                existing_seen = {(lbl["name"], lbl["type"]) for lbl in existing_labels}
                for nl in net_labels:
                    if (nl["name"], nl["type"]) not in existing_seen:
                        existing_labels.append(nl)
                        existing_seen.add((nl["name"], nl["type"]))
            else:
                nets[net_name] = {
                    "name": net_name,
                    "pins": pin_connections,
                    "point_count": len(members),
                    "no_connect": has_nc_marker,
                    "has_pwr_flag": has_pwr_flag,
                    "labels": net_labels,
                }

    return nets


def generate_bom(components: list[dict]) -> list[dict]:
    """Generate grouped BOM from components."""
    groups: dict[tuple, dict] = {}

    # Deduplicate multi-unit symbols — only count each reference once
    seen_refs = set()

    for comp in components:
        if comp["type"] in ("power_symbol", "power_flag", "flag"):
            continue
        if not comp["in_bom"]:
            continue
        if comp["reference"] in seen_refs:
            continue
        seen_refs.add(comp["reference"])

        # Group key: value + footprint + MPN (or just value + footprint if no MPN)
        group_key = (comp["value"], comp["footprint"], comp["mpn"])

        if group_key not in groups:
            groups[group_key] = {
                "value": comp["value"],
                "footprint": comp["footprint"],
                "mpn": comp["mpn"],
                "manufacturer": comp["manufacturer"],
                "digikey": comp["digikey"],
                "mouser": comp["mouser"],
                "lcsc": comp["lcsc"],
                "element14": comp["element14"],
                "datasheet": comp["datasheet"],
                "description": comp["description"],
                "references": [],
                "quantity": 0,
                "dnp": comp["dnp"],
                "type": comp["type"],
            }

        groups[group_key]["references"].append(comp["reference"])
        groups[group_key]["quantity"] += 1

    # Sort by reference
    bom = sorted(groups.values(), key=lambda g: g["references"][0] if g["references"] else "")
    return bom


def compute_statistics(components: list[dict], nets: dict, bom: list[dict],
                       wires: list[dict], no_connects: list[dict]) -> dict:
    """Compute summary statistics."""
    # Deduplicate multi-unit symbols by reference
    seen_refs = set()
    non_power = []
    for c in components:
        if c["type"] in ("power_symbol", "power_flag", "flag"):
            continue
        if c["reference"] in seen_refs:
            continue
        seen_refs.add(c["reference"])
        non_power.append(c)
    bom_items = [b for b in bom if not b["dnp"]]
    dnp_items = [b for b in bom if b["dnp"]]

    type_counts = {}
    for comp in non_power:
        t = comp["type"]
        type_counts[t] = type_counts.get(t, 0) + 1

    # Build power rails with estimated voltages
    power_rail_names = sorted(set(
        comp["value"] for comp in components if comp["type"] == "power_symbol"
    ))
    for net_name in nets:
        if _is_power_net_name(net_name):
            clean = _clean_hierarchical_name(net_name)
            if clean not in power_rail_names:
                power_rail_names.append(clean)
    power_rail_names = sorted(set(power_rail_names))

    power_rails = []
    for name in power_rail_names:
        clean = _clean_hierarchical_name(name)
        # Skip PWR_FLAG — it's an ERC directive, not a physical rail.
        if clean == "PWR_FLAG":
            continue
        v = _parse_voltage_from_net_name(clean)
        power_rails.append({"name": clean, "voltage": v})

    # Missing properties
    missing_mpn = [c["reference"] for c in non_power
                   if c["type"] not in ("test_point", "mounting_hole")
                   and not c["mpn"] and not c["dnp"] and c["in_bom"]]
    missing_footprint = [c["reference"] for c in non_power
                         if not c["footprint"] and c["in_bom"] and not c["dnp"]]

    return {
        "total_components": len(non_power),
        "unique_parts": len(bom_items),
        "dnp_parts": sum(b["quantity"] for b in dnp_items),
        "total_nets": len(nets),
        "total_wires": len(wires),
        "total_no_connects": len(no_connects),
        "component_types": type_counts,
        "power_rails": power_rails,
        "missing_mpn": missing_mpn,
        "missing_footprint": missing_footprint,
    }


def build_pin_to_net_map(nets: dict) -> dict:
    """Build a reverse map: (component, pin_number) -> (net_name, net_info)."""
    pin_net = {}
    for net_name, net_info in nets.items():
        for p in net_info["pins"]:
            pin_net[(p["component"], p["pin_number"])] = (net_name, net_info)
    return pin_net


def get_net_neighbors(net_info: dict, exclude_ref: str) -> list[dict]:
    """Get all components on a net except the given reference, with their details."""
    neighbors = []
    for p in net_info["pins"]:
        if p["component"] != exclude_ref and not p["component"].startswith("#"):
            neighbors.append({
                "component": p["component"],
                "pin_number": p["pin_number"],
                "pin_name": p["pin_name"],
                "pin_type": p["pin_type"],
            })
    return neighbors


# Static lookup tables for IC function classification (used by _classify_ic_function)
_IC_LIB_PREFIX_MAP = {
    "regulator_linear": "linear regulator",
    "regulator_switching": "switching regulator",
    "regulator_controller": "regulator controller",
    "amplifier_operational": "operational amplifier",
    "amplifier_audio": "audio amplifier",
    "amplifier_instrumentation": "instrumentation amplifier",
    "amplifier_difference": "difference amplifier",
    "amplifier_current": "current sense amplifier",
    "amplifier_buffer": "buffer amplifier",
    "amplifier_video": "video amplifier",
    "analog_adc": "ADC",
    "analog_dac": "DAC",
    "analog_switch": "analog switch",
    "comparator": "comparator",
    "converter_dcdc": "DC-DC converter",
    "driver_motor": "motor driver",
    "driver_led": "LED driver",
    "driver_gate": "gate driver",
    "driver_display": "display driver",
    "driver_fet": "FET driver",
    "interface_can_lin": "CAN/LIN transceiver",
    "interface_ethernet": "Ethernet PHY",
    "interface_usb": "USB interface",
    "interface_uart": "UART interface",
    "interface_spi": "SPI interface",
    "interface_i2c": "I2C interface",
    "interface_rs485": "RS-485 transceiver",
    "interface_lvds": "LVDS interface",
    "interface_hdmi": "HDMI interface",
    "interface_optical": "optical interface",
    "logic_74xx": "logic IC (74xx)",
    "logic_4000": "logic IC (4000 series)",
    "logic_level": "level shifter",
    "memory_eeprom": "EEPROM",
    "memory_flash": "flash memory",
    "memory_ram": "RAM",
    "memory_rom": "ROM",
    "mcu": "microcontroller",
    "fpga": "FPGA",
    "cpld": "CPLD",
    "dsp": "DSP",
    "power_management": "power management IC",
    "power_supervisor": "voltage supervisor",
    "power_protection": "power protection IC",
    "rf_amplifier": "RF amplifier",
    "rf_mixer": "RF mixer",
    "rf_switch": "RF switch",
    "rf": "RF IC",
    "sensor_temperature": "temperature sensor",
    "sensor_pressure": "pressure sensor",
    "sensor_humidity": "humidity sensor",
    "sensor_current": "current sensor",
    "sensor_motion": "motion sensor",
    "sensor_magnetic": "magnetic sensor",
    "sensor_optical": "optical sensor",
    "sensor": "sensor IC",
    "timer": "timer IC",
    "reference_voltage": "voltage reference",
}

_IC_VALUE_KEYWORDS = [
    # Microcontrollers
    (("esp32", "esp8266", "esp32s", "esp32c", "esp32h"), "microcontroller (ESP)"),
    (("stm32", "stm8"), "microcontroller (STM)"),
    (("atmega", "attiny", "at90", "atxmega"), "microcontroller (AVR)"),
    (("pic16", "pic18", "pic24", "pic32", "dspic"), "microcontroller (PIC)"),
    (("rp2040", "rp2350"), "microcontroller (RP)"),
    (("nrf51", "nrf52", "nrf53", "nrf91"), "microcontroller (nRF)"),
    (("samd", "same", "samg", "saml", "samr"), "microcontroller (SAM)"),
    (("msp430", "msp432"), "microcontroller (MSP)"),
    (("efm32", "efr32"), "microcontroller (EFx32)"),
    (("cy8c",), "microcontroller (Cypress)"),
    (("gd32",), "microcontroller (GD32)"),
    (("ch32",), "microcontroller (CH32)"),
    (("kb2040",), "microcontroller (RP dev board)"),
    # FPGAs
    (("ice40", "ecp5", "machxo", "nexus"), "FPGA (Lattice)"),
    (("xc7", "xc6", "xczu", "xc2", "xcku", "artix", "spartan", "kintex", "virtex", "zynq"), "FPGA (Xilinx)"),
    (("10cl", "10m0", "5cg", "max10", "cyclone"), "FPGA (Intel)"),
    # Regulators
    (("lm117", "lm317", "lm337", "lm78", "lm79", "ams1117", "ap2112",
          "mic5205", "mic5504", "xc6206", "xc6220", "tps73", "tps76", "rt9013",
          "ld1117", "mcp1700", "mcp1703", "mcp1826", "ht7333", "ht7350"), "linear regulator"),
    (("lm2596", "lm2576", "mc34063", "tps54", "tps56", "tps61", "tps62",
          "tps63", "tps65", "mp1584", "mp2307", "mp2315", "mp2359",
          "ap3012", "sy80", "mt3608"), "switching regulator"),
    # Shift registers / logic
    (("74hc", "74lvc", "74ahc", "74act", "74ac", "sn74"), "logic IC"),
    (("cd4", "hef4", "mc14"), "logic IC (CMOS)"),
    # Communication
    (("max232", "max3232", "sp3232"), "RS-232 transceiver"),
    (("max485", "max3485", "sn65hvd", "thvd1", "isl317"), "RS-485 transceiver"),
    (("mcp2515", "mcp2551", "mcp2562", "sn65hvd23", "tja1"), "CAN transceiver"),
    (("cp2102", "ch340", "ft232", "ft2232", "pl2303", "ch9102"), "USB-UART bridge"),
    (("usb3300", "usb3320", "usb2514", "tusb"), "USB IC"),
    (("lan87", "lan91", "lan8720", "lan8710", "ksz", "dp83", "rtl81", "ip101"), "Ethernet PHY"),
    (("w5500", "w5100", "enc28j60"), "Ethernet controller"),
    (("sx127", "sx126", "rfm9", "rfm6", "cc1101", "at86rf"), "radio transceiver"),
    # Audio
    (("max9", "ssm2", "tpa", "lm386", "tda", "pam8"), "audio amplifier"),
    (("wm8", "es8", "ak4", "pcm51", "pcm17", "cs42", "sgtl5", "tlv320"), "audio codec"),
    # Display / LED
    (("ssd1306", "ssd1309", "st7735", "st7789", "ili9", "hx8357",
          "uc1701", "nt35", "sharp_ls"), "display controller"),
    (("ws2812", "sk6812", "apa102", "ws2813", "ws2815"), "addressable LED"),
    (("pca9685", "tlc5940", "is31fl"), "LED driver IC"),
    # Sensors
    (("bme280", "bme680", "bmp280", "bmp390"), "environmental sensor"),
    (("mpu6", "mpu9", "icm20", "lsm6", "bno0", "lis3"), "IMU/motion sensor"),
    (("ina21", "ina22", "ina23", "ina18", "ina19"), "current sense amplifier"),
    (("ads1", "mcp33", "mcp34", "mcp35", "max114", "max119"), "ADC"),
    (("mcp47", "dac8", "ad56", "ad57"), "DAC"),
    # Power management
    (("bq24", "bq25", "bq40", "ltc40", "mcp738"), "battery management"),
    (("tps20", "tps21", "ap22"), "power switch/load switch"),
    # Miscellaneous
    (("drv8", "a4988", "tmc2", "tmc5"), "motor driver"),
    (("esd", "prtr", "usblc", "tpd", "pesd", "sp05"), "ESD protection"),
    (("ds1307", "ds3231", "pcf8523", "rv3028", "rv8803"), "RTC"),
    (("at24c", "24lc", "24aa", "m24c", "cat24"), "EEPROM"),
    (("w25q", "at25", "mx25", "gd25", "is25", "sst26"), "SPI flash"),
]

_IC_DESC_KEYWORDS = [
    ("microcontroller", "microcontroller"),
    ("mcu", "microcontroller"),
    ("fpga", "FPGA"),
    ("cpld", "CPLD"),
    ("voltage regulator", "voltage regulator"),
    ("ldo", "linear regulator"),
    ("buck converter", "switching regulator"),
    ("boost converter", "switching regulator"),
    ("dc-dc", "DC-DC converter"),
    ("operational amplifier", "operational amplifier"),
    ("op-amp", "operational amplifier"),
    ("opamp", "operational amplifier"),
    ("comparator", "comparator"),
    ("adc", "ADC"),
    ("dac", "DAC"),
    ("uart", "UART interface"),
    ("usart", "UART interface"),
    ("spi", "SPI interface"),
    ("i2c", "I2C interface"),
    ("can transceiver", "CAN transceiver"),
    ("rs-485", "RS-485 transceiver"),
    ("rs-232", "RS-232 transceiver"),
    ("ethernet", "Ethernet IC"),
    ("usb", "USB IC"),
    ("motor driver", "motor driver"),
    ("gate driver", "gate driver"),
    ("led driver", "LED driver"),
    ("audio", "audio IC"),
    ("codec", "audio codec"),
    ("sensor", "sensor IC"),
    ("eeprom", "EEPROM"),
    ("flash", "flash memory"),
    ("shift register", "shift register"),
    ("multiplexer", "multiplexer"),
    ("level shift", "level shifter"),
    ("voltage reference", "voltage reference"),
    ("timer", "timer IC"),
    ("rtc", "RTC"),
    ("real-time clock", "RTC"),
    ("power supervisor", "voltage supervisor"),
    ("watchdog", "watchdog timer"),
    ("battery", "battery management"),
    ("charger", "battery charger"),
    ("rf", "RF IC"),
]


def _classify_ic_function(lib_id: str, value: str, description: str) -> str:
    """Classify IC function from library ID, value, and description.

    Three-tier lookup:
    1. KiCad stdlib library prefix (most reliable)
    2. Value/part number keyword matching
    3. Description keyword fallback
    """
    lib_lower = lib_id.lower()
    val_lower = value.lower()
    desc_lower = description.lower()

    # Skip connectors — they're analyzed for pinout but not for IC function
    lib_prefix = lib_lower.split(":")[0] if ":" in lib_lower else ""
    if lib_prefix.startswith("connector"):
        return ""

    # Tier 1: KiCad standard library prefix mapping
    for prefix, func in _IC_LIB_PREFIX_MAP.items():
        if lib_prefix == prefix or lib_lower.startswith(prefix + ":"):
            return func

    # Tier 2: Value / part number keyword matching
    for keywords, func in _IC_VALUE_KEYWORDS:
        if any(val_lower.startswith(k) for k in keywords):
            return func

    # Also check lib_id part name (after colon)
    lib_part = lib_lower.split(":")[-1] if ":" in lib_lower else ""
    if lib_part:
        for keywords, func in _IC_VALUE_KEYWORDS:
            if any(lib_part.startswith(k) for k in keywords):
                return func

    # Tier 3: Description keyword fallback
    for keyword, func in _IC_DESC_KEYWORDS:
        if keyword in desc_lower:
            return func

    return ""


def analyze_ic_pinouts(ctx: AnalysisContext,
                       target_types: set[str] | None = None) -> list[dict]:
    """Analyze each IC's pinout for datasheet cross-referencing.

    For every IC, produces a detailed per-pin analysis showing:
    - What net each pin connects to
    - What other components are on that net (with their values)
    - Whether power pins have decoupling capacitors
    - Whether input pins have pull-up/pull-down resistors
    - Pins that are unconnected (and whether they should be)
    """
    EPSILON = COORD_EPSILON
    components = ctx.components
    nets = ctx.nets
    pin_net = ctx.pin_net
    no_connects = ctx.no_connects
    comp_lookup = ctx.comp_lookup

    # Build no-connect position set
    nc_positions = set()
    for nc in no_connects:
        nc_positions.add((nc.get("_sheet", 0),
                          round(nc["x"] / EPSILON) * EPSILON,
                          round(nc["y"] / EPSILON) * EPSILON))

    results = []

    # Analyze ICs and other complex components (connectors, crystals, oscillators, etc.).
    # target_types is parameterised so the same code path can build a parallel
    # transistor_pin_analysis[] (F4) — verifying gate/source/drain wiring on
    # half-bridges is one of the highest-value review tasks and previously
    # required reconstructing the pin map from nets[].pins[] by hand.
    if target_types is None:
        target_types = {"ic", "connector", "crystal", "oscillator"}
    target_components = [c for c in components if c["type"] in target_types]

    for ic in target_components:
        ref = ic["reference"]
        pin_analysis = []
        decap_summary = {}  # net_name -> list of capacitor refs
        unconnected = []
        power_pins_detail = []
        signal_pins_detail = []

        for pin in ic.get("pins", []):
            # Ensure pin number and name are never null in output
            pin_number = pin.get("number") or ""
            pin_name = pin.get("name") or ""
            if not pin_number:
                # Fallback: use pin UUID if available, otherwise "unknown"
                pin_number = ic.get("pin_uuids", {}).get("", "unknown") if not pin_number else pin_number
                if not pin_number or pin_number == "unknown":
                    pin_number = f"unknown_{pin.get('x', 0):.0f}_{pin.get('y', 0):.0f}"

            pin_key = (ref, pin_number)
            net_name, net_info = pin_net.get(pin_key, (None, None))

            # Check if pin has a no-connect marker (by position, net flag, or
            # library-defined NC pin type).
            pin_pos = (ic.get("_sheet", 0),
                       round(pin["x"] / EPSILON) * EPSILON,
                       round(pin["y"] / EPSILON) * EPSILON)
            # The net-level no_connect flag is set when *any* point in a net's
            # union-find group is an NC marker (extract_nets line ~1490). On a
            # genuinely-connected multi-pin net it must NOT mark every pin as
            # NO_CONNECT — e.g. a stray NC marker absorbed into VBUS/GND would
            # otherwise flip all of that rail's IC pins to NO_CONNECT. Only honor
            # the net flag for single-pin nets, which covers the real case where
            # the marker sits on a short wire stub rather than exactly on the pin.
            net_pin_count = len(net_info.get("pins", [])) if net_info else 0
            has_no_connect = (
                pin_pos in nc_positions
                or pin.get("type") in ("no_connect", "unconnected")
                or bool(net_info and net_info.get("no_connect") and net_pin_count <= 1)
            )

            # Get components sharing this net
            neighbors = []
            neighbor_summary = []
            if net_info:
                neighbors = get_net_neighbors(net_info, ref)
                for nb in neighbors:
                    nb_comp = comp_lookup.get(nb["component"])
                    if nb_comp:
                        neighbor_summary.append({
                            "ref": nb["component"],
                            "value": nb_comp.get("value", ""),
                            "type": nb_comp.get("type", ""),
                            "pin": nb["pin_number"],
                            "pin_name": nb["pin_name"],
                        })

            # Classify what's connected
            connected_caps = [n for n in neighbor_summary if n["type"] == "capacitor"]
            connected_resistors = [n for n in neighbor_summary if n["type"] == "resistor"]
            connected_inductors = [n for n in neighbor_summary if n["type"] == "inductor"]

            pin_entry = {
                "pin_number": pin_number,
                "pin_name": pin_name,
                "pin_type": pin["type"],
                "net": "NO_CONNECT" if has_no_connect else (net_name or "UNCONNECTED"),
                "connected_to": neighbor_summary,
            }

            # Determine if this is functionally a power pin based on type OR net name.
            # Many lib symbols mark power pins as "input" or "passive", so also check
            # if the net is a known power rail.
            is_power_pin = pin["type"] in ("power_in", "power_out")
            if not is_power_pin and net_name:
                # Check net name against common power rail patterns
                net_upper = net_name.upper()
                is_power_pin = (
                    net_upper in ("GND", "VSS", "AGND", "DGND", "PGND",
                                  "VCC", "VDD", "AVCC", "AVDD", "DVCC", "DVDD",
                                  "VBUS", "V_USB")
                    or net_upper.startswith("+")
                    or net_upper.startswith("V+")
                )
            # Also check pin name for power pin hints
            if not is_power_pin and pin["name"]:
                pname = pin["name"].upper()
                is_power_pin = pname in (
                    "VCC", "VDD", "VSS", "GND", "AVCC", "AVDD", "DVCC", "DVDD",
                    "VIN", "VOUT", "PGND", "AGND", "DGND", "VBUS",
                )

            if is_power_pin:
                # For decoupling cap detection, only list caps directly on THIS net
                # (not the entire GND net which connects everything)
                net_is_ground = net_name and net_name.upper() in (
                    "GND", "VSS", "AGND", "DGND", "PGND")
                if net_is_ground:
                    # Don't list decoupling caps for ground pins — they're shared globally
                    pin_entry["has_decoupling_cap"] = True  # ground is always decoupled
                    pin_entry["decoupling_caps"] = []
                    pin_entry["note"] = "Ground net — decoupling caps listed on VCC/VDD pins"
                else:
                    pin_entry["has_decoupling_cap"] = len(connected_caps) > 0
                    pin_entry["decoupling_caps"] = [
                        {"ref": c["ref"], "value": c["value"]} for c in connected_caps
                    ]
                    if net_name and connected_caps:
                        decap_summary.setdefault(net_name, []).extend(
                            {"ref": c["ref"], "value": c["value"]} for c in connected_caps
                        )
                power_pins_detail.append(pin_entry)

            elif pin["type"] in ("input", "bidirectional", "open_collector", "open_emitter"):
                # Check for pull-up/pull-down resistors
                pull_resistors = []
                for r in connected_resistors:
                    r_comp = comp_lookup.get(r["ref"])
                    if r_comp:
                        # Check where the other end of the resistor goes
                        other_pin = "1" if r["pin"] == "2" else "2"
                        other_key = (r["ref"], other_pin)
                        other_net, _ = pin_net.get(other_key, (None, None))
                        if other_net in ("GND", "VSS"):
                            pull_resistors.append({
                                "ref": r["ref"], "value": r_comp["value"],
                                "direction": "pull-down", "to_net": other_net,
                            })
                        elif other_net and any(kw in other_net.upper()
                                               for kw in ("VCC", "VDD", "+3", "+5", "VBUS")):
                            pull_resistors.append({
                                "ref": r["ref"], "value": r_comp["value"],
                                "direction": "pull-up", "to_net": other_net,
                            })
                        else:
                            pull_resistors.append({
                                "ref": r["ref"], "value": r_comp["value"],
                                "direction": "series", "to_net": other_net,
                            })
                if pull_resistors:
                    pin_entry["resistors"] = pull_resistors
                signal_pins_detail.append(pin_entry)

            else:
                signal_pins_detail.append(pin_entry)

            if not net_name and not has_no_connect:
                unconnected.append(pin_entry)

            pin_analysis.append(pin_entry)

        # Deduplicate decoupling caps per net
        unique_decaps = {}
        for net_name, caps in decap_summary.items():
            seen = set()
            unique = []
            for c in caps:
                if c["ref"] not in seen:
                    seen.add(c["ref"])
                    unique.append(c)
            unique_decaps[net_name] = unique

        # Build IC analysis summary
        ic_result = {
            "reference": ref,
            "value": ic["value"],
            "type": ic["type"],
            "lib_id": ic["lib_id"],
            "mpn": ic.get("mpn", ""),
            "description": ic.get("description", ""),
            "datasheet": ic.get("datasheet", ""),
            "function": _classify_ic_function(ic["lib_id"], ic["value"], ic.get("description", "")),
            "total_pins": len(pin_analysis),
            "unconnected_pins": len(unconnected),
            "pins": sorted(pin_analysis, key=lambda p: _pin_sort_key(p["pin_number"])),
            "power_pins": power_pins_detail,
            "signal_pins": signal_pins_detail,
            "decoupling_caps_by_rail": unique_decaps,
        }

        if unconnected:
            ic_result["unconnected_pin_list"] = unconnected

        results.append(ic_result)

    return results


def _pin_sort_key(pin_num: str):
    """Sort pin numbers numerically when possible, alphabetically otherwise."""
    try:
        return (0, int(pin_num))
    except ValueError:
        return (1, pin_num)


def identify_subcircuits(ctx: AnalysisContext) -> list[dict]:
    """Identify potential subcircuit groupings around ICs."""
    components = ctx.components
    nets = ctx.nets
    pin_net = ctx.pin_net
    comp_lookup = ctx.comp_lookup
    is_power_net = ctx.is_power_net
    is_ground = ctx.is_ground
    subcircuits = []

    ics = [c for c in components if c["type"] == "ic"]

    for ic in ics:
        ref = ic["reference"]

        # Find all nets this IC connects to
        ic_nets = set()
        for pin in ic.get("pins", []):
            net_name, _ = pin_net.get((ref, pin["number"]), (None, None))
            if net_name:
                ic_nets.add(net_name)

        # Find all components that share nets with this IC (1-hop neighbors)
        # Skip power/ground nets — every IC shares VCC/GND, inflating neighbors
        neighbors = set()
        for net_name in ic_nets:
            if is_power_net(net_name) or is_ground(net_name):
                continue
            if net_name in nets:
                for p in nets[net_name]["pins"]:
                    r = p["component"]
                    if r != ref and not r.startswith("#"):
                        neighbors.add(r)

        # Build neighbor details with values
        neighbor_details = []
        for nb_ref in sorted(neighbors):
            nb_comp = comp_lookup.get(nb_ref)
            if nb_comp:
                neighbor_details.append({
                    "ref": nb_ref,
                    "value": nb_comp.get("value", ""),
                    "type": nb_comp.get("type", ""),
                })

        subcircuits.append({
            "center_ic": ref,
            "ic_value": ic["value"],
            "ic_mpn": ic.get("mpn", ""),
            "ic_lib_id": ic["lib_id"],
            "neighbor_components": neighbor_details,
            "description": ic.get("description", ""),
        })

    return subcircuits


# KiCad 5 legacy .lib pin type codes → KiCad 6+ type strings
_LEGACY_PIN_TYPE_MAP = {
    "I": "input",
    "O": "output",
    "B": "bidirectional",
    "T": "tri_state",
    "P": "passive",
    "W": "power_in",
    "w": "power_out",
    "C": "open_collector",
    "E": "open_emitter",
    "N": "unconnected",
    "U": "unspecified",
}

# Built-in pin definitions for standard KiCad 4/5 library symbols that won't
# be found in project .lib files (power/device/conn libs).  Offsets are in mm
# at the connection endpoint (where wires attach), matching the output of
# _parse_legacy_lib() after mil→mm conversion.
#
# Values derived from the most common pin positions across 1292 KiCad 4/5
# cache libraries.  Different KiCad versions use slightly different offsets
# (e.g., R/C at ±100, ±150, ±200, or ±250 mils); the wire-snap fallback
# (_snap_pins_to_wires) handles version mismatches automatically.
_M = 0.0254  # 1 mil in mm — shorthand for readability

def _conn_1xN(n):
    """Generate pin list for CONN_01X{n} (single-row, n pins, x=-200 mils)."""
    half = (n - 1) * 50  # half-span in mils
    return [{"number": str(i + 1), "name": f"P{i + 1}", "type": "passive",
             "offset": [-200 * _M, (half - i * 100) * _M]} for i in range(n)]

def _conn_2xN(n):
    """Generate pin list for CONN_02X{n} (2-row, 2n pins, x=±250 mils)."""
    half = (n - 1) * 50
    pins = []
    for i in range(n):
        y = (half - i * 100) * _M
        pins.append({"number": str(2 * i + 1), "name": f"P{2*i+1}", "type": "passive",
                      "offset": [-250 * _M, y]})
        pins.append({"number": str(2 * i + 2), "name": f"P{2*i+2}", "type": "passive",
                      "offset": [250 * _M, y]})
    return pins

_STANDARD_LIB_PINS = {
    # --- Passives (most common: ±150 mils vertical) ---
    "R": [
        {"number": "1", "name": "~", "type": "passive", "offset": [0, 150 * _M]},
        {"number": "2", "name": "~", "type": "passive", "offset": [0, -150 * _M]},
    ],
    "C": [
        {"number": "1", "name": "~", "type": "passive", "offset": [0, 150 * _M]},
        {"number": "2", "name": "~", "type": "passive", "offset": [0, -150 * _M]},
    ],
    "L": [
        {"number": "1", "name": "~", "type": "passive", "offset": [0, 150 * _M]},
        {"number": "2", "name": "~", "type": "passive", "offset": [0, -150 * _M]},
    ],
    "CP": [
        {"number": "1", "name": "~", "type": "passive", "offset": [0, 150 * _M]},
        {"number": "2", "name": "~", "type": "passive", "offset": [0, -150 * _M]},
    ],
    "CP1": [
        {"number": "1", "name": "~", "type": "passive", "offset": [0, 150 * _M]},
        {"number": "2", "name": "~", "type": "passive", "offset": [0, -150 * _M]},
    ],
    "C_Polarized": [
        {"number": "1", "name": "~", "type": "passive", "offset": [0, 150 * _M]},
        {"number": "2", "name": "~", "type": "passive", "offset": [0, -150 * _M]},
    ],
    "INDUCTOR": [
        {"number": "1", "name": "~", "type": "passive", "offset": [0, 300 * _M]},
        {"number": "2", "name": "~", "type": "passive", "offset": [0, -300 * _M]},
    ],
    # --- Small passives (±100 mils vertical) ---
    "C_Small": [
        {"number": "1", "name": "~", "type": "passive", "offset": [0, 100 * _M]},
        {"number": "2", "name": "~", "type": "passive", "offset": [0, -100 * _M]},
    ],
    "R_Small": [
        {"number": "1", "name": "~", "type": "passive", "offset": [0, 100 * _M]},
        {"number": "2", "name": "~", "type": "passive", "offset": [0, -100 * _M]},
    ],
    "L_Small": [
        {"number": "1", "name": "~", "type": "passive", "offset": [0, 100 * _M]},
        {"number": "2", "name": "~", "type": "passive", "offset": [0, -100 * _M]},
    ],
    "INDUCTOR_SMALL": [
        {"number": "1", "name": "~", "type": "passive", "offset": [-250 * _M, 0]},
        {"number": "2", "name": "~", "type": "passive", "offset": [250 * _M, 0]},
    ],
    # --- Diodes (±150 mils horizontal, A=anode K=cathode) ---
    "D": [
        {"number": "1", "name": "K", "type": "passive", "offset": [-150 * _M, 0]},
        {"number": "2", "name": "A", "type": "passive", "offset": [150 * _M, 0]},
    ],
    "D_Schottky": [
        {"number": "1", "name": "K", "type": "passive", "offset": [-150 * _M, 0]},
        {"number": "2", "name": "A", "type": "passive", "offset": [150 * _M, 0]},
    ],
    "D_Zener": [
        {"number": "1", "name": "K", "type": "passive", "offset": [-150 * _M, 0]},
        {"number": "2", "name": "A", "type": "passive", "offset": [150 * _M, 0]},
    ],
    "DIODESCH": [
        {"number": "1", "name": "K", "type": "passive", "offset": [-200 * _M, 0]},
        {"number": "2", "name": "A", "type": "passive", "offset": [200 * _M, 0]},
    ],
    "LED": [
        {"number": "1", "name": "K", "type": "passive", "offset": [-200 * _M, 0]},
        {"number": "2", "name": "A", "type": "passive", "offset": [200 * _M, 0]},
    ],
    # --- Crystals ---
    "CRYSTAL": [
        {"number": "1", "name": "1", "type": "passive", "offset": [-300 * _M, 0]},
        {"number": "2", "name": "2", "type": "passive", "offset": [300 * _M, 0]},
    ],
    "Crystal": [
        {"number": "1", "name": "1", "type": "passive", "offset": [-150 * _M, 0]},
        {"number": "2", "name": "2", "type": "passive", "offset": [150 * _M, 0]},
    ],
    "Crystal_GND24": [
        {"number": "1", "name": "1", "type": "passive", "offset": [-150 * _M, 0]},
        {"number": "2", "name": "2", "type": "passive", "offset": [0, -200 * _M]},
        {"number": "3", "name": "3", "type": "passive", "offset": [150 * _M, 0]},
        {"number": "4", "name": "4", "type": "passive", "offset": [0, 200 * _M]},
    ],
    # --- Switches ---
    "SW_PUSH": [
        {"number": "1", "name": "1", "type": "passive", "offset": [-300 * _M, 0]},
        {"number": "2", "name": "2", "type": "passive", "offset": [300 * _M, 0]},
    ],
    "SW_Push": [
        {"number": "1", "name": "1", "type": "passive", "offset": [-300 * _M, 0]},
        {"number": "2", "name": "2", "type": "passive", "offset": [300 * _M, 0]},
    ],
    # --- Transistors ---
    "Q_NPN_BEC": [
        {"number": "1", "name": "B", "type": "input", "offset": [-200 * _M, 0]},
        {"number": "2", "name": "E", "type": "passive", "offset": [100 * _M, -200 * _M]},
        {"number": "3", "name": "C", "type": "passive", "offset": [100 * _M, 200 * _M]},
    ],
    "Q_PNP_BEC": [
        {"number": "1", "name": "B", "type": "input", "offset": [-200 * _M, 0]},
        {"number": "2", "name": "E", "type": "passive", "offset": [100 * _M, 200 * _M]},
        {"number": "3", "name": "C", "type": "passive", "offset": [100 * _M, -200 * _M]},
    ],
    "Q_NMOS_GSD": [
        {"number": "1", "name": "G", "type": "input", "offset": [-200 * _M, 0]},
        {"number": "2", "name": "S", "type": "passive", "offset": [100 * _M, -200 * _M]},
        {"number": "3", "name": "D", "type": "passive", "offset": [100 * _M, 200 * _M]},
    ],
    "Q_PMOS_GSD": [
        {"number": "1", "name": "G", "type": "input", "offset": [-200 * _M, 0]},
        {"number": "2", "name": "S", "type": "passive", "offset": [100 * _M, 200 * _M]},
        {"number": "3", "name": "D", "type": "passive", "offset": [100 * _M, -200 * _M]},
    ],
    "MOSFET_N": [
        {"number": "1", "name": "G", "type": "input", "offset": [-200 * _M, 0]},
        {"number": "2", "name": "S", "type": "passive", "offset": [100 * _M, -200 * _M]},
        {"number": "3", "name": "D", "type": "passive", "offset": [100 * _M, 200 * _M]},
    ],
    "MOSFET_P": [
        {"number": "1", "name": "G", "type": "input", "offset": [-200 * _M, 0]},
        {"number": "2", "name": "S", "type": "passive", "offset": [100 * _M, 200 * _M]},
        {"number": "3", "name": "D", "type": "passive", "offset": [100 * _M, -200 * _M]},
    ],
    # --- Resistor packs ---
    "R_PACK4": [
        {"number": str(i + 1), "name": f"P{i+1}", "type": "passive",
         "offset": [-200 * _M, (150 - i * 100) * _M]} for i in range(4)
    ] + [
        {"number": str(i + 5), "name": f"R{4-i}", "type": "passive",
         "offset": [200 * _M, (-150 + i * 100) * _M]} for i in range(4)
    ],
    "R_PACK8": [
        {"number": str(i + 1), "name": f"P{i+1}", "type": "passive",
         "offset": [-200 * _M, (350 - i * 100) * _M]} for i in range(8)
    ] + [
        {"number": str(i + 9), "name": f"R{8-i}", "type": "passive",
         "offset": [200 * _M, (-350 + i * 100) * _M]} for i in range(8)
    ],
    # --- Single-row connectors (CONN_01X01 through CONN_01X20) ---
    **{f"CONN_01X{n:02d}": _conn_1xN(n) for n in range(1, 21)},
    # --- Short-form single-row connectors (CONN_1 through CONN_20) ---
    **{f"CONN_{n}": _conn_1xN(n) for n in range(1, 21)},
    # --- Dual-row connectors (CONN_02Xnn format) ---
    **{f"CONN_02X{n:02d}": _conn_2xN(n) for n in range(2, 21)},
    # --- Short-form dual-row connectors (CONN_NX2 format) ---
    **{f"CONN_{n}X2": _conn_2xN(n) for n in range(2, 21)},
    "CONN_5X2": _conn_2xN(5),
}


def _parse_legacy_lib(path: str) -> dict:
    """Parse a KiCad 5 .lib file and return symbol definitions.

    Returns dict matching extract_lib_symbols() format:
    {symbol_name: {"pins": [...], "unit_pins": {unit: [...]}, ...}}
    """
    try:
        with open(path, "r", encoding="utf-8", errors="replace") as f:
            lines = f.readlines()
    except OSError:
        return {}

    if not lines or not lines[0].startswith("EESchema-LIBRARY"):
        return {}

    MIL_TO_MM = _MIL_MM
    symbols = {}
    current_name = None
    current_aliases = []  # KH-142: track ALIAS names
    current_pins = []
    current_unit_pins = {}
    current_datasheet = ""
    in_draw = False

    for line in lines:
        line = line.strip()

        if line.startswith("DEF "):
            parts = line.split()
            if len(parts) >= 2:
                current_name = parts[1].lstrip("~")
                current_aliases = []
                current_pins = []
                current_unit_pins = {}
                current_datasheet = ""
                in_draw = False

        elif line.startswith("ALIAS ") and current_name is not None:
            # KH-142: Parse ALIAS directives — alternate names for this symbol
            current_aliases.extend(line.split()[1:])

        elif line.startswith("F3 ") and current_name is not None:
            m = re.match(r'F3\s+"([^"]*)"', line)
            if m:
                current_datasheet = m.group(1)

        elif line == "DRAW":
            in_draw = True

        elif line == "ENDDRAW":
            in_draw = False

        elif line.startswith("X ") and in_draw and current_name is not None:
            # X name number x y length dir sz1 sz2 unit convert elec_type [shape]
            parts = line.split()
            if len(parts) >= 12:
                pin_name = parts[1]
                pin_number = parts[2]
                try:
                    px = int(parts[3]) * MIL_TO_MM
                    py = int(parts[4]) * MIL_TO_MM
                    unit_num = int(parts[9])
                except (ValueError, IndexError):
                    continue
                elec_code = parts[11]
                pin_type = _LEGACY_PIN_TYPE_MAP.get(elec_code, "unspecified")

                pin = {
                    "number": pin_number,
                    "name": pin_name if pin_name != "~" else "",
                    "type": pin_type,
                    "shape": "",
                    "offset": [round(px, 4), round(py, 4)],
                }
                current_pins.append(pin)
                current_unit_pins.setdefault(unit_num, []).append(pin)

        elif line == "ENDDEF" and current_name is not None:
            # Check if multi-unit: has pins in more than one non-zero unit
            non_zero_units = {u for u in current_unit_pins if u != 0}
            has_multi_unit = len(non_zero_units) > 1

            sym_def = {
                "pins": current_pins,
                "unit_pins": current_unit_pins if has_multi_unit else None,
                "description": "",
                "keywords": "",
                "is_power": False,
                "ki_fp_filters": "",
                "alternates": None,
            }
            if current_datasheet:
                sym_def["datasheet"] = current_datasheet
            symbols[current_name] = sym_def
            # KH-142: Register same definition under each alias name
            for alias in current_aliases:
                symbols[alias.lstrip("~")] = sym_def
            current_name = None

    return symbols


def _resolve_legacy_libs(sch_path: str, all_sch_lines: dict) -> tuple:
    """Find and parse .lib files for legacy schematics.

    Args:
        sch_path: Path to the root .sch file.
        all_sch_lines: Dict mapping sheet paths to their lines (for LIBS: extraction).

    Strategy:
    1. Look for *-cache.lib alongside the root .sch file (self-contained, preferred)
    2. Parse LIBS: directives, search for each .lib in project directory tree
    3. Fall back to built-in defaults for standard KiCad symbols

    Returns:
        (symbols, resolution_info) where resolution_info describes which strategy
        was used and how many symbols came from parsed vs built-in sources.
    """
    base = Path(sch_path)
    base_dir = base.parent
    stem = base.stem

    resolution_info = {
        "cache_lib_found": False,
        "sym_lib_table_used": False,
        "libs_directive_used": False,
        "builtin_fallback_count": 0,
        "parsed_lib_count": 0,
    }

    # Strategy 1: cache lib — if present, it contains ALL symbols
    cache_path = base_dir / f"{stem}-cache.lib"
    if cache_path.exists():
        symbols = _parse_legacy_lib(str(cache_path))
        # Also add standard library fallbacks for anything missing
        for name, pins in _STANDARD_LIB_PINS.items():
            if name not in symbols:
                symbols[name] = {
                    "pins": pins, "unit_pins": None, "description": "",
                    "keywords": "", "is_power": False, "ki_fp_filters": "",
                    "alternates": None,
                }
        resolution_info["cache_lib_found"] = True
        resolution_info["parsed_lib_count"] = max(0, len(symbols) - len(_STANDARD_LIB_PINS))
        resolution_info["builtin_fallback_count"] = len(_STANDARD_LIB_PINS)
        return symbols, resolution_info

    # Strategy 2.5: Parse sym-lib-table for legacy library paths (KH-141)
    # KiCad 5 file version 4 uses sym-lib-table instead of LIBS: header directives
    sym_lib_table = base_dir / "sym-lib-table"
    if sym_lib_table.exists():
        slt_symbols = {}
        try:
            slt_root = parse_file(str(sym_lib_table))
            for lib_entry in find_all(slt_root, "lib"):
                lib_type = ""
                lib_uri = ""
                for child in lib_entry:
                    if isinstance(child, list) and len(child) >= 2:
                        if child[0] == "type":
                            lib_type = str(child[1])
                        elif child[0] == "uri":
                            lib_uri = str(child[1])
                if lib_type != "Legacy" or not lib_uri:
                    continue
                # Resolve ${KIPRJMOD} to project directory
                lib_uri = lib_uri.replace("${KIPRJMOD}", str(base_dir))
                lib_path = Path(lib_uri)
                if lib_path.exists():
                    parsed = _parse_legacy_lib(str(lib_path))
                    slt_symbols.update(parsed)
        except (ValueError, IndexError, KeyError, OSError):
            pass  # Don't crash on malformed sym-lib-table
        if slt_symbols:
            # Add standard library fallbacks
            for name, pins in _STANDARD_LIB_PINS.items():
                if name not in slt_symbols:
                    slt_symbols[name] = {
                        "pins": pins, "unit_pins": None, "description": "",
                        "keywords": "", "is_power": False, "ki_fp_filters": "",
                        "alternates": None,
                    }
            resolution_info["sym_lib_table_used"] = True
            resolution_info["parsed_lib_count"] = max(0, len(slt_symbols) - len(_STANDARD_LIB_PINS))
            resolution_info["builtin_fallback_count"] = len(_STANDARD_LIB_PINS)
            return slt_symbols, resolution_info

    # Strategy 2: collect LIBS: directives from all parsed sheets
    lib_names = []
    seen_lib_names = set()
    for sheet_lines in all_sch_lines.values():
        for line in sheet_lines:
            if line.startswith("LIBS:"):
                name = line[5:].strip()
                # Skip cache lib references (they reference the missing cache)
                if name.endswith("-cache") or name.endswith("-rescue"):
                    continue
                # Skip standard KiCad libs we handle with built-in defaults
                if name in ("power", "device", "conn", "transistors",
                            "linear", "regul", "74xx", "cmos4000",
                            "adc-dac", "memory", "xilinx", "microcontrollers",
                            "dsp", "microchip", "analog_switches",
                            "motorola", "texas", "intel", "audio",
                            "interface", "digital-audio", "philips",
                            "display", "cypress", "siliconi", "opto",
                            "atmel", "contrib", "valves"):
                    continue
                if name not in seen_lib_names:
                    lib_names.append(name)
                    seen_lib_names.add(name)

    # Search for each .lib file
    # Build search dirs: from .sch dir, walk up to 4 levels
    search_dirs = []
    d = base_dir
    for _ in range(5):
        search_dirs.append(d)
        # Also check lib/ subdirectory
        lib_subdir = d / "lib"
        if lib_subdir.is_dir():
            search_dirs.append(lib_subdir)
        parent = d.parent
        if parent == d:
            break
        d = parent

    symbols = {}
    for lib_name in lib_names:
        lib_file = f"{lib_name}.lib"
        for search_dir in search_dirs:
            candidate = search_dir / lib_file
            if candidate.exists():
                parsed = _parse_legacy_lib(str(candidate))
                symbols.update(parsed)
                break

    # Add standard library fallbacks
    for name, pins in _STANDARD_LIB_PINS.items():
        if name not in symbols:
            symbols[name] = {
                "pins": pins, "unit_pins": None, "description": "",
                "keywords": "", "is_power": False, "ki_fp_filters": "",
                "alternates": None,
            }

    resolution_info["libs_directive_used"] = bool(lib_names)
    resolution_info["parsed_lib_count"] = max(0, len(symbols) - len(_STANDARD_LIB_PINS))
    resolution_info["builtin_fallback_count"] = len(_STANDARD_LIB_PINS)
    return symbols, resolution_info


def _snap_pins_to_wires(components: list[dict], wires: list[dict]) -> None:
    """Snap component pins to nearby wire endpoints when positions don't match.

    Legacy KiCad standard library pin offsets vary between versions (±100, ±150,
    ±200, ±250 mils for R/C/L/D).  When the built-in fallback positions don't
    match the actual wire endpoints, this function finds the closest wire
    endpoint for each pin and snaps to it.

    Only snaps when the computed position has no wire endpoint within
    COORD_EPSILON, and a wire endpoint exists within _MAX_SNAP_DIST of the
    component center (generous enough for the largest standard symbols).
    """
    _MAX_SNAP_DIST = 12.0  # mm (~470 mils) — covers all standard symbols
    EPS = COORD_EPSILON

    # Build per-sheet wire endpoint set for fast lookup, and list for snapping
    wire_eps_by_sheet: dict[int, set[tuple[float, float]]] = {}
    wire_pts_by_sheet: dict[int, list[tuple[float, float]]] = {}
    for w in wires:
        sheet = w.get("_sheet", 0)
        for x, y in ((w["x1"], w["y1"]), (w["x2"], w["y2"])):
            sx = round(x / EPS) * EPS
            sy = round(y / EPS) * EPS
            wire_eps_by_sheet.setdefault(sheet, set()).add((sx, sy))
            wire_pts_by_sheet.setdefault(sheet, []).append((x, y))

    for comp in components:
        if comp.get("type") in ("power_symbol", "power_flag", "flag"):
            continue
        pins = comp.get("pins")
        if not pins:
            continue

        sheet = comp.get("_sheet", 0)
        wire_set = wire_eps_by_sheet.get(sheet, set())
        wire_list = wire_pts_by_sheet.get(sheet, [])
        cx, cy = comp["x"], comp["y"]

        # Check which pins are already matched to wire endpoints
        unmatched = []
        for pin in pins:
            sk = (round(pin["x"] / EPS) * EPS, round(pin["y"] / EPS) * EPS)
            if sk not in wire_set:
                unmatched.append(pin)

        if not unmatched:
            continue  # all pins already matched

        # Collect nearby wire endpoints (not already claimed by another pin)
        claimed = set()
        for pin in pins:
            if pin not in unmatched:
                claimed.add((round(pin["x"] / EPS) * EPS, round(pin["y"] / EPS) * EPS))

        for pin in unmatched:
            best_dist = _MAX_SNAP_DIST
            best_pt = None
            for wx, wy in wire_list:
                sk = (round(wx / EPS) * EPS, round(wy / EPS) * EPS)
                if sk in claimed:
                    continue
                dx = wx - cx
                dy = wy - cy
                dist = (dx * dx + dy * dy) ** 0.5
                if dist < best_dist:
                    # Prefer wire endpoints roughly in the direction of the
                    # original computed pin (relative to component center)
                    opx, opy = pin["x"] - cx, pin["y"] - cy
                    dot = dx * opx + dy * opy
                    if dot > 0 or (opx == 0 and opy == 0):
                        best_dist = dist
                        best_pt = (wx, wy)
            if best_pt is not None:
                pin["x"] = _snap_mil(best_pt[0])
                pin["y"] = _snap_mil(best_pt[1])
                comp["_pin_source"] = "snapped_to_wire"
                claimed.add((round(pin["x"] / EPS) * EPS, round(pin["y"] / EPS) * EPS))
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
