levi2234/ChimeraMultiFX/.agents/skills/kicad/scripts/signal_detectors.py

"""
Signal path detector functions extracted from analyze_signal_paths().

Each detector takes an AnalysisContext (ctx) and returns its detection results.
Some detectors also take prior results for cross-references.
"""

import math
import re

from kicad_utils import (
    _LOAD_TYPE_KEYWORDS,
    classify_jumper_default_state,
    format_frequency as _format_frequency,
    is_ground_name,
    is_power_net_name,
    is_usb_data_net_name,
    lookup_regulator_vref as _lookup_regulator_vref,
    lookup_switching_freq,
    match_known_switching as _match_known_switching,
    parse_value,
    parse_voltage_from_net_name as _parse_voltage_from_net_name,
)
from kicad_types import AnalysisContext
from finding_schema import make_provenance
from detector_helpers import index_two_pin_components, get_components_by_type, get_unique_ics

from lookup_helpers import get_facts, has_data, best


# ---------------------------------------------------------------------------
# Shared helpers
# ---------------------------------------------------------------------------

def _default_switching_freq(topology: str) -> float | None:
    """Fallback switching frequency estimate when part is unrecognized.

    Based on typical ranges for each topology. Conservative (low end)
    to avoid underestimating harmonic reach.
    """
    defaults = {
        'buck': 500e3,
        'boost': 500e3,
        'buck-boost': 300e3,
        'inverting': 300e3,
        'sepic': 300e3,
    }
    return defaults.get(topology.lower()) if topology else None


def _get_net_components(ctx: AnalysisContext, net_name, exclude_ref):
    """Get components on a net excluding the given component."""
    if ctx.nq:
        return ctx.nq.components_on_net(net_name, exclude_refs={exclude_ref})
    if net_name not in ctx.nets:
        return []
    result_comps = []
    for p in ctx.nets[net_name]["pins"]:
        if p["component"] == exclude_ref:
            continue
        comp = ctx.comp_lookup.get(p["component"])
        if comp:
            result_comps.append({
                "reference": p["component"],
                "type": comp["type"],
                "value": comp["value"],
                "pin_name": p.get("pin_name", ""),
                "pin_number": p["pin_number"],
            })
    return result_comps


def _classify_load(ctx: AnalysisContext, net_name, exclude_ref):
    """Classify what's on a net as a load type.

    Checks net name keywords first (motor, heater, fan, solenoid, valve,
    pump, relay, speaker, buzzer, lamp) for cases where the net name
    reveals the load type better than the connected components.
    Falls back to component-type classification.
    """
    # Net name keyword classification — catches loads driven through
    # connectors or across sheet boundaries where component type alone
    # would just show "connector" or "other"
    if net_name:
        nu = net_name.upper()
        for load_type, keywords in _LOAD_TYPE_KEYWORDS.items():
            if any(kw in nu for kw in keywords):
                return load_type

    comps = _get_net_components(ctx, net_name, exclude_ref)
    types = {c["type"] for c in comps}
    if "inductor" in types:
        return "inductive"
    if "led" in types:
        return "led"
    if types == {"resistor"} or types == {"resistor", "capacitor"}:
        return "resistive"
    if "connector" in types:
        return "connector"
    if "ic" in types:
        return "ic"
    if "transistor" in types:
        return "transistor"  # cascaded
    return "other"


def _parse_crystal_frequency(value_str: str) -> float | None:
    """Parse crystal frequency from value string or part number.

    Tries parse_value() first, then regex for embedded MHz/kHz patterns
    like "YIC-12M20P2" → 12e6, "ABM8-25.000MHZ" → 25e6.
    """
    result = parse_value(value_str)
    if result is not None:
        return result
    if not value_str:
        return None
    # Explicit MHz/kHz in value
    m = re.search(r'(\d+\.?\d*)\s*[Mm][Hh][Zz]', value_str)
    if m:
        return float(m.group(1)) * 1e6
    m = re.search(r'(\d+\.?\d*)\s*[Kk][Hh][Zz]', value_str)
    if m:
        return float(m.group(1)) * 1e3
    # MPN patterns: "YIC-12M20P2" → 12MHz, "-25M000" → 25MHz
    m = re.search(r'[-_](\d+)[Mm]\d', value_str)
    if m:
        return float(m.group(1)) * 1e6
    return None


# Typical crystal load capacitance by frequency — used as fallback when the
# crystal value string doesn't include a pF specification.
# Sources: ECS crystal catalog (2024), Abracon AB series, Murata SA series.
_CRYSTAL_DEFAULT_CL = {
    32768: 12.5,         # Watch crystals: almost universally 12.5 pF
    100e3: 12.5,
    1e6: 12.5,
    2e6: 12.5,
    3.579545e6: 20.0,    # NTSC colorburst — historically 20 pF
    4e6: 12.5,
    8e6: 18.0,
    10e6: 20.0,
    12e6: 20.0,
    16e6: 20.0,
    20e6: 18.0,
    24e6: 10.0,           # 24 MHz: 10 pF (STM32 standard)
    25e6: 10.0,           # 25 MHz: 10 pF (Ethernet PHY standard)
    26e6: 10.0,           # 26 MHz: 10 pF (Bluetooth/WiFi common)
    27e6: 10.0,
    32e6: 10.0,
    48e6: 10.0,
}


def _crystal_default_cl(freq_hz: float) -> float | None:
    """Look up typical crystal load capacitance for a given frequency.

    Returns CL in pF or None if frequency is unknown. Uses exact match
    first (within 1% tolerance), then falls back to frequency-band default.
    """
    if not freq_hz or freq_hz <= 0:
        return None
    # Exact match (within 1% tolerance for frequency rounding)
    for table_freq, cl in _CRYSTAL_DEFAULT_CL.items():
        if abs(freq_hz - table_freq) / table_freq < 0.01:
            return cl
    # Broad frequency-band fallback
    if freq_hz <= 100e3:
        return 12.5
    elif freq_hz <= 4e6:
        return 12.5
    elif freq_hz <= 16e6:
        return 18.0
    elif freq_hz <= 30e6:
        return 10.0
    else:
        return 10.0


# ---------------------------------------------------------------------------
# Divider purpose classification
# ---------------------------------------------------------------------------

def _classify_divider_purpose(divider: dict) -> str:
    """Classify a voltage divider's purpose from connected pin names.

    Examines mid_point_connections pin names and the is_feedback flag to
    determine: adc_input, feedback, bias, reference, enable_threshold, or unknown.
    """
    if divider.get("is_feedback"):
        return "feedback"

    mid_pins = divider.get("mid_point_connections", [])
    for mp in mid_pins:
        pn = mp.get("pin_name", "").upper()
        if not pn:
            continue
        # ADC / analog input
        if any(k in pn for k in ("ADC", "AIN", "ANALOG")):
            return "adc_input"
        # Feedback
        if any(k in pn for k in ("FB", "FEEDBACK")):
            return "feedback"
        # Enable / shutdown threshold
        if any(k in pn for k in ("EN", "ENABLE", "SHDN")):
            return "enable_threshold"
        # Comparator / reference / threshold
        if any(k in pn for k in ("COMP", "REF", "THRESH")):
            return "reference"
        # Bias input (opamp, comparator non-inverting/inverting)
        if any(k in pn for k in ("IN+", "IN-", "INP", "INM")):
            return "bias"

    return "unknown"


# ---------------------------------------------------------------------------
# Detectors
# ---------------------------------------------------------------------------

def detect_voltage_dividers(ctx: AnalysisContext) -> dict:
    """Detect voltage dividers and feedback networks.

    Returns dict with keys ``voltage_dividers`` and ``feedback_networks``.
    """
    voltage_dividers: list[dict] = []
    feedback_networks: list[dict] = []

    # ---- Voltage Dividers ----
    # Two resistors in series between different nets, with a mid-point net
    resistors = get_components_by_type(ctx, "resistor", with_parsed_values=True)
    resistor_nets, net_to_resistors = index_two_pin_components(ctx, resistors)

    # Check pairs of resistors that share a net (potential dividers)
    vd_seen = set()  # track (r1, r2) pairs to avoid duplicates
    for net_name, refs in net_to_resistors.items():
        if len(refs) < 2:
            continue
        for i, r1_ref in enumerate(refs):
            r1_n1, r1_n2 = resistor_nets[r1_ref]
            r1 = ctx.comp_lookup[r1_ref]
            for r2_ref in refs[i + 1:]:
                pair_key = (min(r1_ref, r2_ref), max(r1_ref, r2_ref))
                if pair_key in vd_seen:
                    continue
                vd_seen.add(pair_key)

                r2_n1, r2_n2 = resistor_nets[r2_ref]
                r2 = ctx.comp_lookup[r2_ref]

                # Find shared net (mid-point)
                r1_nets = {r1_n1, r1_n2}
                r2_nets = {r2_n1, r2_n2}
                shared = r1_nets & r2_nets
                if len(shared) != 1:
                    continue

                mid_net = shared.pop()
                top_net = (r1_nets - {mid_net}).pop()
                bot_net = (r2_nets - {mid_net}).pop()

                # Reject if mid-point is a power rail with many connections —
                # that's a power bus, not a divider output. Real divider mid-points
                # connect to 2 resistors + maybe an IC input (≤4 connections).
                if ctx.is_power_net(mid_net) or ctx.is_ground(mid_net):
                    mid_pin_count = len(ctx.nets.get(mid_net, {}).get("pins", []))
                    if mid_pin_count > 4:
                        continue

                # KH-238: Normalize orientation FIRST so the ordering of
                # r1/r2 in the outer loop can't drop valid pairs. If
                # exactly one end is ground, ensure it's bot_net. This
                # subsumes the previous "is_ground(top) and is_power(bot)"
                # swap (a strict subset of this condition) and also
                # catches the unnamed-top-net case that was getting
                # dropped by the ordering-sensitive fall-through.
                if ctx.is_ground(top_net) and not ctx.is_ground(bot_net):
                    top_net, bot_net = bot_net, top_net
                    r1, r2 = r2, r1

                # One end should be power, other should be ground (or another power)
                if not (ctx.is_power_net(top_net) and (ctx.is_ground(bot_net) or ctx.is_power_net(bot_net))):
                    # Also catch feedback dividers: output -> mid -> ground.
                    # After the KH-238 normalization above, an unnamed
                    # top_net with ground bot_net reaches this branch
                    # and passes.
                    if not ctx.is_ground(bot_net):
                        continue

                r1_val = ctx.parsed_values[r1["reference"]]
                r2_val = ctx.parsed_values[r2["reference"]]
                if r1_val <= 0 or r2_val <= 0:
                    continue
                # Extreme ratio → pull-up/pull-down pair, not a real divider.
                # 1000:1 threshold accommodates HV sensing (mains voltage,
                # battery monitoring) where 10M/10K dividers are common.
                if max(r1_val, r2_val) / min(r1_val, r2_val) > 1000:
                    continue

                # Determine which is top/bottom based on net position
                if ctx.is_ground(bot_net):
                    # r_top connects top_net to mid, r_bot connects mid to gnd
                    # Re-derive nets from current r1/r2 (may have been swapped above)
                    r1_nets_cur = set(ctx.get_two_pin_nets(r1["reference"]))
                    if top_net in r1_nets_cur:
                        r_top, r_bot = r1_val, r2_val
                        r_top_ref, r_bot_ref = r1["reference"], r2["reference"]
                    else:
                        r_top, r_bot = r2_val, r1_val
                        r_top_ref, r_bot_ref = r2["reference"], r1["reference"]

                    ratio = r_bot / (r_top + r_bot)

                    divider = {
                        "r_top": {"ref": r_top_ref, "value": ctx.comp_lookup[r_top_ref]["value"], "ohms": r_top},
                        "r_bottom": {"ref": r_bot_ref, "value": ctx.comp_lookup[r_bot_ref]["value"], "ohms": r_bot},
                        "top_net": top_net,
                        "mid_net": mid_net,
                        "bottom_net": bot_net,
                        "ratio": round(ratio, 6),
                    }

                    # Check if mid-point connects to a known feedback pin.
                    # NOTE: feedback dividers are intentionally appended to BOTH
                    # `feedback_networks` (for regulator FB matching and feedback-
                    # stability checks) AND `voltage_dividers` (so downstream
                    # consumers — notably `detect_rc_filters` at :498-503 — keep
                    # their exclusion-set correct and don't emit false-positive
                    # RC filters pairing feedback resistors with decoupling caps;
                    # `detect_power_regulators` at :1863 and `postfilter_vd_and_dedup`
                    # also consume `voltage_dividers` as a shared input).
                    #
                    # The 8c36212 polish-pass dedup that removed this double-
                    # emission caused 1742 VD-DET disappearances AND 502 cascade
                    # false-positive RC-DET findings corpus-wide. Restored
                    # 2026-05-15.
                    #
                    # If you're reading this thinking "the double-emission looks
                    # like a bug, let me clean it up": don't. The Layer 1 gate
                    # (regression/run_v14_gate.py in the harness) treats loss of
                    # v1.3.1-emitted findings as "disappeared" under
                    # `--only-deterministic`, so any dedup of this list must
                    # either preserve the double-emission OR be compensated
                    # upstream in NEW_V14_RULES at the gate side. Coordinate
                    # with the harness before changing this.
                    if mid_net in ctx.nets:
                        mid_pins = [p for p in ctx.nets[mid_net]["pins"]
                                    if p["component"] != r_top_ref
                                    and p["component"] != r_bot_ref
                                    and not p["component"].startswith("#")]
                        if mid_pins:
                            divider["mid_point_connections"] = mid_pins
                            # If connected to an IC FB pin, this is likely a feedback network
                            for mp in mid_pins:
                                if "FB" in mp.get("pin_name", "").upper():
                                    divider["is_feedback"] = True
                                    divider["detector"] = "detect_voltage_dividers"
                                    divider["rule_id"] = "VD-DET"
                                    divider["category"] = "voltage_dividers"
                                    divider["severity"] = "info"
                                    divider["confidence"] = "deterministic"
                                    divider["evidence_source"] = "topology"
                                    divider["summary"] = f"Voltage divider {r_top_ref}/{r_bot_ref}"
                                    divider["description"] = "Feedback network voltage divider detected"
                                    divider["components"] = [r_top_ref, r_bot_ref]
                                    divider["nets"] = []
                                    divider["pins"] = []
                                    divider["recommendation"] = ""
                                    divider["report_context"] = {"section": "Voltage Dividers", "impact": "", "standard_ref": ""}
                                    divider["provenance"] = make_provenance("vd_two_resistor", "deterministic", [r_top_ref, r_bot_ref])
                                    feedback_networks.append(divider)
                                    break

                    # Classify divider purpose from connected pin names
                    divider["purpose"] = _classify_divider_purpose(divider)
                    divider["detector"] = "detect_voltage_dividers"
                    divider["rule_id"] = "VD-DET"
                    divider["category"] = "voltage_dividers"
                    divider["severity"] = "info"
                    divider["confidence"] = "deterministic"
                    divider["evidence_source"] = "topology"
                    divider["summary"] = f"Voltage divider {r_top_ref}/{r_bot_ref}"
                    divider["description"] = "Resistive voltage divider detected"
                    divider["components"] = [r_top_ref, r_bot_ref]
                    divider["nets"] = []
                    divider["pins"] = []
                    divider["recommendation"] = ""
                    divider["report_context"] = {"section": "Voltage Dividers", "impact": "", "standard_ref": ""}
                    divider["provenance"] = make_provenance("vd_two_resistor", "deterministic", [r_top_ref, r_bot_ref])

                    voltage_dividers.append(divider)

    return {"voltage_dividers": voltage_dividers, "feedback_networks": feedback_networks}
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
